DragonMinded/minidragon/schematics/PCBs/2-to-4 Selector/Transistor 2-to-4 Selector.kicad_pcb

## KiCad design schematics/PCBs/2-to-4 Selector/Transistor 2-to-4 Selector.kicad_pcb (2024-02-02)

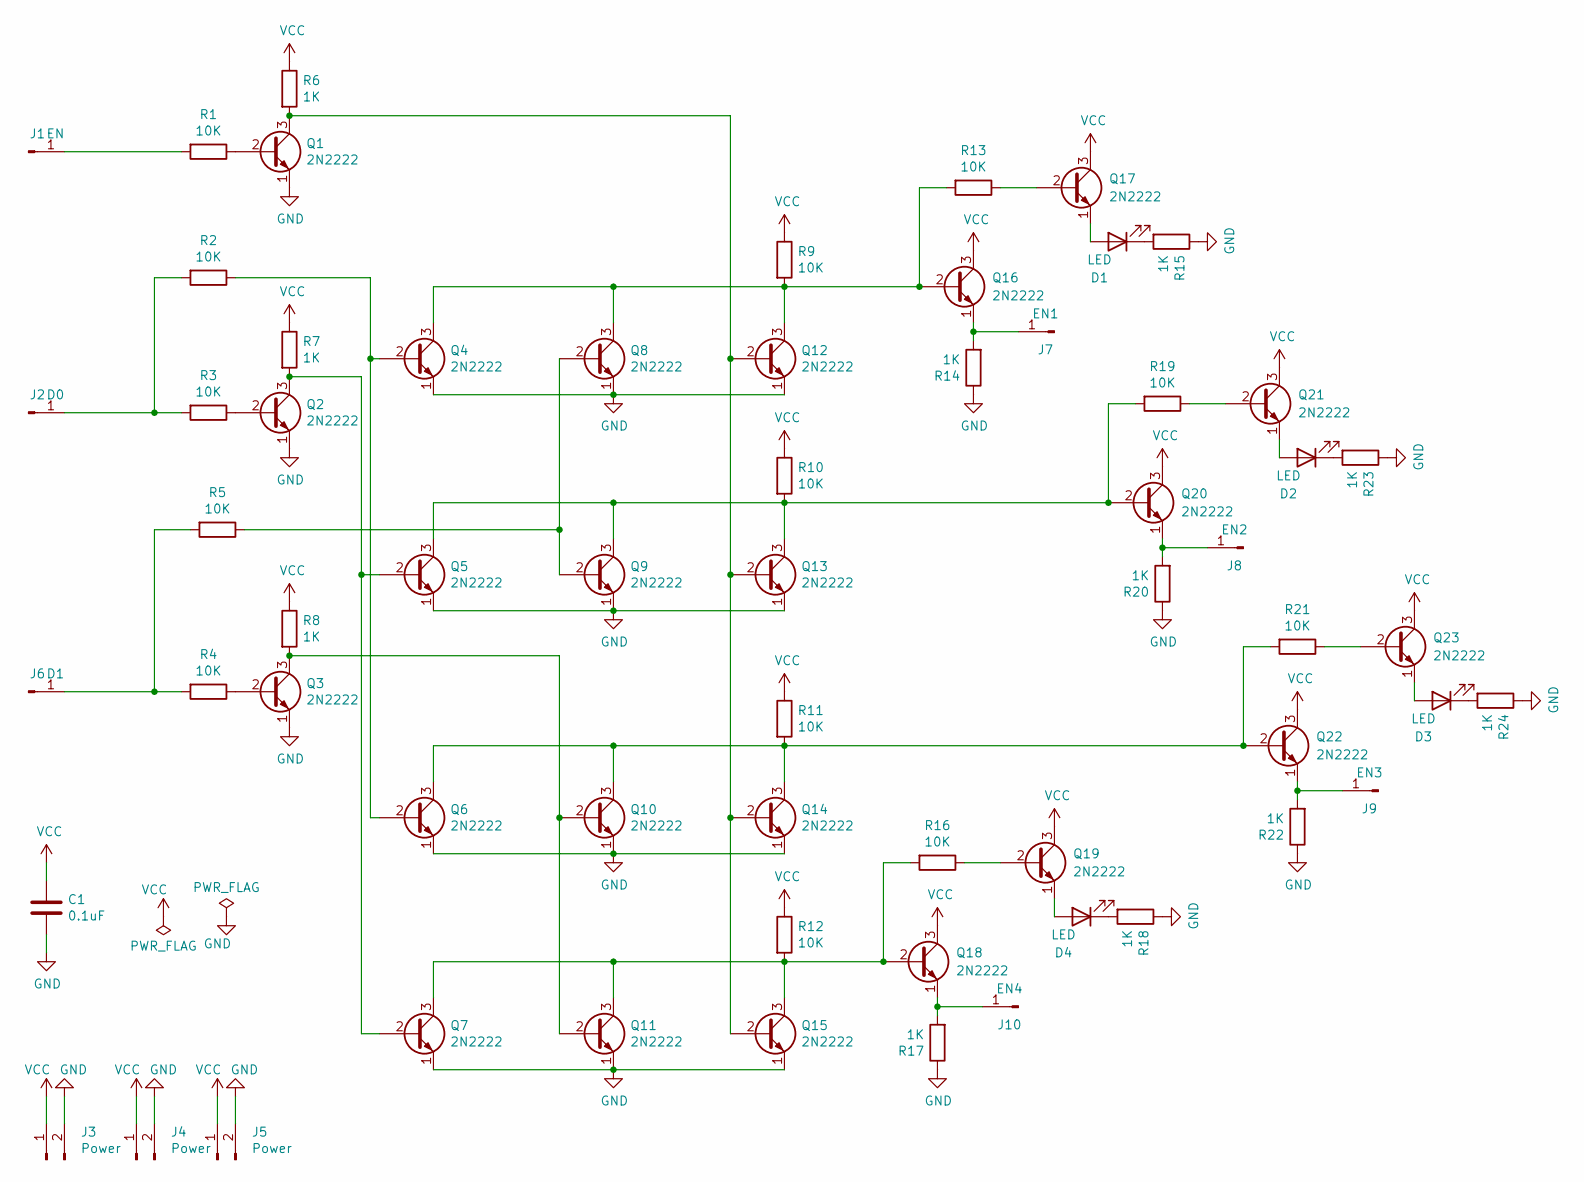
[picture p33: schematic Transistor 2-to-4 Selector.kicad_sch]

Parts:
C1: 0.1uF; C_Disc_D4.3mm_W1.9mm_P5.00mm
D1, D2, D3, D4: LED; LED_D5.0mm
J1: EN; PinHeader_1x01_P2.54mm_Vertical
J2: D0; PinHeader_1x01_P2.54mm_Vertical
J3, J4, J5: Power; PinHeader_1x02_P2.54mm_Vertical
J6: D1; PinHeader_1x01_P2.54mm_Vertical
J7: EN1; PinHeader_1x01_P2.54mm_Vertical
J8: EN2; PinHeader_1x01_P2.54mm_Vertical
J9: EN3; PinHeader_1x01_P2.54mm_Vertical
J10: EN4; PinHeader_1x01_P2.54mm_Vertical
Q1, Q2, Q3, Q4, Q5, Q6, Q7, Q8, Q9, Q10, Q11, Q12, Q13, Q14, Q15, Q16, Q17, Q18, Q19, Q20, Q21, Q22, Q23: 2N2222; TO-92_Inline
R1, R2, R3, R4, R5, R9, R10, R11, R12, R13, R16, R19, R21: 10K; R_Axial_DIN0309_L9.0mm_D3.2mm_P12.70mm_Horizontal
R6, R7, R8, R14, R15, R17, R18, R20, R22, R23, R24: 1K; R_Axial_DIN0309_L9.0mm_D3.2mm_P12.70mm_Horizontal

Connections:
GND: C1.2, J3.2, J4.2, J5.2, Q1.1 (E), Q2.1 (E), Q3.1 (E), Q4.1 (E), Q5.1 (E), Q6.1 (E), Q7.1 (E), Q8.1 (E), Q9.1 (E), Q10.1 (E), Q11.1 (E), Q12.1 (E), Q13.1 (E), Q14.1 (E), Q15.1 (E), R14.1, R15.1, R17.1, R18.1, R20.1, R22.1, R23.1, R24.1
unnamed: D1.2 (A), Q17.1 (E)
unnamed: D1.1 (K), R15.2
unnamed: D2.2 (A), Q21.1 (E)
unnamed: D2.1 (K), R23.2
unnamed: D3.2 (A), Q23.1 (E)
unnamed: D3.1 (K), R24.2
unnamed: D4.2 (A), Q19.1 (E)
unnamed: D4.1 (K), R18.2
unnamed: J1.1, R1.2
unnamed: J2.1, R2.2, R3.2
unnamed: J6.1, R4.2, R5.2
unnamed: J7.1, Q16.1 (E), R14.2
unnamed: J8.1, Q20.1 (E), R20.2
unnamed: J9.1, Q22.1 (E), R22.2
unnamed: J10.1, Q18.1 (E), R17.2
unnamed: Q1.2 (B), R1.1
unnamed: Q1.3 (C), Q12.2 (B), Q13.2 (B), Q14.2 (B), Q15.2 (B), R6.2
unnamed: Q2.2 (B), R3.1
unnamed: Q2.3 (C), Q5.2 (B), Q7.2 (B), R7.2
unnamed: Q3.2 (B), R4.1
unnamed: Q4.2 (B), Q6.2 (B), R2.1
unnamed: Q8.2 (B), Q9.2 (B), R5.1
unnamed: Q3.3 (C), Q10.2 (B), Q11.2 (B), R8.2
unnamed: Q6.3 (C), Q10.3 (C), Q14.3 (C), Q22.2 (B), R11.2, R21.2
unnamed: Q7.3 (C), Q11.3 (C), Q15.3 (C), Q18.2 (B), R12.2, R16.2
unnamed: Q4.3 (C), Q8.3 (C), Q12.3 (C), Q16.2 (B), R9.2, R13.2
unnamed: Q5.3 (C), Q9.3 (C), Q13.3 (C), Q20.2 (B), R10.2, R19.2
unnamed: Q17.2 (B), R13.1
unnamed: Q19.2 (B), R16.1
unnamed: Q21.2 (B), R19.1
unnamed: Q23.2 (B), R21.1
VCC: C1.1, J3.1, J4.1, J5.1, Q16.3 (C), Q17.3 (C), Q18.3 (C), Q19.3 (C), Q20.3 (C), Q21.3 (C), Q22.3 (C), Q23.3 (C), R6.1, R7.1, R8.1, R9.1, R10.1, R11.1, R12.1

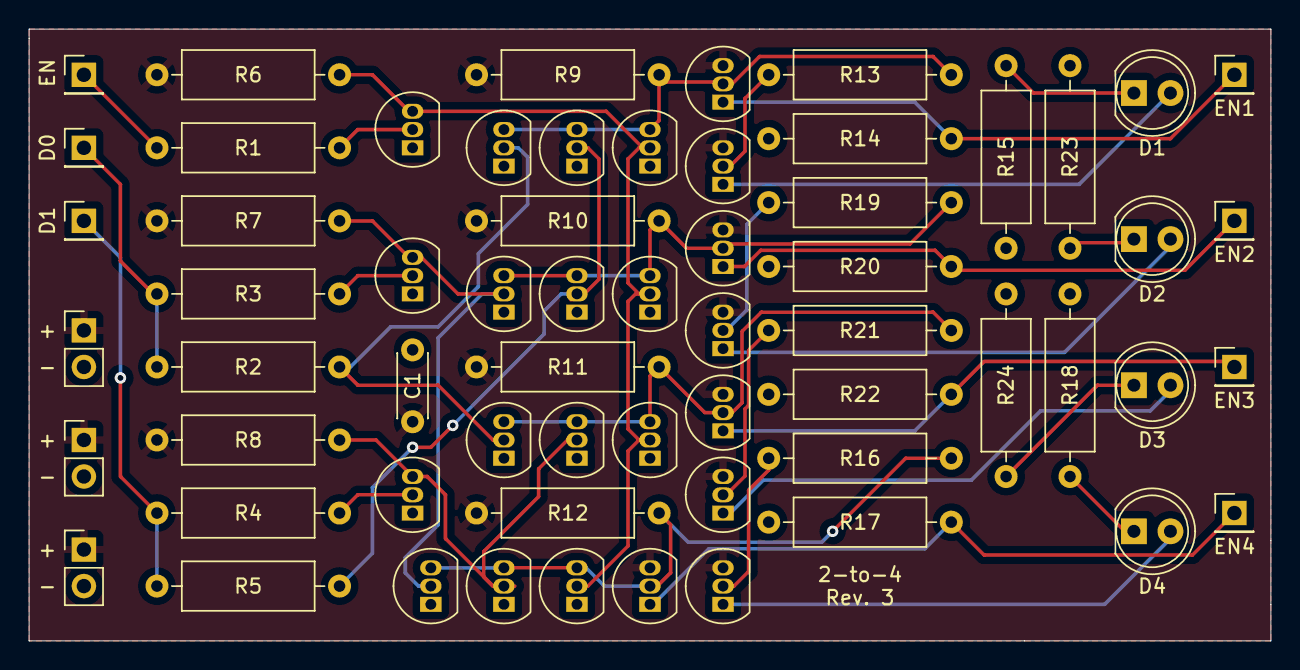
[picture p34: board Transistor 2-to-4 Selector.kicad_pcb from above]

Board: 2 copper layers, 86.4 x 42.5 mm, 62 parts (0 on the bottom side), 33 nets.
