DragonMinded/minidragon/schematics/PCBs/Logic NOT Gate/Transistor NOT Gate.kicad_pcb

## KiCad design schematics/PCBs/Logic NOT Gate/Transistor NOT Gate.kicad_pcb (2024-01-27)

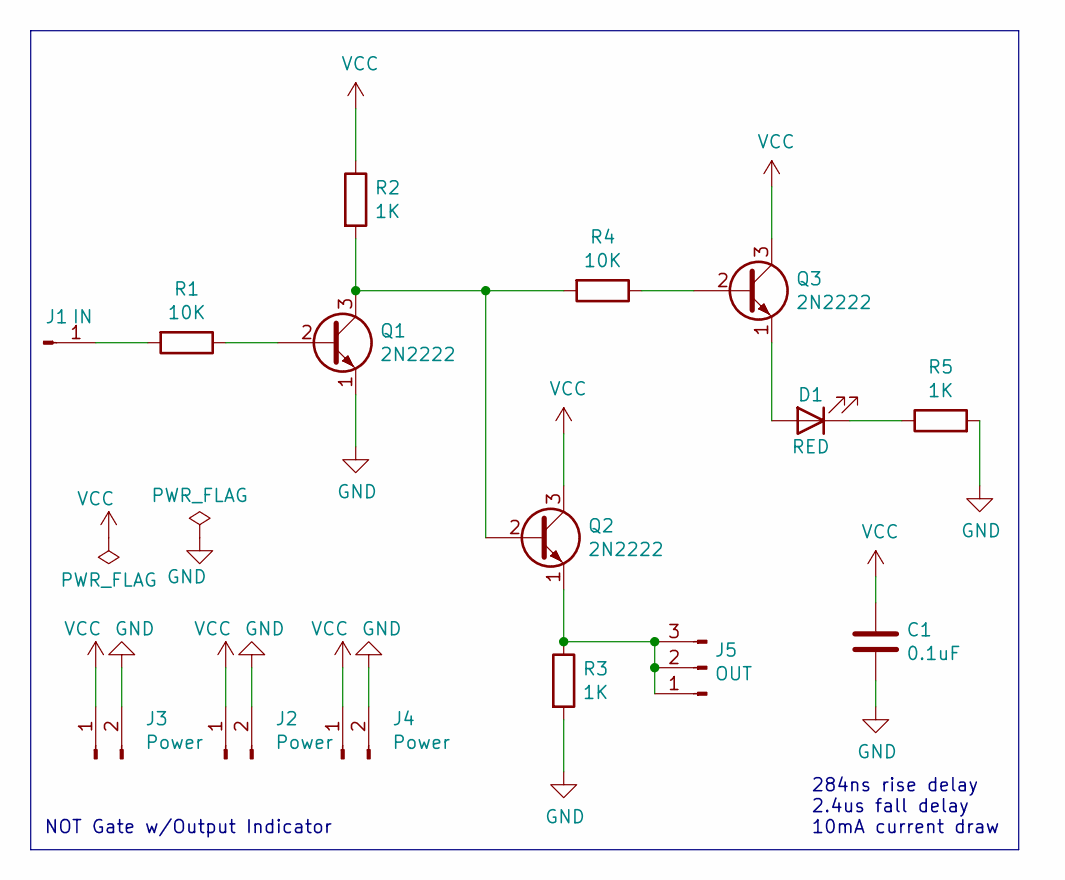
[picture p35: schematic Transistor NOT Gate.kicad_sch, NOT Gate]

Parts:
C1: 0.1uF; C_Disc_D4.3mm_W1.9mm_P5.00mm
D1: RED; LED_D5.0mm
J1: IN; PinHeader_1x01_P2.54mm_Vertical
J2, J3, J4: Power; PinHeader_1x02_P2.54mm_Vertical
J5: OUT; PinHeader_1x03_P2.54mm_Vertical
Q1, Q2, Q3: 2N2222; TO-92_Inline
R1, R4: 10K; R_Axial_DIN0309_L9.0mm_D3.2mm_P12.70mm_Horizontal
R2, R3, R5: 1K; R_Axial_DIN0309_L9.0mm_D3.2mm_P12.70mm_Horizontal

Connections:
GND: C1.2, J2.2, J3.2, J4.2, Q1.1 (E), R3.2, R5.2
unnamed: D1.2 (A), Q3.1 (E)
unnamed: D1.1 (K), R5.1
unnamed: J1.1, R1.2
unnamed: J5.1, J5.2, J5.3, Q2.1 (E), R3.1
unnamed: Q1.2 (B), R1.1
unnamed: Q1.3 (C), Q2.2 (B), R2.2, R4.2
unnamed: Q3.2 (B), R4.1
VCC: C1.1, J2.1, J3.1, J4.1, Q2.3 (C), Q3.3 (C), R2.1

Notes on the sheet:
284ns rise delay 2.4us fall delay 10mA current draw
NOT Gate w/Output Indicator

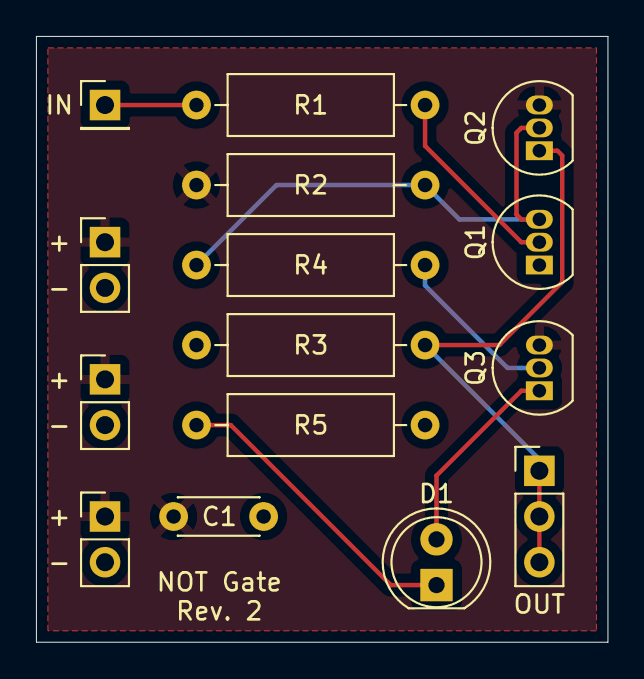
[picture p36: board Transistor NOT Gate.kicad_pcb from above]

Board: 2 copper layers, 31.8 x 33.7 mm, 15 parts (0 on the bottom side), 9 nets.
