DragonMinded/minidragon/schematics/PCBs/8-bit Bus/Transistor 8-bit Bus.kicad_pcb

## KiCad design schematics/PCBs/8-bit Bus/Transistor 8-bit Bus.kicad_pcb (2024-01-27)

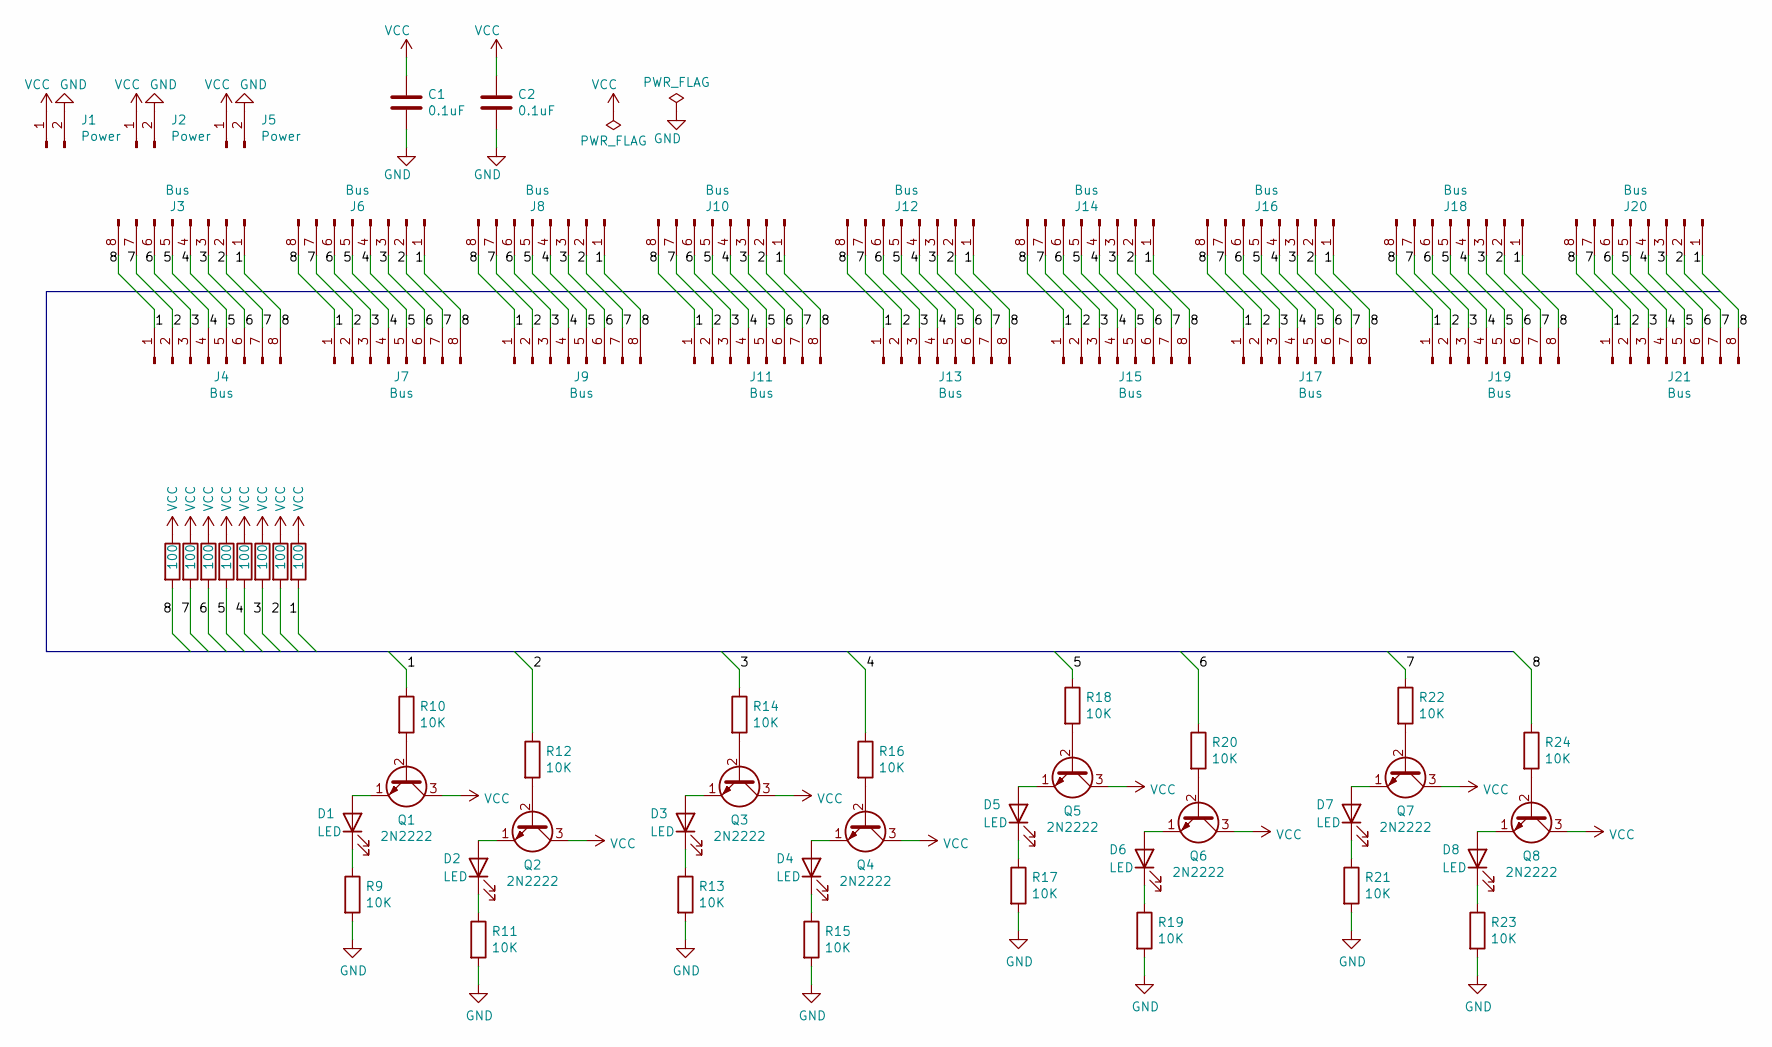
[picture p37: schematic Transistor 8-bit Bus.kicad_sch]

Parts:
C1, C2: 0.1uF; C_Disc_D4.3mm_W1.9mm_P5.00mm
D1, D2, D3, D4, D5, D6, D7, D8: LED; LED_D5.0mm
J1, J2, J5: Power; PinHeader_1x02_P2.54mm_Vertical
J3, J4, J6, J7, J8, J9, J10, J11, J12, J13, J14, J15, J16, J17, J18, J19, J20, J21: Bus; PinHeader_1x08_P2.54mm_Vertical
Q1, Q2, Q3, Q4, Q5, Q6, Q7, Q8: 2N2222; TO-92_Inline
R1, R2, R3, R4, R5, R6, R7, R8: 100; R_Axial_DIN0309_L9.0mm_D3.2mm_P12.70mm_Horizontal
R9, R10, R11, R12, R13, R14, R15, R16, R17, R18, R19, R20, R21, R22, R23, R24: 10K; R_Axial_DIN0309_L9.0mm_D3.2mm_P12.70mm_Horizontal

Connections:
/1: J3.1, J4.1, J6.1, J7.1, J8.1, J9.1, J10.1, J11.1, J12.1, J13.1, J14.1, J15.1, J16.1, J17.1, J18.1, J19.1, J20.1, J21.1, R8.2, R10.1
/2: J3.2, J4.2, J6.2, J7.2, J8.2, J9.2, J10.2, J11.2, J12.2, J13.2, J14.2, J15.2, J16.2, J17.2, J18.2, J19.2, J20.2, J21.2, R7.2, R12.1
/3: J3.3, J4.3, J6.3, J7.3, J8.3, J9.3, J10.3, J11.3, J12.3, J13.3, J14.3, J15.3, J16.3, J17.3, J18.3, J19.3, J20.3, J21.3, R6.2, R14.1
/4: J3.4, J4.4, J6.4, J7.4, J8.4, J9.4, J10.4, J11.4, J12.4, J13.4, J14.4, J15.4, J16.4, J17.4, J18.4, J19.4, J20.4, J21.4, R5.2, R16.1
/5: J3.5, J4.5, J6.5, J7.5, J8.5, J9.5, J10.5, J11.5, J12.5, J13.5, J14.5, J15.5, J16.5, J17.5, J18.5, J19.5, J20.5, J21.5, R4.2, R18.1
/6: J3.6, J4.6, J6.6, J7.6, J8.6, J9.6, J10.6, J11.6, J12.6, J13.6, J14.6, J15.6, J16.6, J17.6, J18.6, J19.6, J20.6, J21.6, R3.2, R20.1
/7: J3.7, J4.7, J6.7, J7.7, J8.7, J9.7, J10.7, J11.7, J12.7, J13.7, J14.7, J15.7, J16.7, J17.7, J18.7, J19.7, J20.7, J21.7, R2.2, R22.1
/8: J3.8, J4.8, J6.8, J7.8, J8.8, J9.8, J10.8, J11.8, J12.8, J13.8, J14.8, J15.8, J16.8, J17.8, J18.8, J19.8, J20.8, J21.8, R1.2, R24.1
GND: C1.2, C2.2, J1.2, J2.2, J5.2, R9.2, R11.2, R13.2, R15.2, R17.2, R19.2, R21.2, R23.2
unnamed: D1.2 (A), Q1.1 (E)
unnamed: D1.1 (K), R9.1
unnamed: D2.2 (A), Q2.1 (E)
unnamed: D2.1 (K), R11.1
unnamed: D3.2 (A), Q3.1 (E)
unnamed: D3.1 (K), R13.1
unnamed: D4.2 (A), Q4.1 (E)
unnamed: D4.1 (K), R15.1
unnamed: D5.2 (A), Q5.1 (E)
unnamed: D5.1 (K), R17.1
unnamed: D6.2 (A), Q6.1 (E)
unnamed: D6.1 (K), R19.1
unnamed: D7.2 (A), Q7.1 (E)
unnamed: D7.1 (K), R21.1
unnamed: D8.2 (A), Q8.1 (E)
unnamed: D8.1 (K), R23.1
unnamed: Q1.2 (B), R10.2
unnamed: Q2.2 (B), R12.2
unnamed: Q3.2 (B), R14.2
unnamed: Q4.2 (B), R16.2
unnamed: Q5.2 (B), R18.2
unnamed: Q6.2 (B), R20.2
unnamed: Q7.2 (B), R22.2
unnamed: Q8.2 (B), R24.2
VCC: C1.1, C2.1, J1.1, J2.1, J5.1, Q1.3 (C), Q2.3 (C), Q3.3 (C), Q4.3 (C), Q5.3 (C), Q6.3 (C), Q7.3 (C), Q8.3 (C), R1.1, R2.1, R3.1, R4.1, R5.1, R6.1, R7.1, R8.1

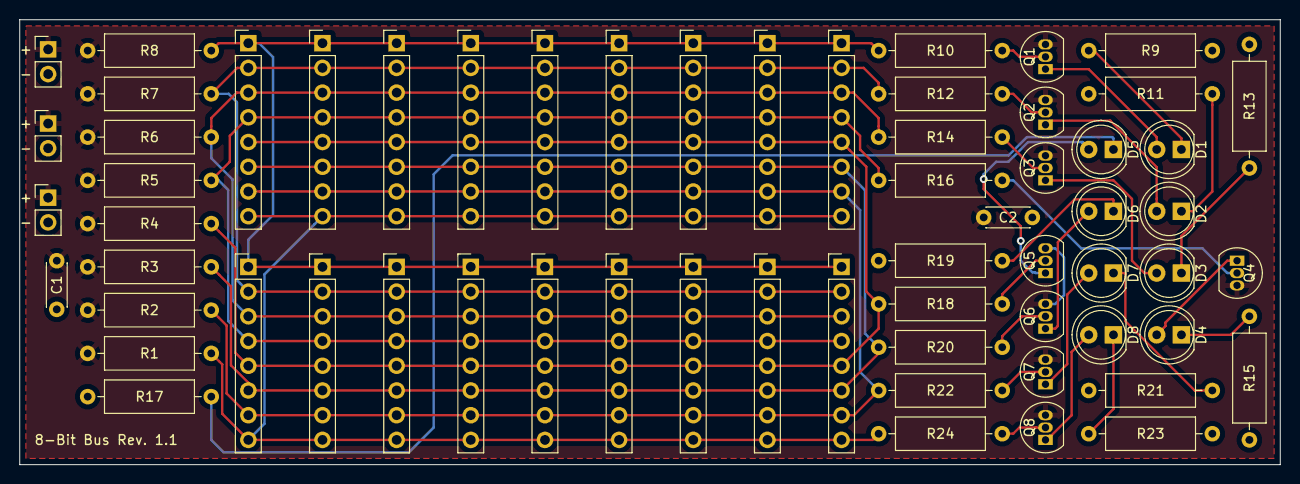
[picture p38: board Transistor 8-bit Bus.kicad_pcb from above]

Board: 2 copper layers, 129.5 x 45.7 mm, 63 parts (0 on the bottom side), 34 nets.
