DragonMinded/minidragon/schematics/PCBs/8-bit Bus Output XOR/8-bit Bus Output XOR.kicad_pcb

## KiCad design schematics/PCBs/8-bit Bus Output XOR/8-bit Bus Output XOR.kicad_pcb (2024-01-27)

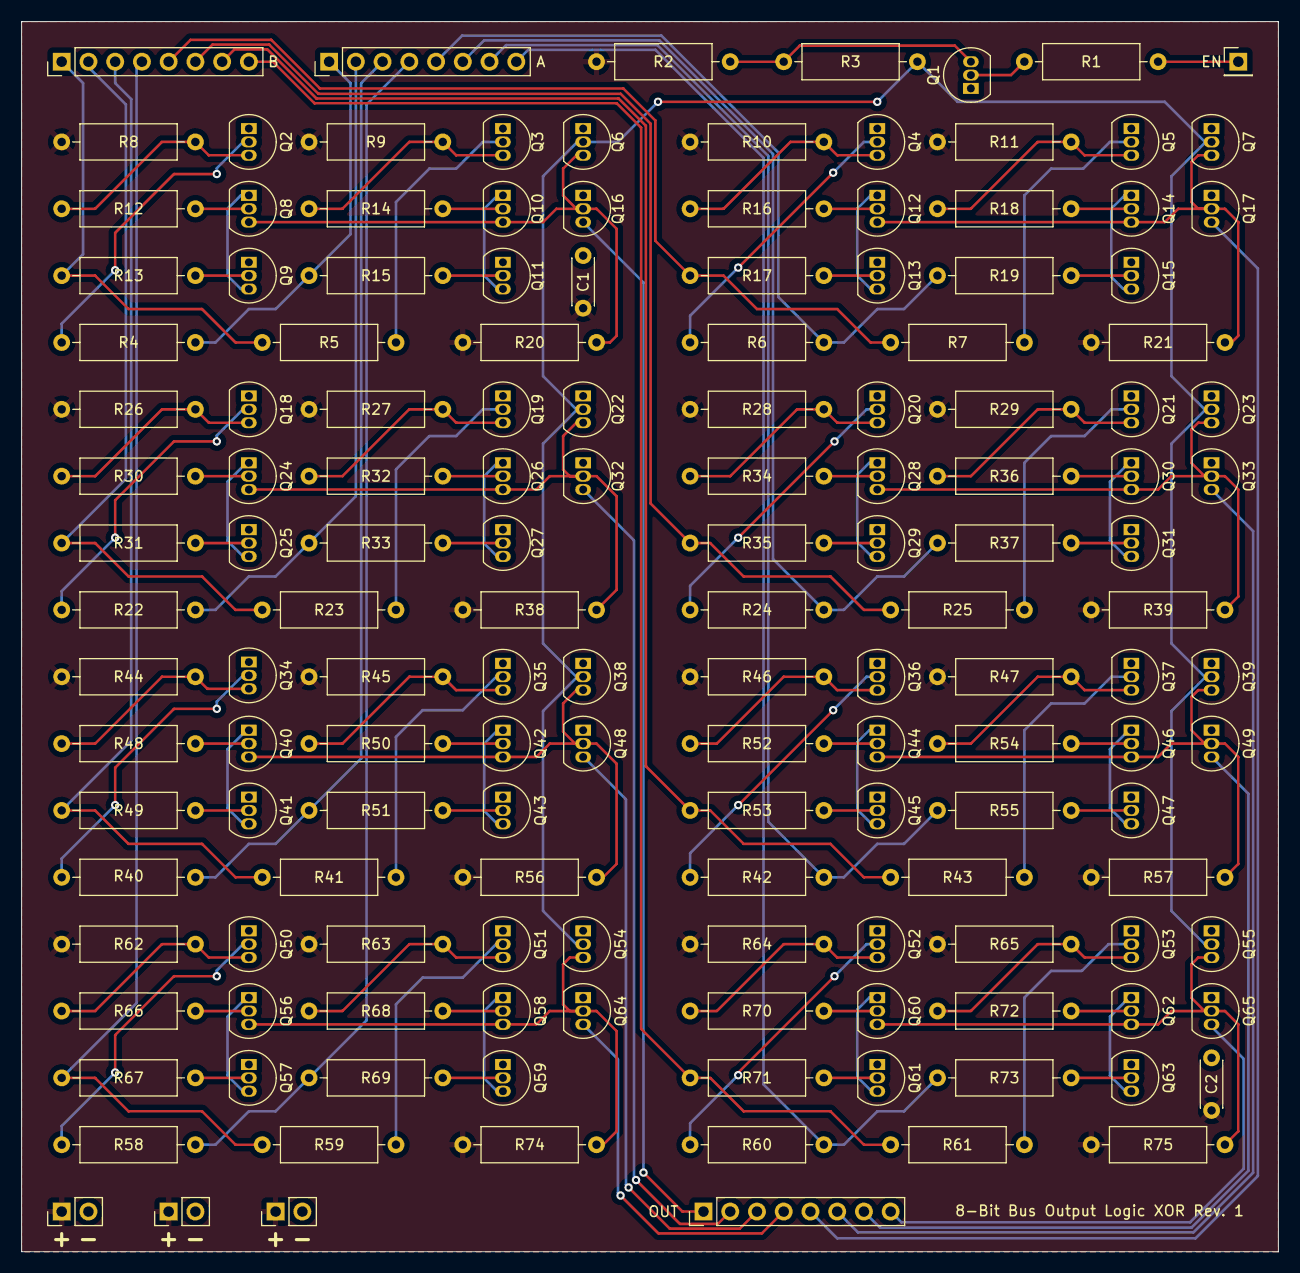
[picture p39: board 8-bit Bus Output XOR.kicad_pcb from above]

Board: 2 copper layers, 119.4 x 116.8 mm, 149 parts (0 on the bottom side), 118 nets.

Parts:
C1, C2: 0.1uF; C_Disc_D4.3mm_W1.9mm_P5.00mm
J1: EN; PinHeader_1x01_P2.54mm_Vertical
J2: A; PinHeader_1x08_P2.54mm_Vertical
J3: B; PinHeader_1x08_P2.54mm_Vertical
J4: OUT; PinHeader_1x08_P2.54mm_Vertical
J5, J6, J7: POWER; PinHeader_1x02_P2.54mm_Vertical
Q1, Q2, Q3, Q4, Q5, Q6, Q7, Q8, Q9, Q10, Q11, Q12, Q13, Q14, Q15, Q16, Q17, Q18, Q19, Q20, Q21, Q22, Q23, Q24, Q25, Q26, Q27, Q28, Q29, Q30, Q31, Q32, Q33, Q34, Q35, Q36, Q37, Q38, Q39, Q40, Q41, Q42, Q43, Q44, Q45, Q46, Q47, Q48, Q49, Q50, Q51, Q52, Q53, Q54, Q55, Q56, Q57, Q58, Q59, Q60, Q61, Q62, Q63, Q64, Q65: 2N2222; TO-92_Inline
R1, R4, R5, R6, R7, R12, R13, R14, R15, R16, R17, R18, R19, R22, R23, R24, R25, R30, R31, R32, R33, R34, R35, R36, R37, R40, R41, R42, R43, R48, R49, R50, R51, R52, R53, R54, R55, R58, R59, R60, R61, R66, R67, R68, R69, R70, R71, R72, R73: 10K; R_Axial_DIN0309_L9.0mm_D3.2mm_P12.70mm_Horizontal
R2, R8, R9, R10, R11, R20, R21, R26, R27, R28, R29, R38, R39, R44, R45, R46, R47, R56, R57, R62, R63, R64, R65, R74, R75: 1K; R_Axial_DIN0309_L9.0mm_D3.2mm_P12.70mm_Horizontal
R3: 100; R_Axial_DIN0309_L9.0mm_D3.2mm_P12.70mm_Horizontal

Connections:
/A1: J2.1, R4.2, R15.2
/A2: J2.2, R22.2, R33.2
/A3: J2.3, R40.2, R51.2
/A4: J2.4, R58.2, R69.2
/A5: J2.5, R6.2, R19.2
/A6: J2.6, R24.2, R37.2
/A7: J2.7, R42.2, R55.2
/A8: J2.8, R60.2, R73.2
/B1: J3.1, R5.2, R13.2
/B2: J3.2, R23.2, R31.2
/B3: J3.3, R41.2, R49.2
/B4: J3.4, R59.2, R67.2
/B5: J3.5, R7.2, R17.2
/B6: J3.6, R25.2, R35.2
/B7: J3.7, R43.2, R53.2
/B8: J3.8, R61.2, R71.2
/EN_INT: Q6.2 (B), Q7.2 (B), Q22.2 (B), Q23.2 (B), Q38.2 (B), Q39.2 (B), Q54.2 (B), Q55.2 (B), R3.1
/O1: J4.1, Q16.3 (C)
/O2: J4.2, Q32.3 (C)
/O3: J4.3, Q48.3 (C)
/O4: J4.4, Q64.3 (C)
/O5: J4.5, Q17.3 (C)
/O6: J4.6, Q33.3 (C)
/O7: J4.7, Q49.3 (C)
/O8: J4.8, Q65.3 (C)
GND: C1.2, C2.2, J5.2, J6.2, J7.2, Q1.1 (E), Q2.1 (E), Q3.1 (E), Q4.1 (E), Q5.1 (E), Q6.1 (E), Q7.1 (E), Q9.1 (E), Q11.1 (E), Q13.1 (E), Q15.1 (E), Q16.1 (E), Q17.1 (E), Q18.1 (E), Q19.1 (E), Q20.1 (E), Q21.1 (E), Q22.1 (E), Q23.1 (E), Q25.1 (E), Q27.1 (E), Q29.1 (E), Q31.1 (E), Q32.1 (E), Q33.1 (E), Q34.1 (E), Q35.1 (E), Q36.1 (E), Q37.1 (E), Q38.1 (E), Q39.1 (E), Q41.1 (E), Q43.1 (E), Q45.1 (E), Q47.1 (E), Q48.1 (E), Q49.1 (E), Q50.1 (E), Q51.1 (E), Q52.1 (E), Q53.1 (E), Q54.1 (E), Q55.1 (E), Q57.1 (E), Q59.1 (E), Q61.1 (E), Q63.1 (E), Q64.1 (E), Q65.1 (E)
unnamed: J1.1, R1.2
unnamed: Q1.2 (B), R1.1
unnamed: Q1.3 (C), R2.1, R3.2
unnamed: Q2.2 (B), R4.1
unnamed: Q2.3 (C), R8.2, R12.2
unnamed: Q3.2 (B), R5.1
unnamed: Q3.3 (C), R9.2, R14.2
unnamed: Q4.2 (B), R6.1
unnamed: Q4.3 (C), R10.2, R16.2
unnamed: Q5.2 (B), R7.1
unnamed: Q5.3 (C), R11.2, R18.2
unnamed: Q8.2 (B), R12.1
unnamed: Q8.1 (E), Q9.3 (C)
unnamed: Q9.2 (B), R13.1
unnamed: Q10.2 (B), R14.1
unnamed: Q6.3 (C), Q8.3 (C), Q10.3 (C), Q16.2 (B), R20.1
unnamed: Q10.1 (E), Q11.3 (C)
unnamed: Q11.2 (B), R15.1
unnamed: Q12.2 (B), R16.1
unnamed: Q7.3 (C), Q12.3 (C), Q14.3 (C), Q17.2 (B), R21.1
unnamed: Q12.1 (E), Q13.3 (C)
unnamed: Q13.2 (B), R17.1
unnamed: Q14.2 (B), R18.1
unnamed: Q14.1 (E), Q15.3 (C)
unnamed: Q15.2 (B), R19.1
unnamed: Q18.2 (B), R22.1
unnamed: Q18.3 (C), R26.2, R30.2
unnamed: Q19.2 (B), R23.1
unnamed: Q19.3 (C), R27.2, R32.2
unnamed: Q20.2 (B), R24.1
unnamed: Q20.3 (C), R28.2, R34.2
unnamed: Q21.2 (B), R25.1
unnamed: Q21.3 (C), R29.2, R36.2
unnamed: Q22.3 (C), Q24.3 (C), Q26.3 (C), Q32.2 (B), R38.1
unnamed: Q23.3 (C), Q28.3 (C), Q30.3 (C), Q33.2 (B), R39.1
unnamed: Q24.2 (B), R30.1
unnamed: Q24.1 (E), Q25.3 (C)
unnamed: Q25.2 (B), R31.1
unnamed: Q26.2 (B), R32.1
unnamed: Q26.1 (E), Q27.3 (C)
unnamed: Q27.2 (B), R33.1
unnamed: Q28.2 (B), R34.1
unnamed: Q28.1 (E), Q29.3 (C)
unnamed: Q29.2 (B), R35.1
unnamed: Q30.2 (B), R36.1
unnamed: Q30.1 (E), Q31.3 (C)
unnamed: Q31.2 (B), R37.1
unnamed: Q34.2 (B), R40.1
unnamed: Q34.3 (C), R44.2, R48.2
unnamed: Q35.2 (B), R41.1
unnamed: Q35.3 (C), R45.2, R50.2
unnamed: Q36.2 (B), R42.1
unnamed: Q36.3 (C), R46.2, R52.2
unnamed: Q37.2 (B), R43.1
unnamed: Q37.3 (C), R47.2, R54.2
unnamed: Q38.3 (C), Q40.3 (C), Q42.3 (C), Q48.2 (B), R56.1
unnamed: Q39.3 (C), Q44.3 (C), Q46.3 (C), Q49.2 (B), R57.1
unnamed: Q40.2 (B), R48.1
unnamed: Q40.1 (E), Q41.3 (C)
unnamed: Q41.2 (B), R49.1
unnamed: Q42.2 (B), R50.1
unnamed: Q42.1 (E), Q43.3 (C)
unnamed: Q43.2 (B), R51.1
unnamed: Q44.2 (B), R52.1
unnamed: Q44.1 (E), Q45.3 (C)
unnamed: Q45.2 (B), R53.1
unnamed: Q46.2 (B), R54.1
unnamed: Q46.1 (E), Q47.3 (C)
unnamed: Q47.2 (B), R55.1
unnamed: Q50.2 (B), R58.1
unnamed: Q50.3 (C), R62.2, R66.2
unnamed: Q51.2 (B), R59.1
unnamed: Q51.3 (C), R63.2, R68.2
unnamed: Q52.2 (B), R60.1
unnamed: Q52.3 (C), R64.2, R70.2
unnamed: Q53.2 (B), R61.1
unnamed: Q53.3 (C), R65.2, R72.2
unnamed: Q54.3 (C), Q56.3 (C), Q58.3 (C), Q64.2 (B), R74.1
unnamed: Q55.3 (C), Q60.3 (C), Q62.3 (C), Q65.2 (B), R75.1
unnamed: Q56.2 (B), R66.1
unnamed: Q56.1 (E), Q57.3 (C)
unnamed: Q57.2 (B), R67.1
unnamed: Q58.2 (B), R68.1
unnamed: Q58.1 (E), Q59.3 (C)
unnamed: Q59.2 (B), R69.1
unnamed: Q60.2 (B), R70.1
unnamed: Q60.1 (E), Q61.3 (C)
unnamed: Q61.2 (B), R71.1
unnamed: Q62.2 (B), R72.1
unnamed: Q62.1 (E), Q63.3 (C)
unnamed: Q63.2 (B), R73.1
VCC: C1.1, C2.1, J5.1, J6.1, J7.1, R2.2, R8.1, R9.1, R10.1, R11.1, R20.2, R21.2, R26.1, R27.1, R28.1, R29.1, R38.2, R39.2, R44.1, R45.1, R46.1, R47.1, R56.2, R57.2, R62.1, R63.1, R64.1, R65.1, R74.2, R75.2
