DragonMinded/minidragon/schematics/PCBs/Carry Out Selector/Carry Out Selector.kicad_pcb

## KiCad design schematics/PCBs/Carry Out Selector/Carry Out Selector.kicad_pcb (2024-01-27)

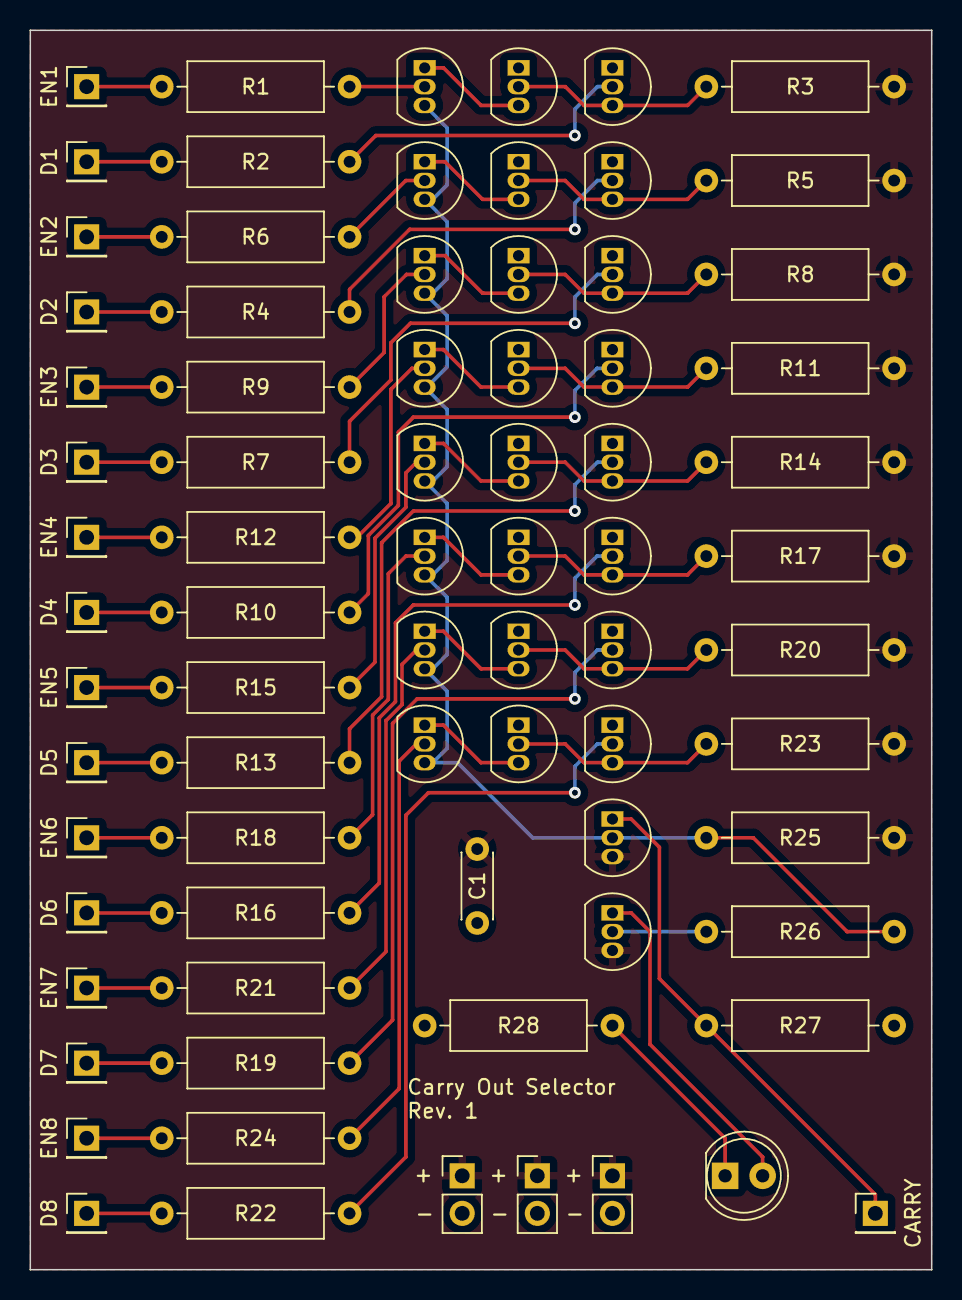
[picture p40: board Carry Out Selector.kicad_pcb from above]

Board: 2 copper layers, 61.0 x 83.8 mm, 76 parts (0 on the bottom side), 55 nets.

Parts:
C1: 0.1uF; C_Disc_D4.3mm_W1.9mm_P5.00mm
D1: LED; LED_D5.0mm
J1, J2, J3: POWER; PinHeader_1x02_P2.54mm_Vertical
J4: D1; PinHeader_1x01_P2.54mm_Vertical
J5: EN1; PinHeader_1x01_P2.54mm_Vertical
J6: D2; PinHeader_1x01_P2.54mm_Vertical
J7: EN2; PinHeader_1x01_P2.54mm_Vertical
J8: D3; PinHeader_1x01_P2.54mm_Vertical
J9: EN3; PinHeader_1x01_P2.54mm_Vertical
J10: D4; PinHeader_1x01_P2.54mm_Vertical
J11: EN4; PinHeader_1x01_P2.54mm_Vertical
J12: D5; PinHeader_1x01_P2.54mm_Vertical
J13: EN5; PinHeader_1x01_P2.54mm_Vertical
J14: D6; PinHeader_1x01_P2.54mm_Vertical
J15: EN6; PinHeader_1x01_P2.54mm_Vertical
J16: D7; PinHeader_1x01_P2.54mm_Vertical
J17: EN7; PinHeader_1x01_P2.54mm_Vertical
J18: D8; PinHeader_1x01_P2.54mm_Vertical
J19: EN8; PinHeader_1x01_P2.54mm_Vertical
J20: CARRY; PinHeader_1x01_P2.54mm_Vertical
Q1, Q2, Q3, Q4, Q5, Q6, Q7, Q8, Q9, Q10, Q11, Q12, Q13, Q14, Q15, Q16, Q17, Q18, Q19, Q20, Q21, Q22, Q23, Q24, Q25, Q26: 2N2222; TO-92_Inline
R1, R2, R4, R6, R7, R9, R10, R12, R13, R15, R16, R18, R19, R21, R22, R24, R26: 10K; R_Axial_DIN0309_L9.0mm_D3.2mm_P12.70mm_Horizontal
R3, R5, R8, R11, R14, R17, R20, R23, R25, R27, R28: 1K; R_Axial_DIN0309_L9.0mm_D3.2mm_P12.70mm_Horizontal

Connections:
/COMB_BUS: Q1.3 (C), Q5.3 (C), Q8.3 (C), Q11.3 (C), Q14.3 (C), Q17.3 (C), Q20.3 (C), Q23.3 (C), Q25.2 (B), R25.1, R26.2
GND: C1.2, J1.2, J2.2, J3.2, Q2.1 (E), Q3.1 (E), Q4.1 (E), Q6.1 (E), Q7.1 (E), Q9.1 (E), Q10.1 (E), Q12.1 (E), Q13.1 (E), Q15.1 (E), Q16.1 (E), Q18.1 (E), Q19.1 (E), Q21.1 (E), Q22.1 (E), Q24.1 (E), R27.1, R28.1
unnamed: D1.2 (A), Q26.1 (E)
unnamed: D1.1 (K), R28.2
unnamed: J4.1, R2.2
unnamed: J5.1, R1.2
unnamed: J6.1, R4.2
unnamed: J7.1, R6.2
unnamed: J8.1, R7.2
unnamed: J9.1, R9.2
unnamed: J10.1, R10.2
unnamed: J11.1, R12.2
unnamed: J12.1, R13.2
unnamed: J13.1, R15.2
unnamed: J14.1, R16.2
unnamed: J15.1, R18.2
unnamed: J16.1, R19.2
unnamed: J17.1, R21.2
unnamed: J18.1, R22.2
unnamed: J19.1, R24.2
unnamed: J20.1, Q25.1 (E), R27.2
unnamed: Q1.2 (B), R1.1
unnamed: Q1.1 (E), Q2.3 (C)
unnamed: Q2.2 (B), Q3.3 (C), R3.1
unnamed: Q3.2 (B), R2.1
unnamed: Q4.2 (B), R4.1
unnamed: Q4.3 (C), Q6.2 (B), R5.1
unnamed: Q5.2 (B), R6.1
unnamed: Q5.1 (E), Q6.3 (C)
unnamed: Q7.2 (B), R7.1
unnamed: Q7.3 (C), Q9.2 (B), R8.1
unnamed: Q8.2 (B), R9.1
unnamed: Q8.1 (E), Q9.3 (C)
unnamed: Q10.2 (B), R10.1
unnamed: Q10.3 (C), Q12.2 (B), R11.1
unnamed: Q11.2 (B), R12.1
unnamed: Q11.1 (E), Q12.3 (C)
unnamed: Q13.2 (B), R13.1
unnamed: Q13.3 (C), Q15.2 (B), R14.1
unnamed: Q14.2 (B), R15.1
unnamed: Q14.1 (E), Q15.3 (C)
unnamed: Q16.2 (B), R16.1
unnamed: Q16.3 (C), Q18.2 (B), R17.1
unnamed: Q17.2 (B), R18.1
unnamed: Q17.1 (E), Q18.3 (C)
unnamed: Q19.2 (B), R19.1
unnamed: Q19.3 (C), Q21.2 (B), R20.1
unnamed: Q20.2 (B), R21.1
unnamed: Q20.1 (E), Q21.3 (C)
unnamed: Q22.2 (B), R22.1
unnamed: Q22.3 (C), Q24.2 (B), R23.1
unnamed: Q23.2 (B), R24.1
unnamed: Q23.1 (E), Q24.3 (C)
unnamed: Q26.2 (B), R26.1
VCC: C1.1, J1.1, J2.1, J3.1, Q25.3 (C), Q26.3 (C), R3.2, R5.2, R8.2, R11.2, R14.2, R17.2, R20.2, R23.2, R25.2
