DragonMinded/minidragon/schematics/PCBs/D Flip Flop/Transistor D Flip Flop.kicad_pcb

## KiCad design schematics/PCBs/D Flip Flop/Transistor D Flip Flop.kicad_pcb (2024-01-27)

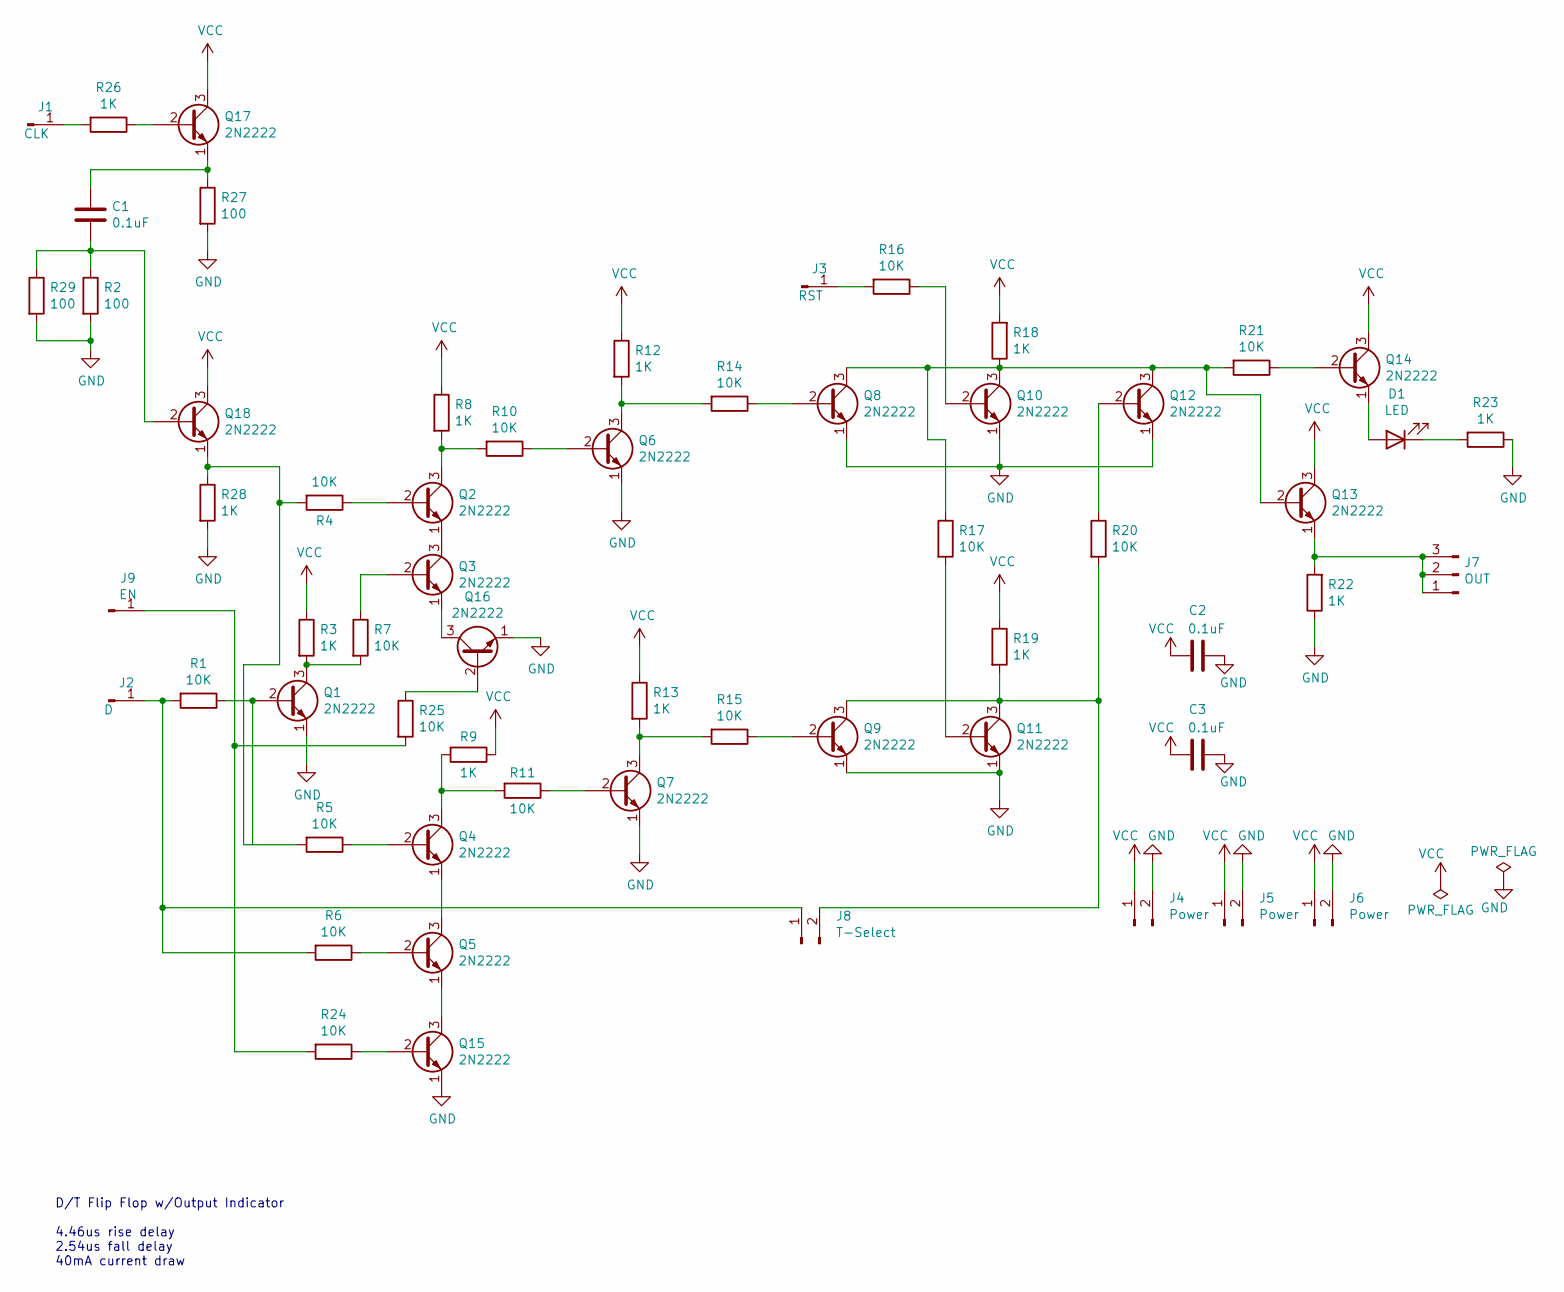
[picture p41: schematic Transistor D Flip Flop.kicad_sch, D Flip Flop]

Parts:
C1, C2, C3: 0.1uF; C_Disc_D4.3mm_W1.9mm_P5.00mm
D1: LED; LED_D5.0mm
J1: CLK; PinHeader_1x01_P2.54mm_Vertical
J2: D; PinHeader_1x01_P2.54mm_Vertical
J3: RST; PinHeader_1x01_P2.54mm_Vertical
J4, J5, J6: Power; PinHeader_1x02_P2.54mm_Vertical
J7: OUT; PinHeader_1x03_P2.54mm_Vertical
J8: T-Select; PinHeader_1x02_P2.54mm_Vertical
J9: EN; PinHeader_1x01_P2.54mm_Vertical
Q1, Q2, Q3, Q4, Q5, Q6, Q7, Q8, Q9, Q10, Q11, Q12, Q13, Q14, Q15, Q16, Q17, Q18: 2N2222; TO-92_Inline
R1, R4, R5, R6, R7, R10, R11, R14, R15, R16, R17, R20, R21, R24, R25: 10K; R_Axial_DIN0309_L9.0mm_D3.2mm_P12.70mm_Horizontal
R2, R27, R29: 100; R_Axial_DIN0309_L9.0mm_D3.2mm_P12.70mm_Horizontal
R3, R8, R9, R12, R13, R18, R19, R22, R23, R26, R28: 1K; R_Axial_DIN0309_L9.0mm_D3.2mm_P12.70mm_Horizontal

Connections:
GND: C2.1, C3.1, J4.2, J5.2, J6.2, Q1.1 (E), Q6.1 (E), Q7.1 (E), Q8.1 (E), Q9.1 (E), Q10.1 (E), Q11.1 (E), Q12.1 (E), Q15.1 (E), Q16.1 (E), R2.2, R22.1, R23.1, R27.2, R28.2, R29.2
unnamed: D1.2 (A), Q14.1 (E)
unnamed: D1.1 (K), R23.2
unnamed: J1.1, R26.2
unnamed: J2.1, J8.1, R1.2, R6.2
unnamed: J3.1, R16.2
unnamed: J7.1, J7.2, J7.3, Q13.1 (E), R22.2
unnamed: J8.2, Q9.3 (C), Q11.3 (C), R19.2, R20.2
unnamed: J9.1, R24.2, R25.2
unnamed: Q1.2 (B), R1.1
unnamed: Q1.3 (C), R3.2, R7.2
unnamed: Q2.2 (B), R4.1
unnamed: Q2.3 (C), R8.2, R10.2
unnamed: Q2.1 (E), Q3.3 (C)
unnamed: Q3.2 (B), R7.1
unnamed: Q4.2 (B), R5.1
unnamed: Q4.3 (C), R9.2, R11.2
unnamed: Q4.1 (E), Q5.3 (C)
unnamed: Q5.2 (B), R6.1
unnamed: Q6.2 (B), R10.1
unnamed: Q6.3 (C), R12.2, R14.2
unnamed: Q7.2 (B), R11.1
unnamed: Q7.3 (C), R13.2, R15.2
unnamed: Q8.2 (B), R14.1
unnamed: Q9.2 (B), R15.1
unnamed: Q10.2 (B), R16.1
unnamed: Q8.3 (C), Q10.3 (C), Q12.3 (C), Q13.2 (B), R17.1, R18.1, R21.2
unnamed: Q11.2 (B), R17.2
unnamed: Q12.2 (B), R20.1
unnamed: Q14.2 (B), R21.1
unnamed: Q15.2 (B), R24.1
unnamed: Q5.1 (E), Q15.3 (C)
unnamed: Q16.2 (B), R25.1
unnamed: Q3.1 (E), Q16.3 (C)
unnamed: Q17.2 (B), R26.1
unnamed: C1.1, Q17.1 (E), R27.1
unnamed: C1.2, Q18.2 (B), R2.1, R29.1
unnamed: Q18.1 (E), R4.2, R5.2, R28.1
VCC: C2.2, C3.2, J4.1, J5.1, J6.1, Q13.3 (C), Q14.3 (C), Q17.3 (C), Q18.3 (C), R3.1, R8.1, R9.1, R12.1, R13.1, R18.2, R19.1

Notes on the sheet:
D/T Flip Flop w/Output Indicator 4.46us rise delay 2.54us fall delay 40mA current draw

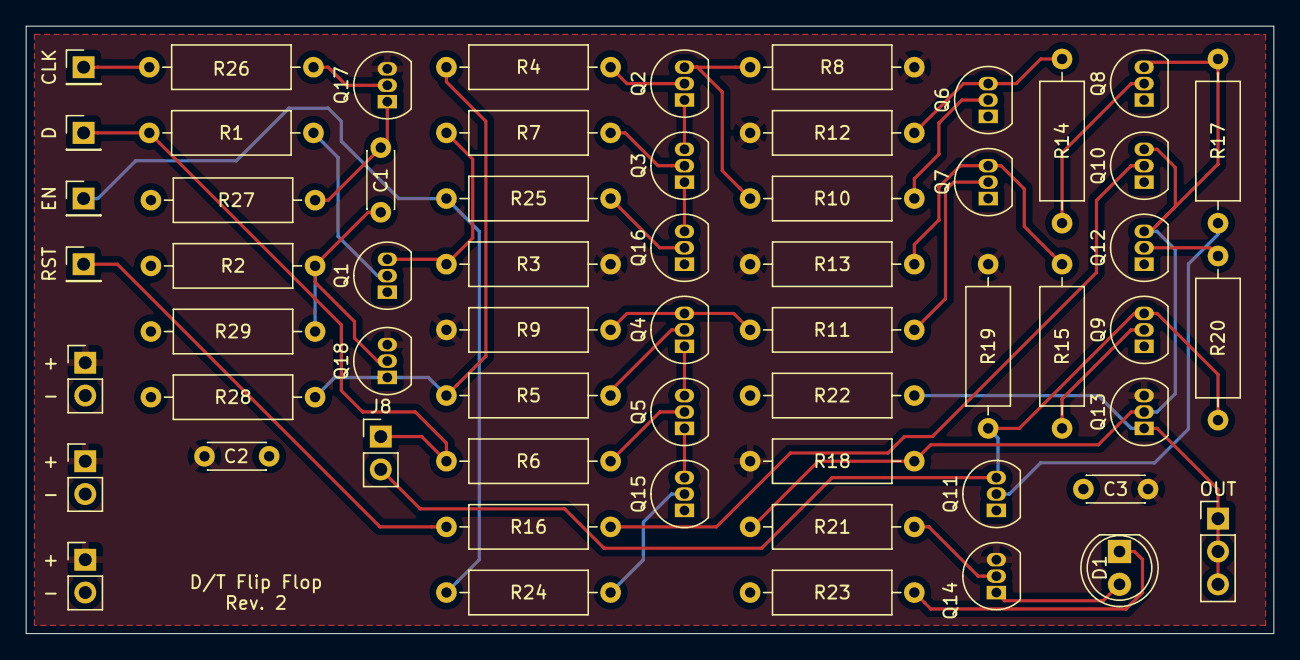
[picture p42: board Transistor D Flip Flop.kicad_pcb from above]

Board: 2 copper layers, 96.5 x 47.0 mm, 60 parts (0 on the bottom side), 39 nets.
