DragonMinded/minidragon/schematics/PCBs/Zero Detector/Zero Detector.kicad_pcb

## KiCad design schematics/PCBs/Zero Detector/Zero Detector.kicad_pcb (2024-01-27)

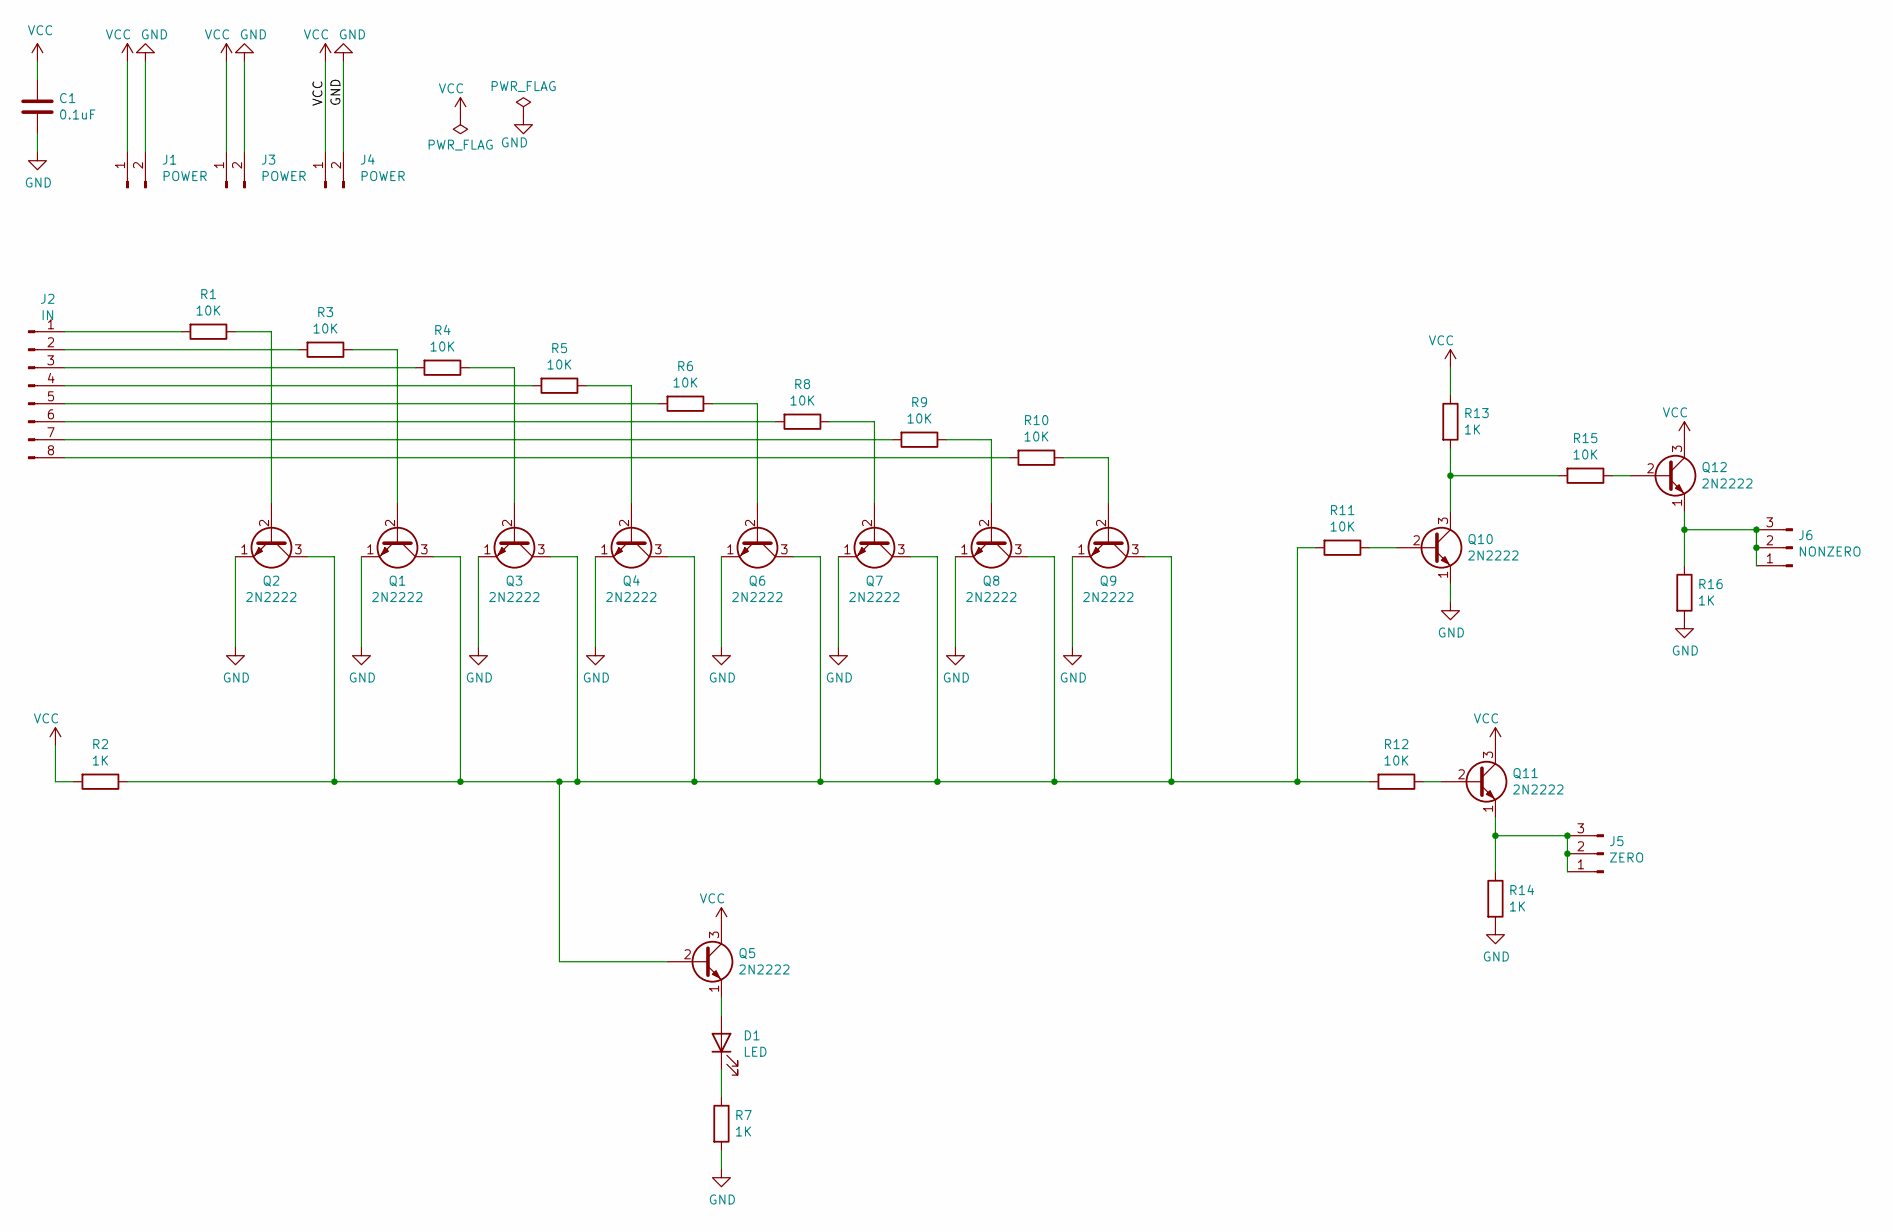
[picture p43: schematic Zero Detector.kicad_sch]

Parts:
C1: 0.1uF; C_Disc_D4.3mm_W1.9mm_P5.00mm
D1: LED; LED_D5.0mm
J1, J3, J4: POWER; PinHeader_1x02_P2.54mm_Vertical
J2: IN; PinHeader_1x08_P2.54mm_Vertical
J5: ZERO; PinHeader_1x03_P2.54mm_Vertical
J6: NONZERO; PinHeader_1x03_P2.54mm_Vertical
Q1, Q2, Q3, Q4, Q5, Q6, Q7, Q8, Q9, Q10, Q11, Q12: 2N2222; TO-92_Inline
R1, R3, R4, R5, R6, R8, R9, R10, R11, R12, R15: 10K; R_Axial_DIN0309_L9.0mm_D3.2mm_P12.70mm_Horizontal
R2, R7, R13, R14, R16: 1K; R_Axial_DIN0309_L9.0mm_D3.2mm_P12.70mm_Horizontal

Connections:
GND: C1.2, J1.2, J3.2, J4.2, Q1.1 (E), Q2.1 (E), Q3.1 (E), Q4.1 (E), Q6.1 (E), Q7.1 (E), Q8.1 (E), Q9.1 (E), Q10.1 (E), R7.2, R14.2, R16.2
unnamed: D1.2 (A), Q5.1 (E)
unnamed: D1.1 (K), R7.1
unnamed: J2.1, R1.2
unnamed: J2.2, R3.2
unnamed: J2.3, R4.2
unnamed: J2.4, R5.2
unnamed: J2.5, R6.2
unnamed: J2.6, R8.2
unnamed: J2.7, R9.2
unnamed: J2.8, R10.2
unnamed: J5.1, J5.2, J5.3, Q11.1 (E), R14.1
unnamed: J6.1, J6.2, J6.3, Q12.1 (E), R16.1
unnamed: Q1.2 (B), R3.1
unnamed: Q1.3 (C), Q2.3 (C), Q3.3 (C), Q4.3 (C), Q5.2 (B), Q6.3 (C), Q7.3 (C), Q8.3 (C), Q9.3 (C), R2.1, R11.2, R12.2
unnamed: Q2.2 (B), R1.1
unnamed: Q3.2 (B), R4.1
unnamed: Q4.2 (B), R5.1
unnamed: Q6.2 (B), R6.1
unnamed: Q7.2 (B), R8.1
unnamed: Q8.2 (B), R9.1
unnamed: Q9.2 (B), R10.1
unnamed: Q10.2 (B), R11.1
unnamed: Q10.3 (C), R13.2, R15.2
unnamed: Q11.2 (B), R12.1
unnamed: Q12.2 (B), R15.1
VCC: C1.1, J1.1, J3.1, J4.1, Q5.3 (C), Q11.3 (C), Q12.3 (C), R2.2, R13.1

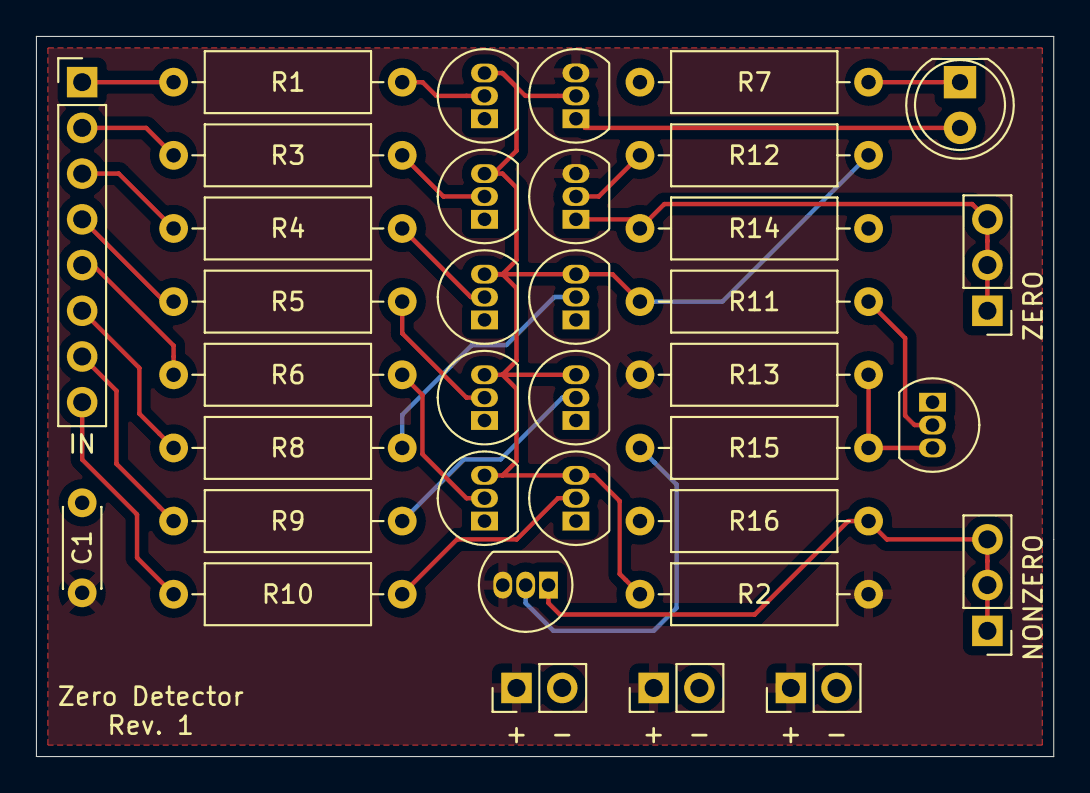
[picture p44: board Zero Detector.kicad_pcb from above]

Board: 2 copper layers, 56.5 x 40.0 mm, 36 parts (0 on the bottom side), 27 nets.
