DragonMinded/minidragon/schematics/PCBs/4-Bit Register/Transistor 4-Bit Register.kicad_pcb

## KiCad design schematics/PCBs/4-Bit Register/Transistor 4-Bit Register.kicad_pcb (2024-01-27)

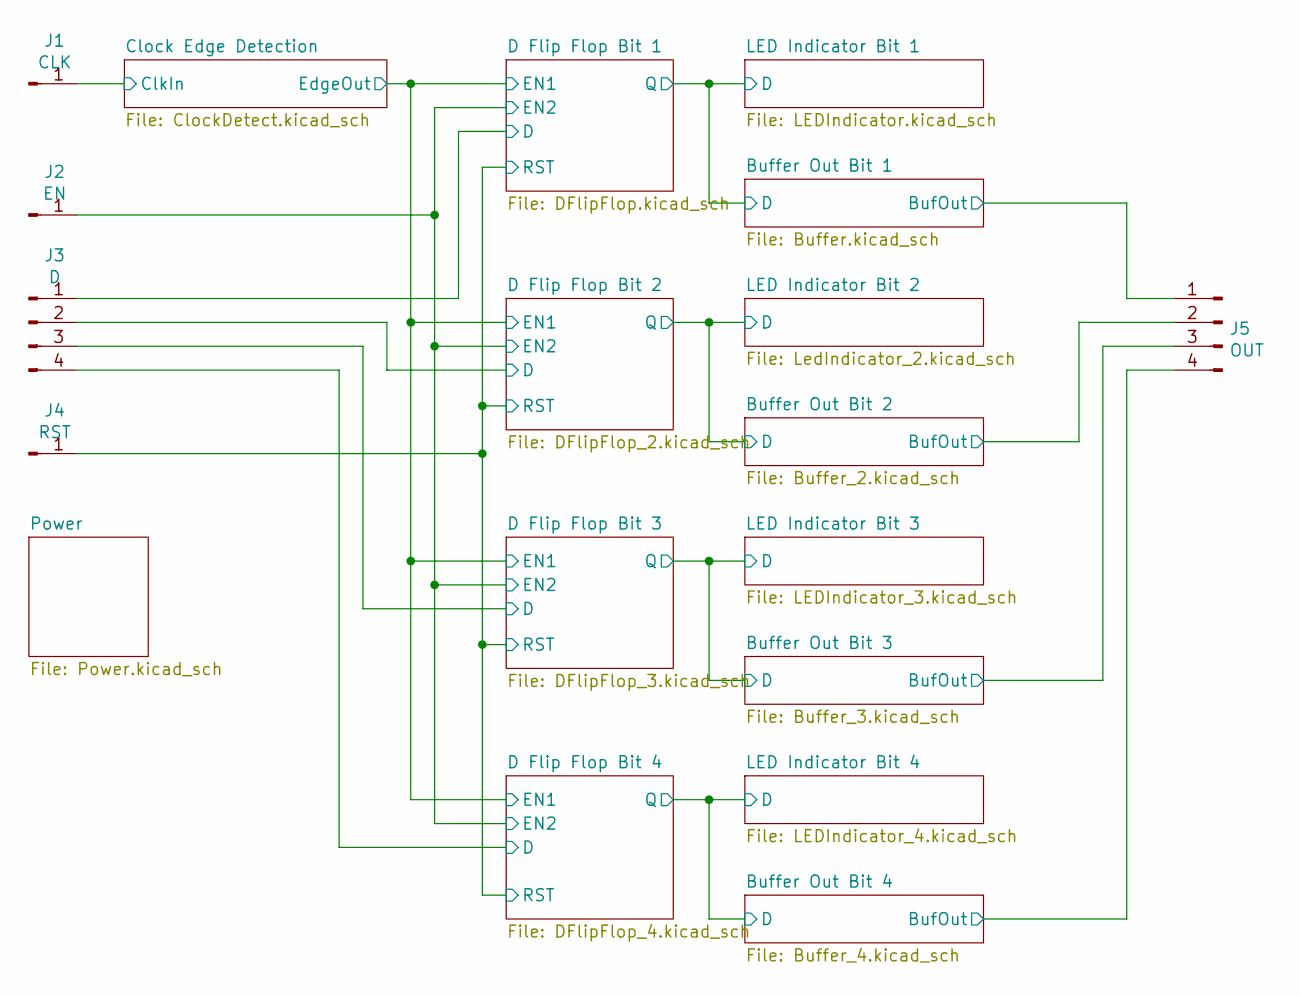
[picture p45: schematic Transistor 4-Bit Register.kicad_sch]

Parts:
J1: CLK; PinHeader_1x01_P2.54mm_Vertical
J2: EN; PinHeader_1x01_P2.54mm_Vertical
J3: D; PinHeader_1x04_P2.54mm_Vertical
J4: RST; PinHeader_1x01_P2.54mm_Vertical
J5: OUT; PinHeader_1x04_P2.54mm_Vertical

Connections:
/Buffer Out Bit 1/BufOut: J5.1; also elsewhere on the board
/Buffer Out Bit 2/BufOut: J5.2; also elsewhere on the board
/Buffer Out Bit 3/BufOut: J5.3; also elsewhere on the board
/Buffer Out Bit 4/BufOut: J5.4; also elsewhere on the board
/Clock Edge Detection/ClkIn: J1.1; also elsewhere on the board
/D Flip Flop Bit 1/D: J3.1; also elsewhere on the board
/D Flip Flop Bit 1/EN2: J2.1; also elsewhere on the board
/D Flip Flop Bit 1/RST: J4.1; also elsewhere on the board
/D Flip Flop Bit 2/D: J3.2; also elsewhere on the board
/D Flip Flop Bit 3/D: J3.3; also elsewhere on the board
/D Flip Flop Bit 4/D: J3.4; also elsewhere on the board

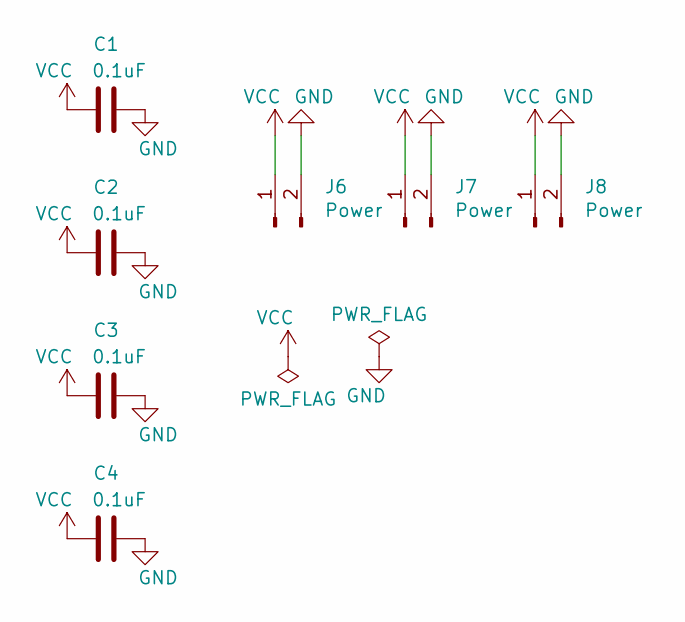
[picture p46: schematic Power.kicad_sch]

Parts:
C1, C2, C3, C4: 0.1uF; C_Disc_D4.3mm_W1.9mm_P5.00mm
J6, J7, J8: Power; PinHeader_1x02_P2.54mm_Vertical

Connections:
GND: C1.1, C2.1, C3.1, C4.1, J6.2, J7.2, J8.2; also elsewhere on the board
VCC: C1.2, C2.2, C3.2, C4.2, J6.1, J7.1, J8.1; also elsewhere on the board

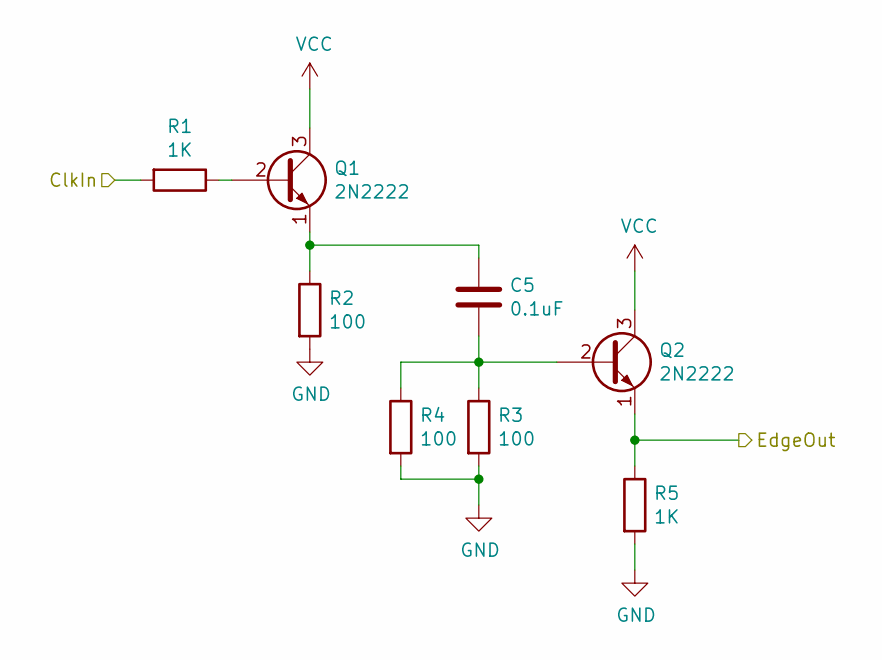
[picture p47: schematic ClockDetect.kicad_sch]

Parts:
C5: 0.1uF; C_Disc_D4.3mm_W1.9mm_P5.00mm
Q1, Q2: 2N2222; TO-92_Inline
R1, R5: 1K; R_Axial_DIN0309_L9.0mm_D3.2mm_P12.70mm_Horizontal
R2, R3, R4: 100; R_Axial_DIN0309_L9.0mm_D3.2mm_P12.70mm_Horizontal

Connections:
/Clock Edge Detection/ClkIn: R1.2; also elsewhere on the board
/Clock Edge Detection/EdgeOut: Q2.1 (E), R5.1; also elsewhere on the board
GND: R2.2, R3.2, R4.2, R5.2; also elsewhere on the board
unnamed: Q1.2 (B), R1.1
unnamed: C5.1, Q1.1 (E), R2.1
unnamed: C5.2, Q2.2 (B), R3.1, R4.1
VCC: Q1.3 (C), Q2.3 (C); also elsewhere on the board

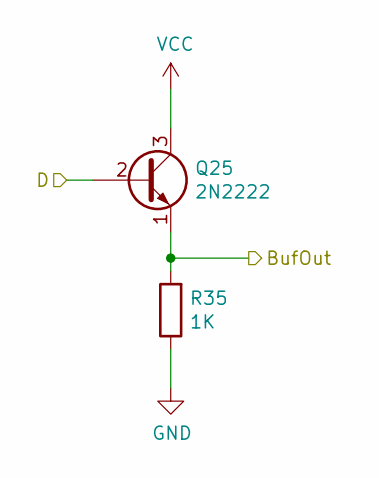
[picture p48: schematic Buffer.kicad_sch]

Parts:
Q25: 2N2222; TO-92_Inline
R35: 1K; R_Axial_DIN0309_L9.0mm_D3.2mm_P12.70mm_Horizontal

Connections:
/Buffer Out Bit 1/BufOut: Q25.1 (E), R35.2; also elsewhere on the board
/Buffer Out Bit 1/D: Q25.2 (B); also elsewhere on the board
GND: R35.1; also elsewhere on the board
VCC: Q25.3 (C); also elsewhere on the board

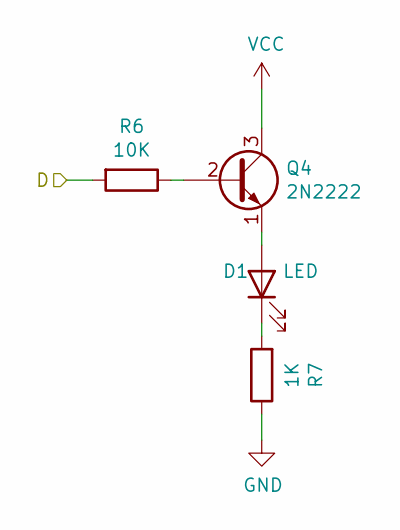
[picture p49: schematic LEDIndicator.kicad_sch]

Parts:
D1: LED; LED_D5.0mm
Q4: 2N2222; TO-92_Inline
R6: 10K; R_Axial_DIN0309_L9.0mm_D3.2mm_P12.70mm_Horizontal
R7: 1K; R_Axial_DIN0309_L9.0mm_D3.2mm_P12.70mm_Horizontal

Connections:
/Buffer Out Bit 1/D: R6.2; also elsewhere on the board
GND: R7.1; also elsewhere on the board
unnamed: D1.2 (A), Q4.1 (E)
unnamed: D1.1 (K), R7.2
unnamed: Q4.2 (B), R6.1
VCC: Q4.3 (C); also elsewhere on the board

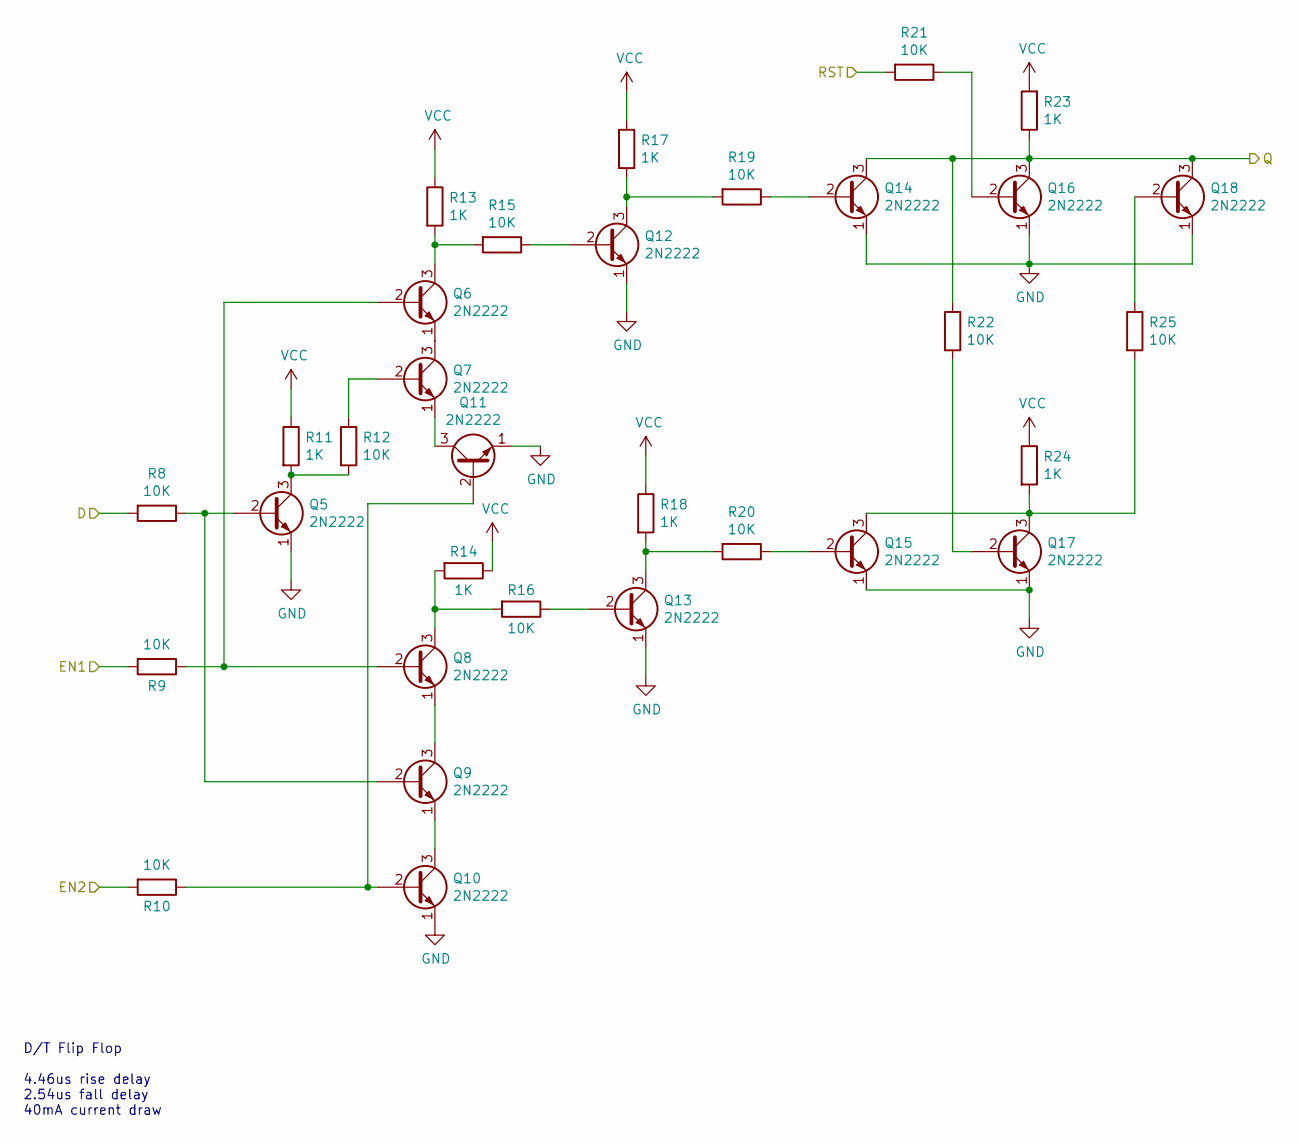
[picture p50: schematic DFlipFlop.kicad_sch, D Flip Flop]

Parts:
Q5, Q6, Q7, Q8, Q9, Q10, Q11, Q12, Q13, Q14, Q15, Q16, Q17, Q18: 2N2222; TO-92_Inline
R8, R9, R10, R12, R15, R16, R19, R20, R21, R22, R25: 10K; R_Axial_DIN0309_L9.0mm_D3.2mm_P12.70mm_Horizontal
R11, R13, R14, R17, R18, R23, R24: 1K; R_Axial_DIN0309_L9.0mm_D3.2mm_P12.70mm_Horizontal

Connections:
/Buffer Out Bit 1/D: Q14.3 (C), Q16.3 (C), Q18.3 (C), R22.1, R23.1; also elsewhere on the board
/Clock Edge Detection/EdgeOut: R9.2; also elsewhere on the board
/D Flip Flop Bit 1/D: R8.2; also elsewhere on the board
/D Flip Flop Bit 1/EN2: R10.2; also elsewhere on the board
/D Flip Flop Bit 1/RST: R21.2; also elsewhere on the board
GND: Q5.1 (E), Q10.1 (E), Q11.1 (E), Q12.1 (E), Q13.1 (E), Q14.1 (E), Q15.1 (E), Q16.1 (E), Q17.1 (E), Q18.1 (E); also elsewhere on the board
unnamed: Q5.2 (B), Q9.2 (B), R8.1
unnamed: Q5.3 (C), R11.2, R12.2
unnamed: Q6.2 (B), Q8.2 (B), R9.1
unnamed: Q6.3 (C), R13.2, R15.2
unnamed: Q6.1 (E), Q7.3 (C)
unnamed: Q7.2 (B), R12.1
unnamed: Q8.3 (C), R14.2, R16.2
unnamed: Q8.1 (E), Q9.3 (C)
unnamed: Q10.2 (B), Q11.2 (B), R10.1
unnamed: Q9.1 (E), Q10.3 (C)
unnamed: Q7.1 (E), Q11.3 (C)
unnamed: Q12.2 (B), R15.1
unnamed: Q12.3 (C), R17.2, R19.2
unnamed: Q13.2 (B), R16.1
unnamed: Q13.3 (C), R18.2, R20.2
unnamed: Q14.2 (B), R19.1
unnamed: Q15.2 (B), R20.1
unnamed: Q15.3 (C), Q17.3 (C), R24.2, R25.2
unnamed: Q16.2 (B), R21.1
unnamed: Q17.2 (B), R22.2
unnamed: Q18.2 (B), R25.1
VCC: R11.1, R13.1, R14.1, R17.1, R18.1, R23.2, R24.1; also elsewhere on the board

Notes on the sheet:
D/T Flip Flop 4.46us rise delay 2.54us fall delay 40mA current draw

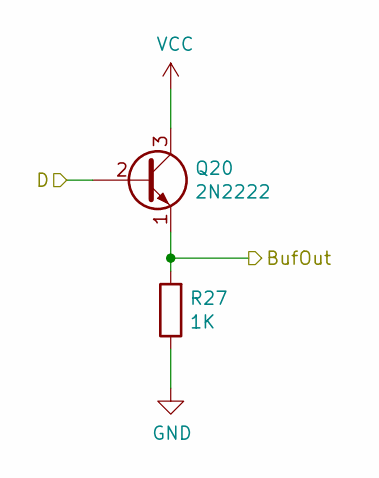
[picture p51: schematic Buffer_2.kicad_sch]

Parts:
Q20: 2N2222; TO-92_Inline
R27: 1K; R_Axial_DIN0309_L9.0mm_D3.2mm_P12.70mm_Horizontal

Connections:
/Buffer Out Bit 2/BufOut: Q20.1 (E), R27.2; also elsewhere on the board
/Buffer Out Bit 2/D: Q20.2 (B); also elsewhere on the board
GND: R27.1; also elsewhere on the board
VCC: Q20.3 (C); also elsewhere on the board

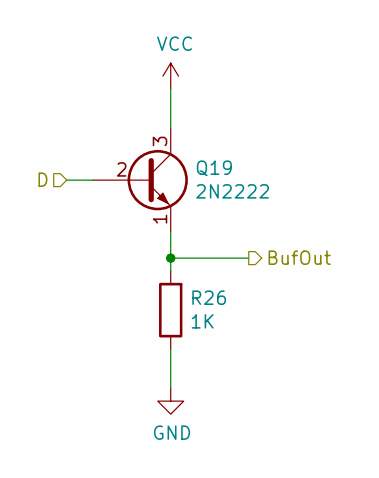
[picture p52: schematic Buffer_4.kicad_sch]

Parts:
Q19: 2N2222; TO-92_Inline
R26: 1K; R_Axial_DIN0309_L9.0mm_D3.2mm_P12.70mm_Horizontal

Connections:
/Buffer Out Bit 4/BufOut: Q19.1 (E), R26.2; also elsewhere on the board
/Buffer Out Bit 4/D: Q19.2 (B); also elsewhere on the board
GND: R26.1; also elsewhere on the board
VCC: Q19.3 (C); also elsewhere on the board

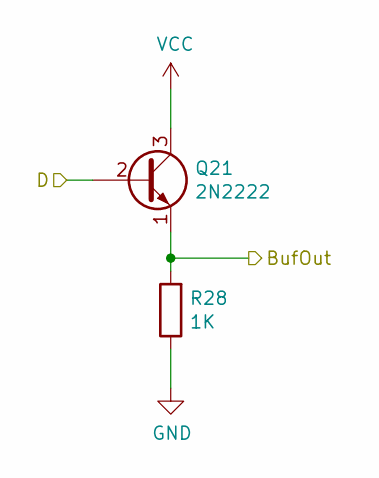
[picture p53: schematic Buffer_3.kicad_sch]

Parts:
Q21: 2N2222; TO-92_Inline
R28: 1K; R_Axial_DIN0309_L9.0mm_D3.2mm_P12.70mm_Horizontal

Connections:
/Buffer Out Bit 3/BufOut: Q21.1 (E), R28.2; also elsewhere on the board
/Buffer Out Bit 3/D: Q21.2 (B); also elsewhere on the board
GND: R28.1; also elsewhere on the board
VCC: Q21.3 (C); also elsewhere on the board

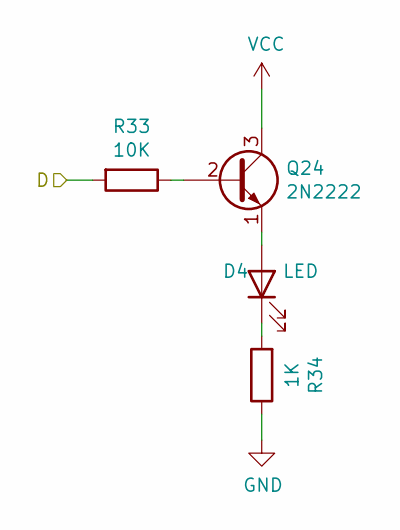
[picture p54: schematic LedIndicator_2.kicad_sch]

Parts:
D4: LED; LED_D5.0mm
Q24: 2N2222; TO-92_Inline
R33: 10K; R_Axial_DIN0309_L9.0mm_D3.2mm_P12.70mm_Horizontal
R34: 1K; R_Axial_DIN0309_L9.0mm_D3.2mm_P12.70mm_Horizontal

Connections:
/Buffer Out Bit 2/D: R33.2; also elsewhere on the board
GND: R34.1; also elsewhere on the board
unnamed: D4.2 (A), Q24.1 (E)
unnamed: D4.1 (K), R34.2
unnamed: Q24.2 (B), R33.1
VCC: Q24.3 (C); also elsewhere on the board

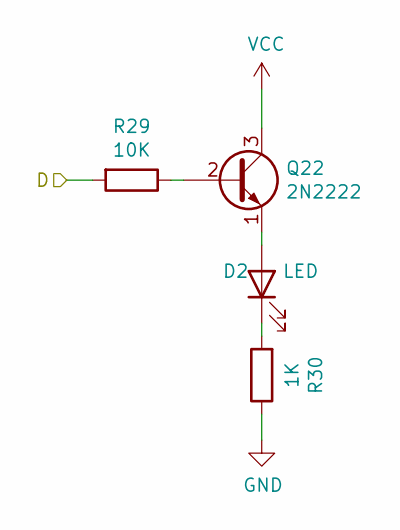
[picture p55: schematic LEDIndicator_3.kicad_sch]

Parts:
D2: LED; LED_D5.0mm
Q22: 2N2222; TO-92_Inline
R29: 10K; R_Axial_DIN0309_L9.0mm_D3.2mm_P12.70mm_Horizontal
R30: 1K; R_Axial_DIN0309_L9.0mm_D3.2mm_P12.70mm_Horizontal

Connections:
/Buffer Out Bit 3/D: R29.2; also elsewhere on the board
GND: R30.1; also elsewhere on the board
unnamed: D2.2 (A), Q22.1 (E)
unnamed: D2.1 (K), R30.2
unnamed: Q22.2 (B), R29.1
VCC: Q22.3 (C); also elsewhere on the board

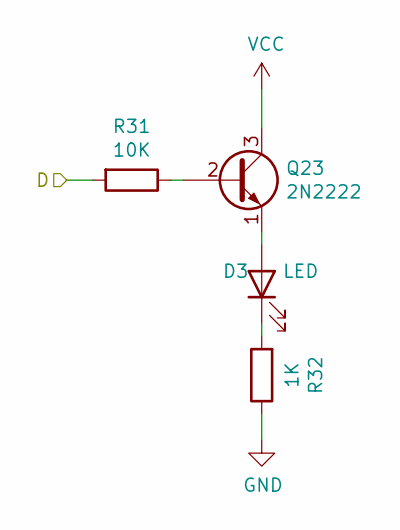
[picture p56: schematic LEDIndicator_4.kicad_sch]

Parts:
D3: LED; LED_D5.0mm
Q23: 2N2222; TO-92_Inline
R31: 10K; R_Axial_DIN0309_L9.0mm_D3.2mm_P12.70mm_Horizontal
R32: 1K; R_Axial_DIN0309_L9.0mm_D3.2mm_P12.70mm_Horizontal

Connections:
/Buffer Out Bit 4/D: R31.2; also elsewhere on the board
GND: R32.1; also elsewhere on the board
unnamed: D3.2 (A), Q23.1 (E)
unnamed: D3.1 (K), R32.2
unnamed: Q23.2 (B), R31.1
VCC: Q23.3 (C); also elsewhere on the board

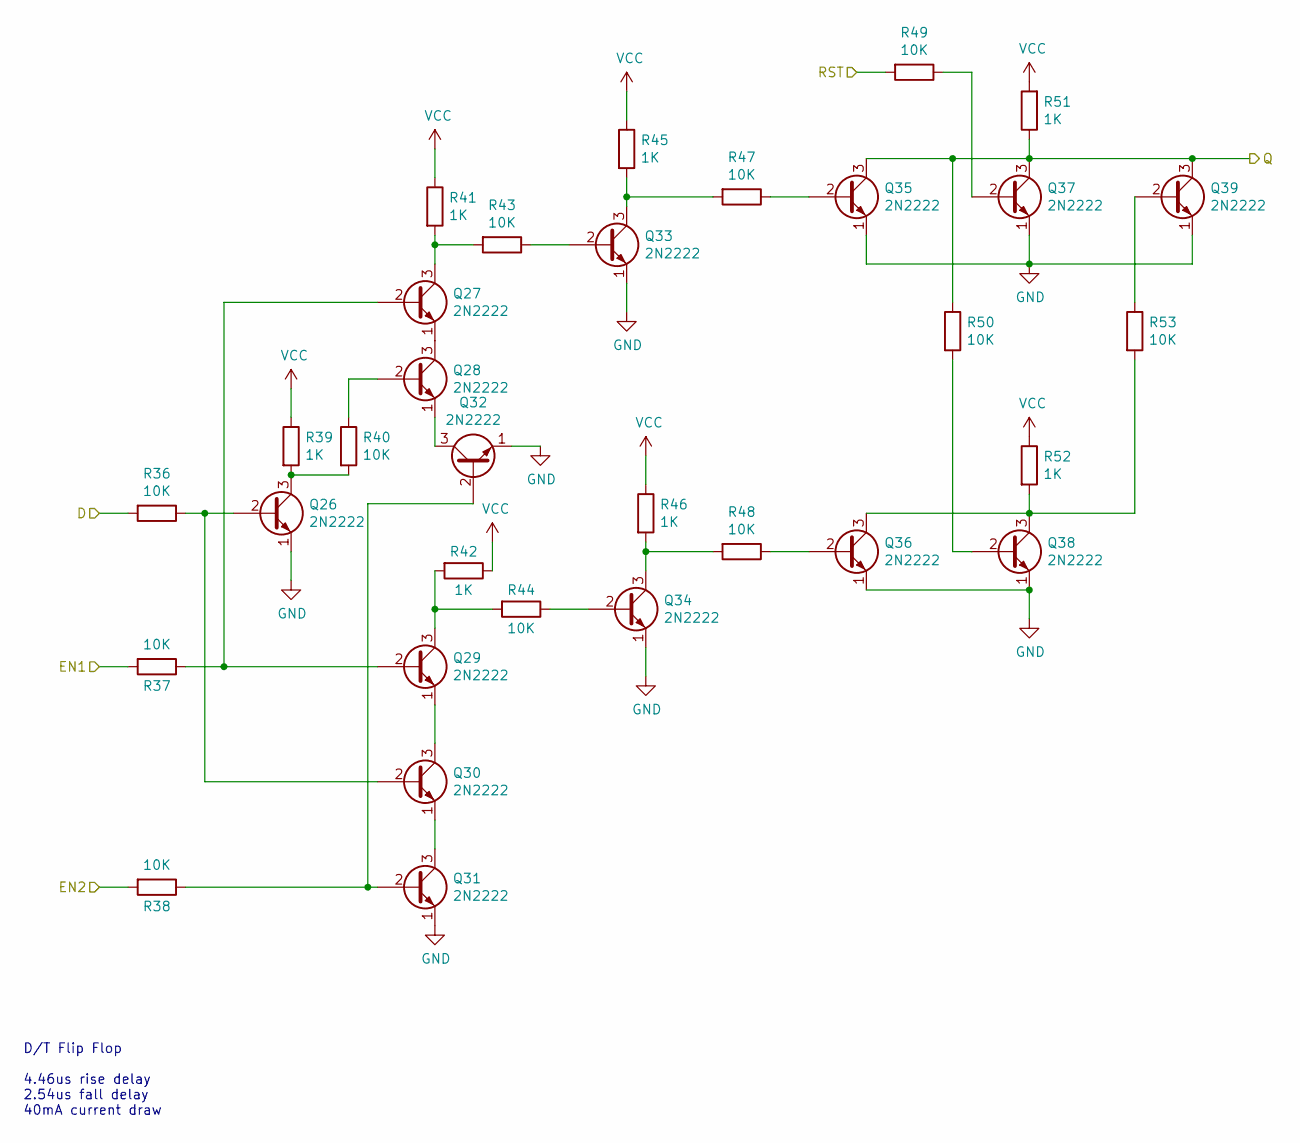
[picture p57: schematic DFlipFlop_2.kicad_sch, D Flip Flop]

Parts:
Q26, Q27, Q28, Q29, Q30, Q31, Q32, Q33, Q34, Q35, Q36, Q37, Q38, Q39: 2N2222; TO-92_Inline
R36, R37, R38, R40, R43, R44, R47, R48, R49, R50, R53: 10K; R_Axial_DIN0309_L9.0mm_D3.2mm_P12.70mm_Horizontal
R39, R41, R42, R45, R46, R51, R52: 1K; R_Axial_DIN0309_L9.0mm_D3.2mm_P12.70mm_Horizontal

Connections:
/Buffer Out Bit 2/D: Q35.3 (C), Q37.3 (C), Q39.3 (C), R50.1, R51.1; also elsewhere on the board
/Clock Edge Detection/EdgeOut: R37.2; also elsewhere on the board
/D Flip Flop Bit 1/EN2: R38.2; also elsewhere on the board
/D Flip Flop Bit 1/RST: R49.2; also elsewhere on the board
/D Flip Flop Bit 2/D: R36.2; also elsewhere on the board
GND: Q26.1 (E), Q31.1 (E), Q32.1 (E), Q33.1 (E), Q34.1 (E), Q35.1 (E), Q36.1 (E), Q37.1 (E), Q38.1 (E), Q39.1 (E); also elsewhere on the board
unnamed: Q26.2 (B), Q30.2 (B), R36.1
unnamed: Q26.3 (C), R39.2, R40.2
unnamed: Q27.2 (B), Q29.2 (B), R37.1
unnamed: Q27.3 (C), R41.2, R43.2
unnamed: Q27.1 (E), Q28.3 (C)
unnamed: Q28.2 (B), R40.1
unnamed: Q28.1 (E), Q32.3 (C)
unnamed: Q29.3 (C), R42.2, R44.2
unnamed: Q29.1 (E), Q30.3 (C)
unnamed: Q30.1 (E), Q31.3 (C)
unnamed: Q31.2 (B), Q32.2 (B), R38.1
unnamed: Q33.2 (B), R43.1
unnamed: Q33.3 (C), R45.2, R47.2
unnamed: Q34.2 (B), R44.1
unnamed: Q34.3 (C), R46.2, R48.2
unnamed: Q35.2 (B), R47.1
unnamed: Q36.2 (B), R48.1
unnamed: Q36.3 (C), Q38.3 (C), R52.2, R53.2
unnamed: Q37.2 (B), R49.1
unnamed: Q38.2 (B), R50.2
unnamed: Q39.2 (B), R53.1
VCC: R39.1, R41.1, R42.1, R45.1, R46.1, R51.2, R52.1; also elsewhere on the board

Notes on the sheet:
D/T Flip Flop 4.46us rise delay 2.54us fall delay 40mA current draw

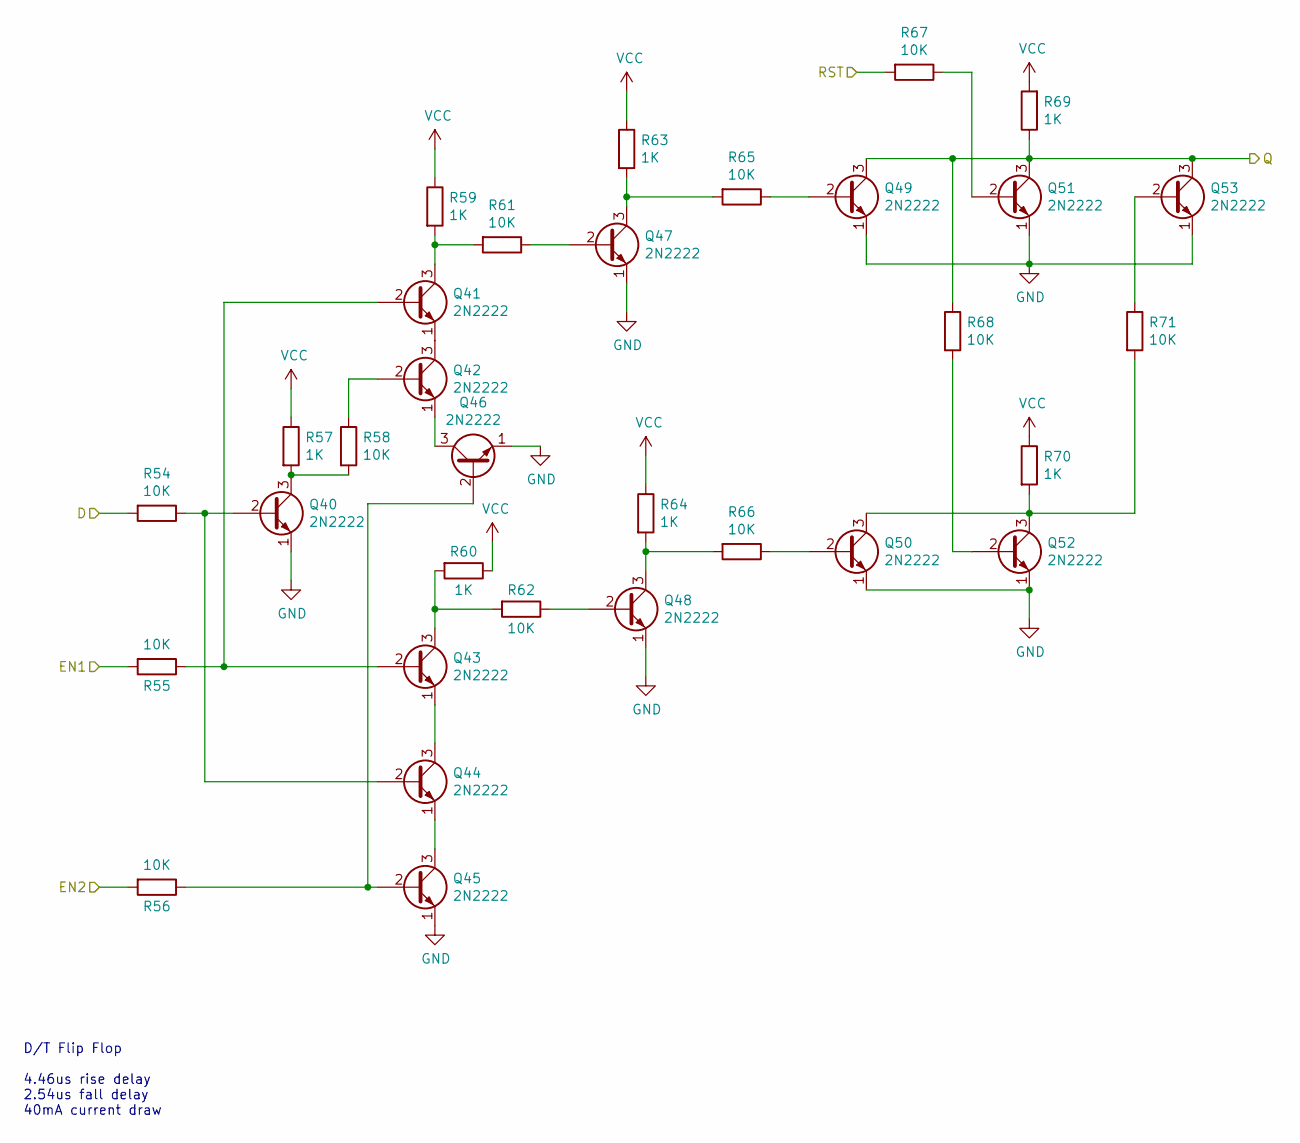
[picture p58: schematic DFlipFlop_3.kicad_sch, D Flip Flop]

Parts:
Q40, Q41, Q42, Q43, Q44, Q45, Q46, Q47, Q48, Q49, Q50, Q51, Q52, Q53: 2N2222; TO-92_Inline
R54, R55, R56, R58, R61, R62, R65, R66, R67, R68, R71: 10K; R_Axial_DIN0309_L9.0mm_D3.2mm_P12.70mm_Horizontal
R57, R59, R60, R63, R64, R69, R70: 1K; R_Axial_DIN0309_L9.0mm_D3.2mm_P12.70mm_Horizontal

Connections:
/Buffer Out Bit 3/D: Q49.3 (C), Q51.3 (C), Q53.3 (C), R68.1, R69.1; also elsewhere on the board
/Clock Edge Detection/EdgeOut: R55.2; also elsewhere on the board
/D Flip Flop Bit 1/EN2: R56.2; also elsewhere on the board
/D Flip Flop Bit 1/RST: R67.2; also elsewhere on the board
/D Flip Flop Bit 3/D: R54.2; also elsewhere on the board
GND: Q40.1 (E), Q45.1 (E), Q46.1 (E), Q47.1 (E), Q48.1 (E), Q49.1 (E), Q50.1 (E), Q51.1 (E), Q52.1 (E), Q53.1 (E); also elsewhere on the board
unnamed: Q40.2 (B), Q44.2 (B), R54.1
unnamed: Q40.3 (C), R57.2, R58.2
unnamed: Q41.2 (B), Q43.2 (B), R55.1
unnamed: Q41.3 (C), R59.2, R61.2
unnamed: Q41.1 (E), Q42.3 (C)
unnamed: Q42.2 (B), R58.1
unnamed: Q42.1 (E), Q46.3 (C)
unnamed: Q43.3 (C), R60.2, R62.2
unnamed: Q43.1 (E), Q44.3 (C)
unnamed: Q44.1 (E), Q45.3 (C)
unnamed: Q45.2 (B), Q46.2 (B), R56.1
unnamed: Q47.2 (B), R61.1
unnamed: Q47.3 (C), R63.2, R65.2
unnamed: Q48.2 (B), R62.1
unnamed: Q48.3 (C), R64.2, R66.2
unnamed: Q49.2 (B), R65.1
unnamed: Q50.2 (B), R66.1
unnamed: Q50.3 (C), Q52.3 (C), R70.2, R71.2
unnamed: Q51.2 (B), R67.1
unnamed: Q52.2 (B), R68.2
unnamed: Q53.2 (B), R71.1
VCC: R57.1, R59.1, R60.1, R63.1, R64.1, R69.2, R70.1; also elsewhere on the board

Notes on the sheet:
D/T Flip Flop 4.46us rise delay 2.54us fall delay 40mA current draw
