DragonMinded/minidragon/schematics/PCBs/4-Bit Register/Transistor 4-Bit Register.kicad_pcb

## KiCad design schematics/PCBs/4-Bit Register/Transistor 4-Bit Register.kicad_pcb (continued)

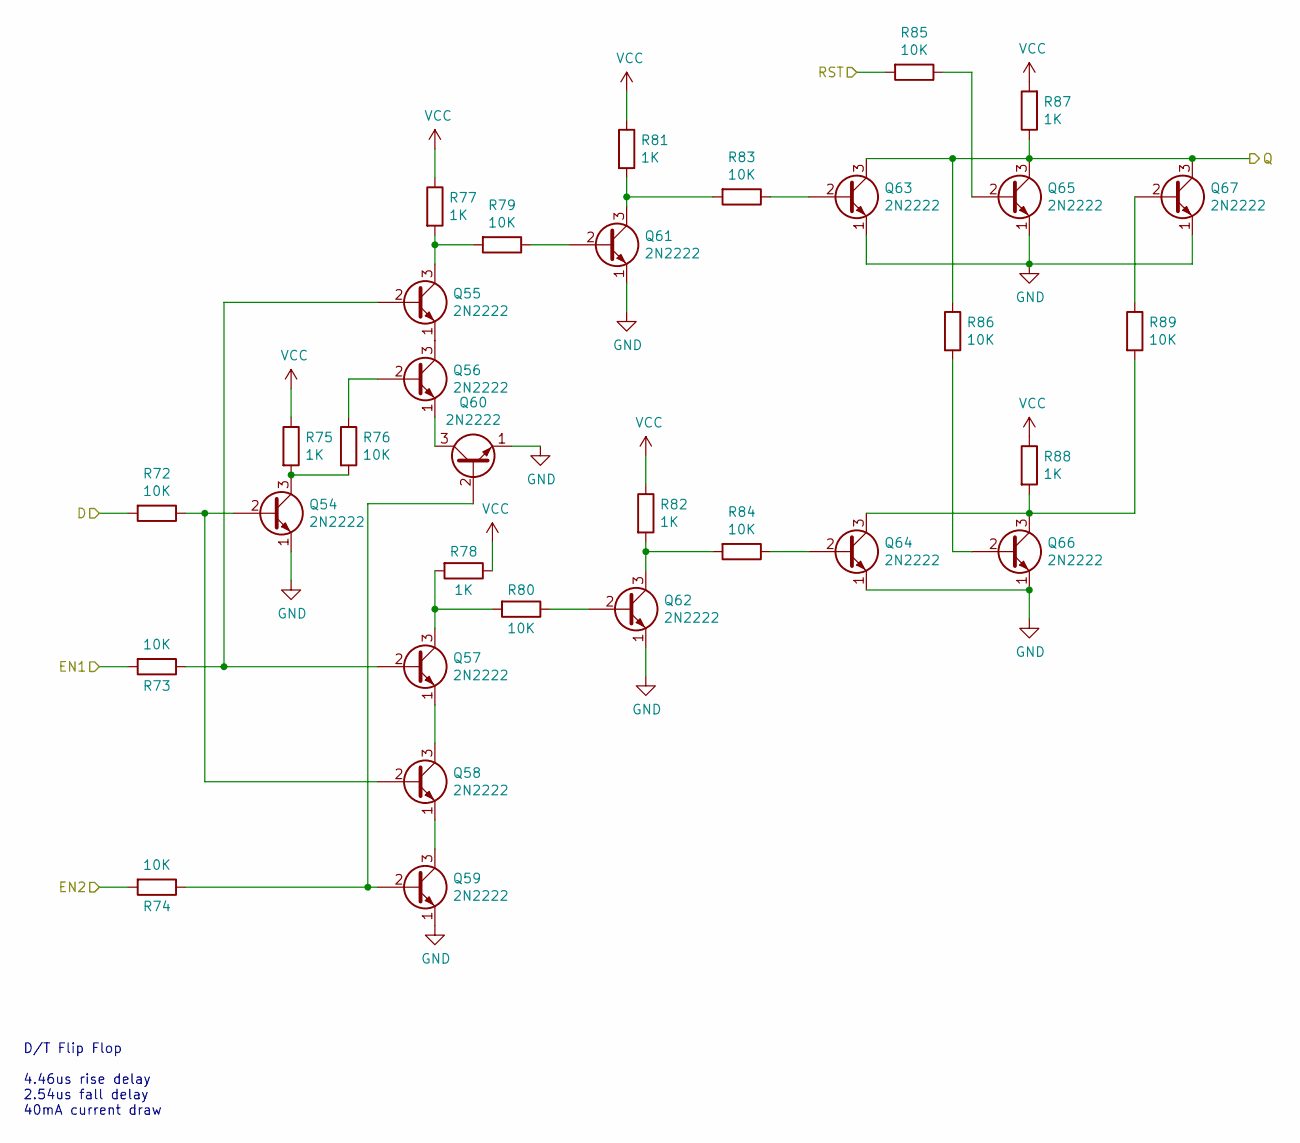
[picture p59: schematic DFlipFlop_4.kicad_sch, D Flip Flop]

Parts:
Q54, Q55, Q56, Q57, Q58, Q59, Q60, Q61, Q62, Q63, Q64, Q65, Q66, Q67: 2N2222; TO-92_Inline
R72, R73, R74, R76, R79, R80, R83, R84, R85, R86, R89: 10K; R_Axial_DIN0309_L9.0mm_D3.2mm_P12.70mm_Horizontal
R75, R77, R78, R81, R82, R87, R88: 1K; R_Axial_DIN0309_L9.0mm_D3.2mm_P12.70mm_Horizontal

Connections:
/Buffer Out Bit 4/D: Q63.3 (C), Q65.3 (C), Q67.3 (C), R86.1, R87.1; also elsewhere on the board
/Clock Edge Detection/EdgeOut: R73.2; also elsewhere on the board
/D Flip Flop Bit 1/EN2: R74.2; also elsewhere on the board
/D Flip Flop Bit 1/RST: R85.2; also elsewhere on the board
/D Flip Flop Bit 4/D: R72.2; also elsewhere on the board
GND: Q54.1 (E), Q59.1 (E), Q60.1 (E), Q61.1 (E), Q62.1 (E), Q63.1 (E), Q64.1 (E), Q65.1 (E), Q66.1 (E), Q67.1 (E); also elsewhere on the board
unnamed: Q54.2 (B), Q58.2 (B), R72.1
unnamed: Q54.3 (C), R75.2, R76.2
unnamed: Q55.2 (B), Q57.2 (B), R73.1
unnamed: Q55.3 (C), R77.2, R79.2
unnamed: Q55.1 (E), Q56.3 (C)
unnamed: Q56.2 (B), R76.1
unnamed: Q56.1 (E), Q60.3 (C)
unnamed: Q57.3 (C), R78.2, R80.2
unnamed: Q57.1 (E), Q58.3 (C)
unnamed: Q58.1 (E), Q59.3 (C)
unnamed: Q59.2 (B), Q60.2 (B), R74.1
unnamed: Q61.2 (B), R79.1
unnamed: Q61.3 (C), R81.2, R83.2
unnamed: Q62.2 (B), R80.1
unnamed: Q62.3 (C), R82.2, R84.2
unnamed: Q63.2 (B), R83.1
unnamed: Q64.2 (B), R84.1
unnamed: Q64.3 (C), Q66.3 (C), R88.2, R89.2
unnamed: Q65.2 (B), R85.1
unnamed: Q66.2 (B), R86.2
unnamed: Q67.2 (B), R89.1
VCC: R75.1, R77.1, R78.1, R81.1, R82.1, R87.2, R88.1; also elsewhere on the board

Notes on the sheet:
D/T Flip Flop 4.46us rise delay 2.54us fall delay 40mA current draw

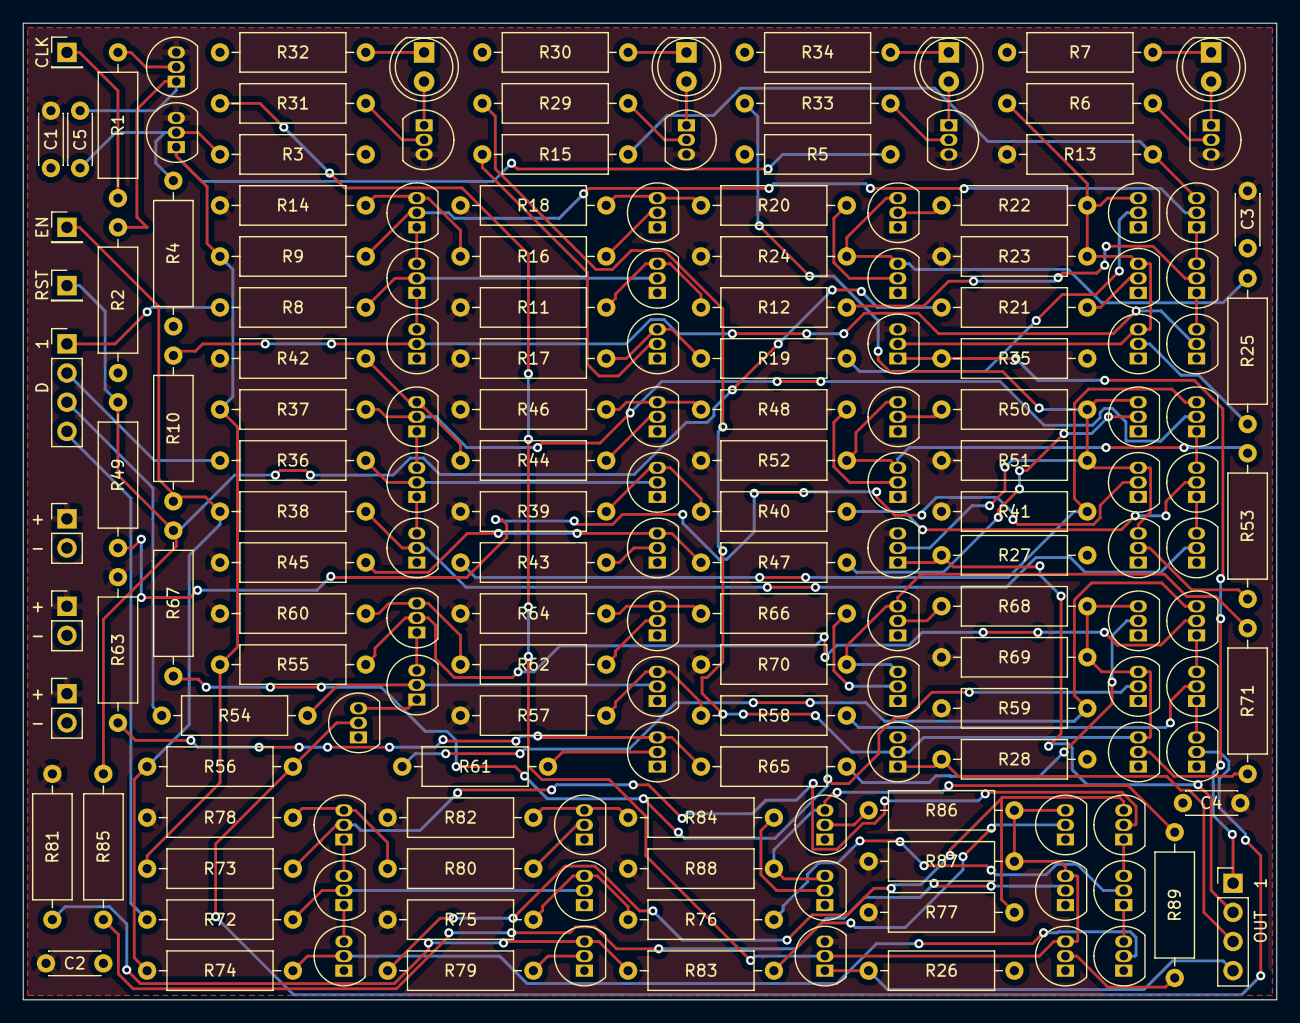
[picture p60: board Transistor 4-Bit Register.kicad_pcb from above]

Board: 2 copper layers, 109.2 x 85.1 mm, 172 parts (0 on the bottom side), 117 nets.
