DragonMinded/minidragon/schematics/PCBs/Logic XOR Gate/Transistor XOR Gate.kicad_pcb

## KiCad design schematics/PCBs/Logic XOR Gate/Transistor XOR Gate.kicad_pcb (2024-01-27)

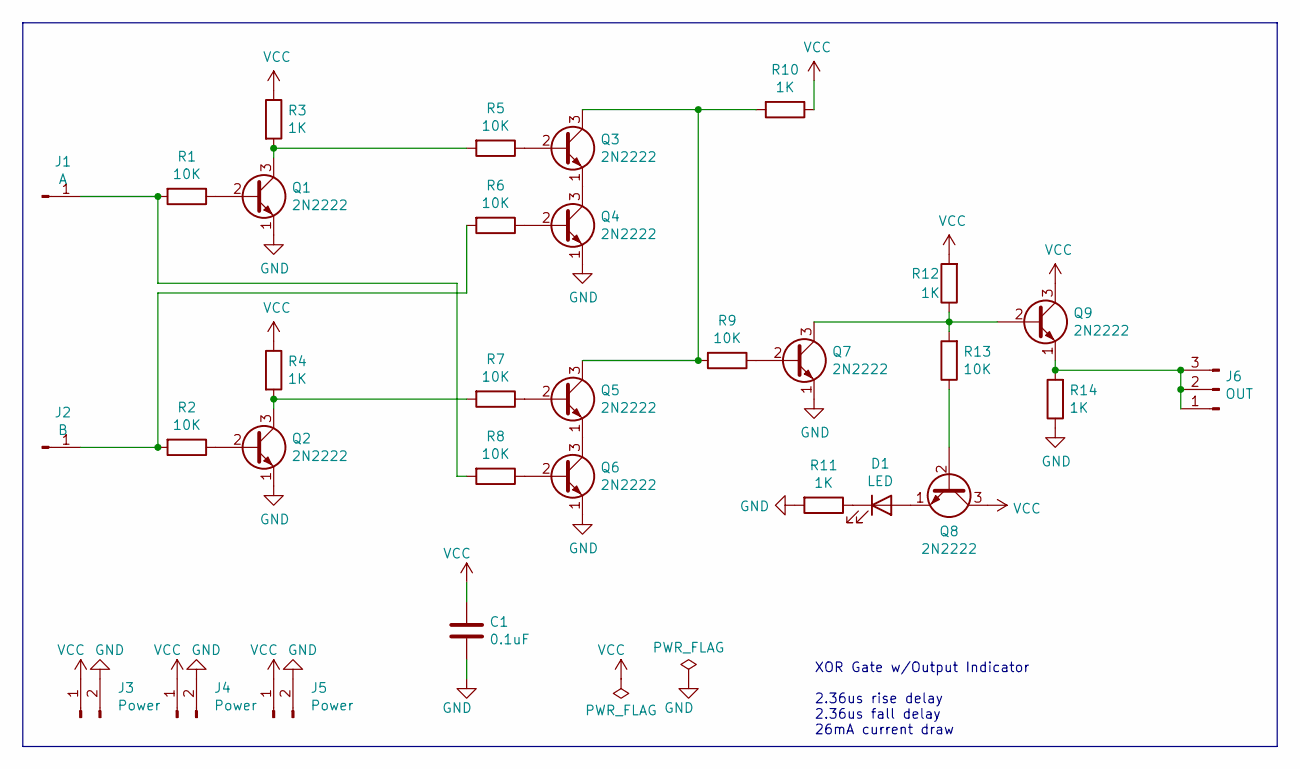
[picture p61: schematic Transistor XOR Gate.kicad_sch]

Parts:
C1: 0.1uF; C_Disc_D4.3mm_W1.9mm_P5.00mm
D1: LED; LED_D5.0mm
J1: A; PinHeader_1x01_P2.54mm_Vertical
J2: B; PinHeader_1x01_P2.54mm_Vertical
J3, J4, J5: Power; PinHeader_1x02_P2.54mm_Vertical
J6: OUT; PinHeader_1x03_P2.54mm_Vertical
Q1, Q2, Q3, Q4, Q5, Q6, Q7, Q8, Q9: 2N2222; TO-92_Inline
R1, R2, R5, R6, R7, R8, R9, R13: 10K; R_Axial_DIN0309_L9.0mm_D3.2mm_P12.70mm_Horizontal
R3, R4, R10, R11, R12, R14: 1K; R_Axial_DIN0309_L9.0mm_D3.2mm_P12.70mm_Horizontal

Connections:
GND: C1.2, J3.2, J4.2, J5.2, Q1.1 (E), Q2.1 (E), Q4.1 (E), Q6.1 (E), Q7.1 (E), R11.2, R14.1
unnamed: D1.2 (A), Q8.1 (E)
unnamed: D1.1 (K), R11.1
unnamed: J1.1, R1.2, R8.2
unnamed: J2.1, R2.2, R6.2
unnamed: J6.1, J6.2, J6.3, Q9.1 (E), R14.2
unnamed: Q1.2 (B), R1.1
unnamed: Q1.3 (C), R3.2, R5.2
unnamed: Q2.2 (B), R2.1
unnamed: Q2.3 (C), R4.2, R7.2
unnamed: Q3.2 (B), R5.1
unnamed: Q3.3 (C), Q5.3 (C), R9.2, R10.2
unnamed: Q3.1 (E), Q4.3 (C)
unnamed: Q4.2 (B), R6.1
unnamed: Q5.2 (B), R7.1
unnamed: Q5.1 (E), Q6.3 (C)
unnamed: Q6.2 (B), R8.1
unnamed: Q7.2 (B), R9.1
unnamed: Q7.3 (C), Q9.2 (B), R12.1, R13.2
unnamed: Q8.2 (B), R13.1
VCC: C1.1, J3.1, J4.1, J5.1, Q8.3 (C), Q9.3 (C), R3.1, R4.1, R10.1, R12.2

Notes on the sheet:
XOR Gate w/Output Indicator 2.36us rise delay 2.36us fall delay 26mA current draw

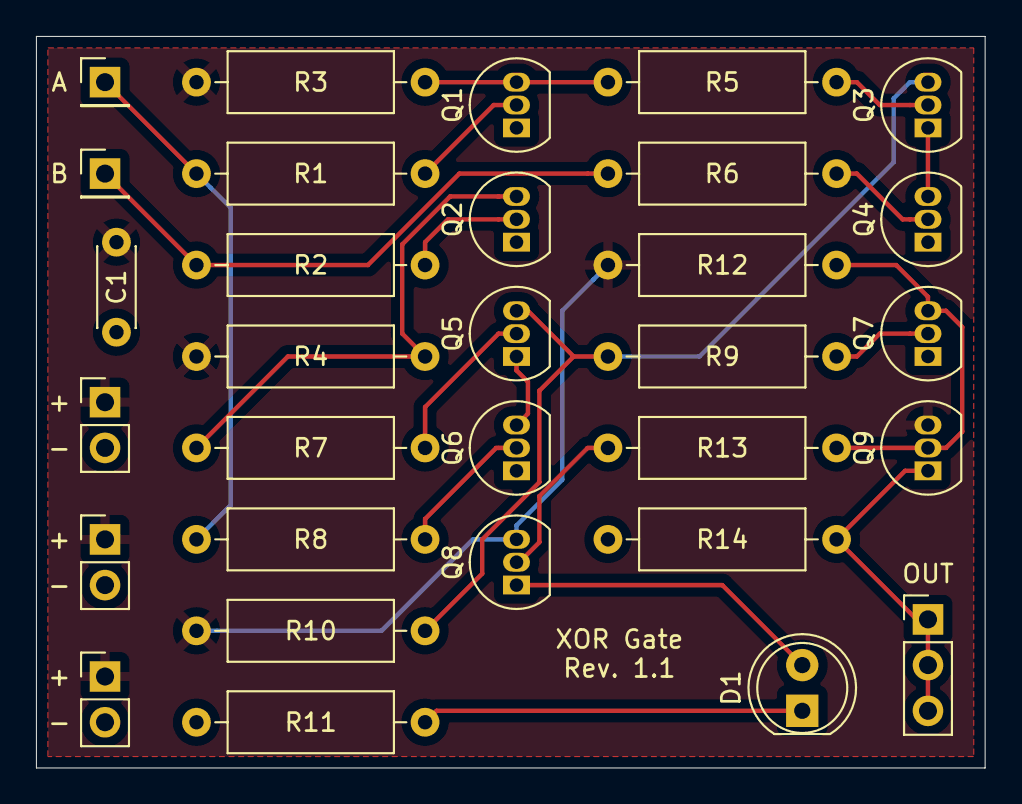
[picture p62: board Transistor XOR Gate.kicad_pcb from above]

Board: 2 copper layers, 52.7 x 40.6 mm, 31 parts (0 on the bottom side), 21 nets.
