DragonMinded/minidragon/schematics/PCBs/8-bit Bus Output Converter/Transistor 8-Bit Bus Output Circuit.kicad_pcb

## KiCad design schematics/PCBs/8-bit Bus Output Converter/Transistor 8-Bit Bus Output Circuit.kicad_pcb (2024-01-27)

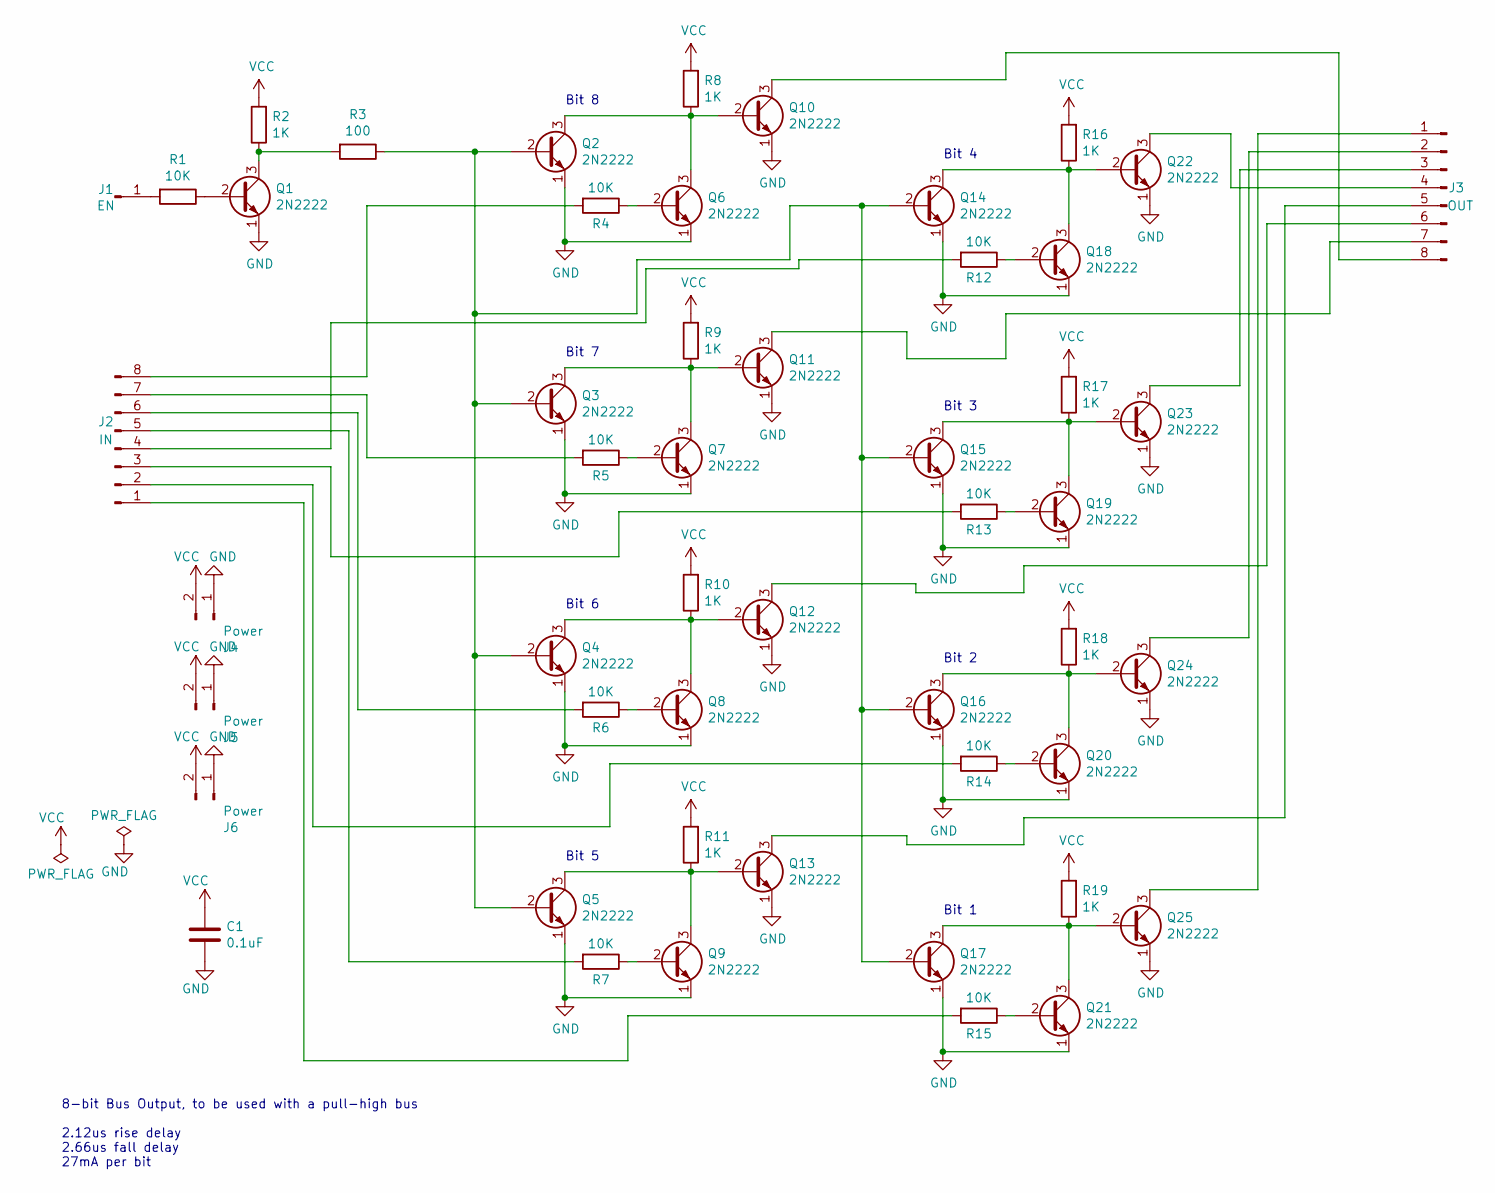
[picture p63: schematic Transistor 8-Bit Bus Output Circuit.kicad_sch, 8-bit Bus Output Circuit]

Parts:
C1: 0.1uF; C_Disc_D4.3mm_W1.9mm_P5.00mm
J1: EN; PinHeader_1x01_P2.54mm_Vertical
J2: IN; PinHeader_1x08_P2.54mm_Vertical
J3: OUT; PinHeader_1x08_P2.54mm_Vertical
J4, J5, J6: Power; PinHeader_1x02_P2.54mm_Vertical
Q1, Q2, Q3, Q4, Q5, Q6, Q7, Q8, Q9, Q10, Q11, Q12, Q13, Q14, Q15, Q16, Q17, Q18, Q19, Q20, Q21, Q22, Q23, Q24, Q25: 2N2222; TO-92_Inline
R1, R4, R5, R6, R7, R12, R13, R14, R15: 10K; R_Axial_DIN0309_L9.0mm_D3.2mm_P12.70mm_Horizontal
R2, R8, R9, R10, R11, R16, R17, R18, R19: 1K; R_Axial_DIN0309_L9.0mm_D3.2mm_P12.70mm_Horizontal
R3: 100; R_Axial_DIN0309_L9.0mm_D3.2mm_P12.70mm_Horizontal

Connections:
GND: C1.2, J4.1, J5.1, J6.1, Q1.1 (E), Q2.1 (E), Q3.1 (E), Q4.1 (E), Q5.1 (E), Q6.1 (E), Q7.1 (E), Q8.1 (E), Q9.1 (E), Q10.1 (E), Q11.1 (E), Q12.1 (E), Q13.1 (E), Q14.1 (E), Q15.1 (E), Q16.1 (E), Q17.1 (E), Q18.1 (E), Q19.1 (E), Q20.1 (E), Q21.1 (E), Q22.1 (E), Q23.1 (E), Q24.1 (E), Q25.1 (E)
unnamed: J1.1, R1.2
unnamed: J2.1, R15.2
unnamed: J2.2, R14.2
unnamed: J2.3, R13.2
unnamed: J2.4, R12.2
unnamed: J2.5, R7.2
unnamed: J2.6, R6.2
unnamed: J2.7, R5.2
unnamed: J2.8, R4.2
unnamed: J3.1, Q25.3 (C)
unnamed: J3.2, Q24.3 (C)
unnamed: J3.3, Q23.3 (C)
unnamed: J3.4, Q22.3 (C)
unnamed: J3.5, Q13.3 (C)
unnamed: J3.6, Q12.3 (C)
unnamed: J3.7, Q11.3 (C)
unnamed: J3.8, Q10.3 (C)
unnamed: Q1.2 (B), R1.1
unnamed: Q1.3 (C), R2.1, R3.2
unnamed: Q6.2 (B), R4.1
unnamed: Q7.2 (B), R5.1
unnamed: Q8.2 (B), R6.1
unnamed: Q9.2 (B), R7.1
unnamed: Q2.3 (C), Q6.3 (C), Q10.2 (B), R8.1
unnamed: Q3.3 (C), Q7.3 (C), Q11.2 (B), R9.1
unnamed: Q4.3 (C), Q8.3 (C), Q12.2 (B), R10.1
unnamed: Q5.3 (C), Q9.3 (C), Q13.2 (B), R11.1
unnamed: Q2.2 (B), Q3.2 (B), Q4.2 (B), Q5.2 (B), Q14.2 (B), Q15.2 (B), Q16.2 (B), Q17.2 (B), R3.1
unnamed: Q14.3 (C), Q18.3 (C), Q22.2 (B), R16.1
unnamed: Q15.3 (C), Q19.3 (C), Q23.2 (B), R17.1
unnamed: Q16.3 (C), Q20.3 (C), Q24.2 (B), R18.1
unnamed: Q17.3 (C), Q21.3 (C), Q25.2 (B), R19.1
unnamed: Q18.2 (B), R12.1
unnamed: Q19.2 (B), R13.1
unnamed: Q20.2 (B), R14.1
unnamed: Q21.2 (B), R15.1
VCC: C1.1, J4.2, J5.2, J6.2, R2.2, R8.2, R9.2, R10.2, R11.2, R16.2, R17.2, R18.2, R19.2

Notes on the sheet:
Bit 3
Bit 6
Bit 2
Bit 4
Bit 1
8-bit Bus Output, to be used with a pull-high bus 2.12us rise delay 2.66us fall delay 27mA per bit
Bit 7
Bit 5
Bit 8

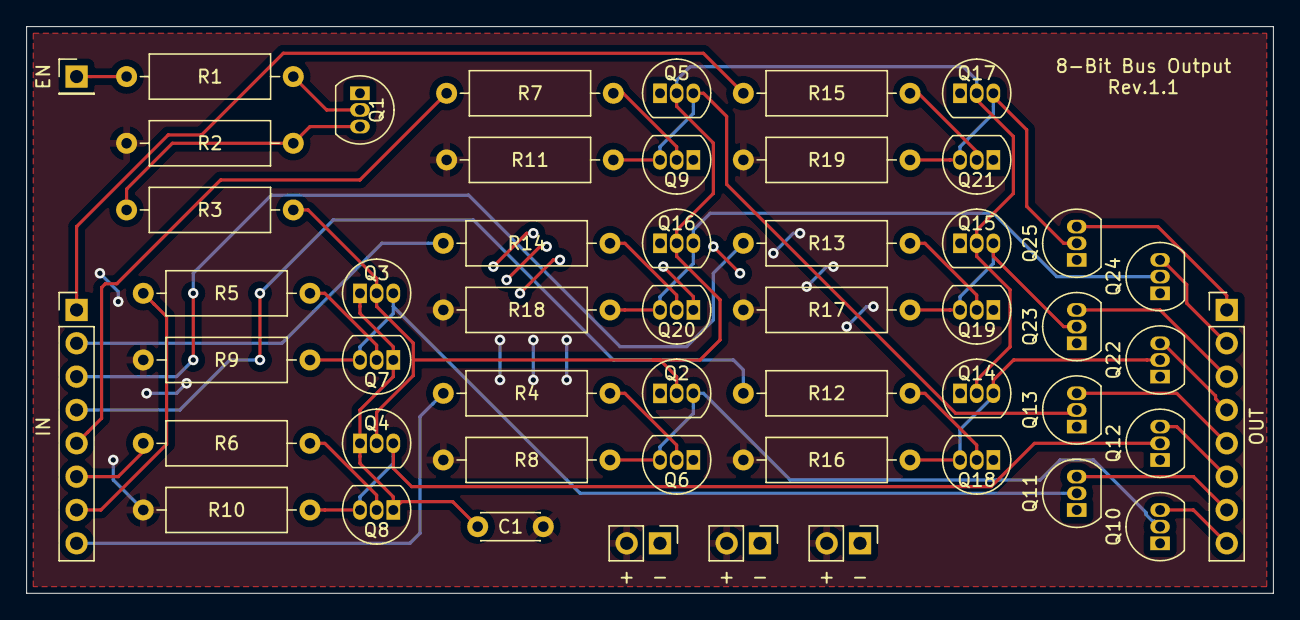
[picture p64: board Transistor 8-Bit Bus Output Circuit.kicad_pcb from above]

Board: 2 copper layers, 95.0 x 43.2 mm, 51 parts (0 on the bottom side), 38 nets.
