DragonMinded/minidragon/schematics/PCBs/1-to-2 Selector/Transistor 1-to-2 Selector.kicad_pcb

## KiCad design schematics/PCBs/1-to-2 Selector/Transistor 1-to-2 Selector.kicad_pcb (2024-01-27)

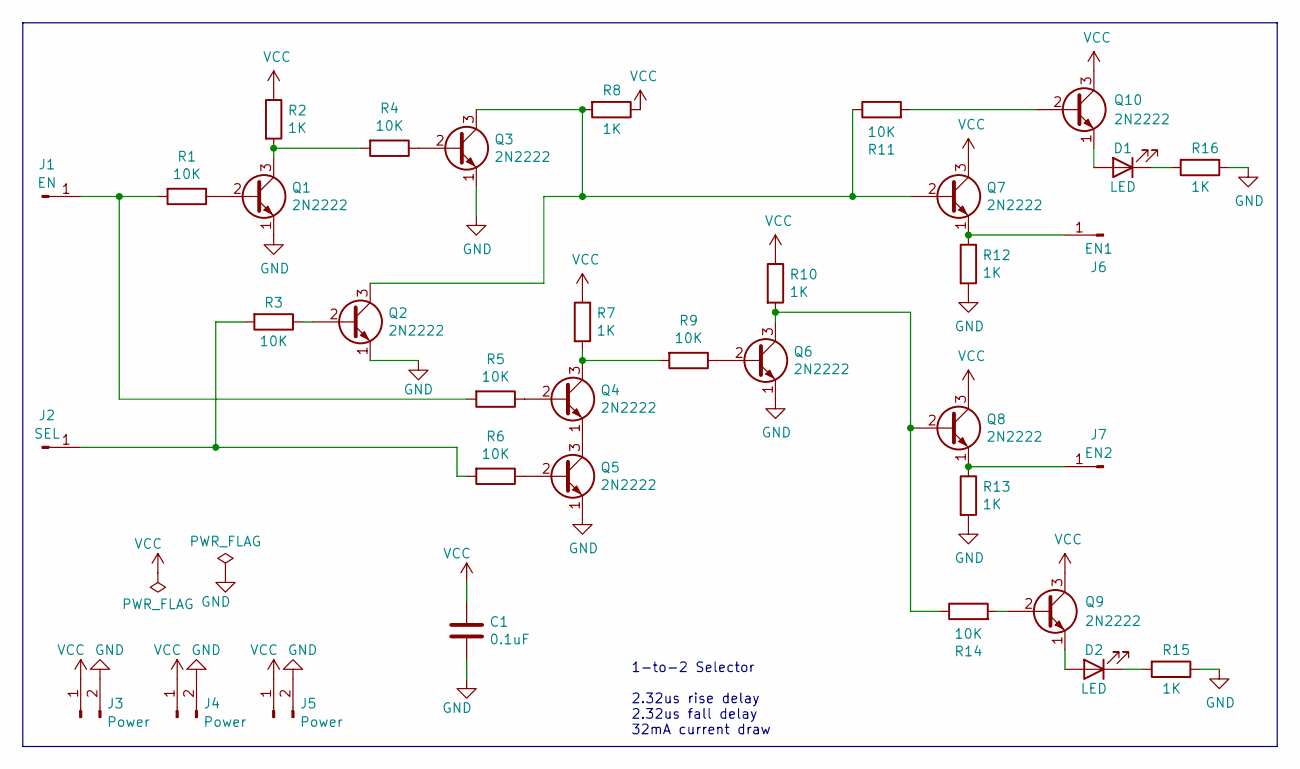
[picture p65: schematic Transistor 1-to-2 Selector.kicad_sch]

Parts:
C1: 0.1uF; C_Disc_D4.3mm_W1.9mm_P5.00mm
D1, D2: LED; LED_D5.0mm
J1: EN; PinHeader_1x01_P2.54mm_Vertical
J2: SEL; PinHeader_1x01_P2.54mm_Vertical
J3, J4, J5: Power; PinHeader_1x02_P2.54mm_Vertical
J6: EN1; PinHeader_1x01_P2.54mm_Vertical
J7: EN2; PinHeader_1x01_P2.54mm_Vertical
Q1, Q2, Q3, Q4, Q5, Q6, Q7, Q8, Q9, Q10: 2N2222; TO-92_Inline
R1, R3, R4, R5, R6, R9, R11, R14: 10K; R_Axial_DIN0309_L9.0mm_D3.2mm_P12.70mm_Horizontal
R2, R7, R8, R10, R12, R13, R15, R16: 1K; R_Axial_DIN0309_L9.0mm_D3.2mm_P12.70mm_Horizontal

Connections:
GND: C1.2, J3.2, J4.2, J5.2, Q1.1 (E), Q2.1 (E), Q3.1 (E), Q5.1 (E), Q6.1 (E), R12.2, R13.2, R15.1, R16.1
unnamed: D1.2 (A), Q10.1 (E)
unnamed: D1.1 (K), R16.2
unnamed: D2.2 (A), Q9.1 (E)
unnamed: D2.1 (K), R15.2
unnamed: J1.1, R1.2, R5.2
unnamed: J2.1, R3.2, R6.2
unnamed: J6.1, Q7.1 (E), R12.1
unnamed: J7.1, Q8.1 (E), R13.1
unnamed: Q1.2 (B), R1.1
unnamed: Q1.3 (C), R2.2, R4.2
unnamed: Q2.2 (B), R3.1
unnamed: Q2.3 (C), Q3.3 (C), Q7.2 (B), R8.2, R11.1
unnamed: Q3.2 (B), R4.1
unnamed: Q4.2 (B), R5.1
unnamed: Q4.3 (C), R7.2, R9.2
unnamed: Q4.1 (E), Q5.3 (C)
unnamed: Q5.2 (B), R6.1
unnamed: Q6.2 (B), R9.1
unnamed: Q6.3 (C), Q8.2 (B), R10.2, R14.1
unnamed: Q9.2 (B), R14.2
unnamed: Q10.2 (B), R11.2
VCC: C1.1, J3.1, J4.1, J5.1, Q7.3 (C), Q8.3 (C), Q9.3 (C), Q10.3 (C), R2.1, R7.1, R8.1, R10.1

Notes on the sheet:
1-to-2 Selector 2.32us rise delay 2.32us fall delay 32mA current draw

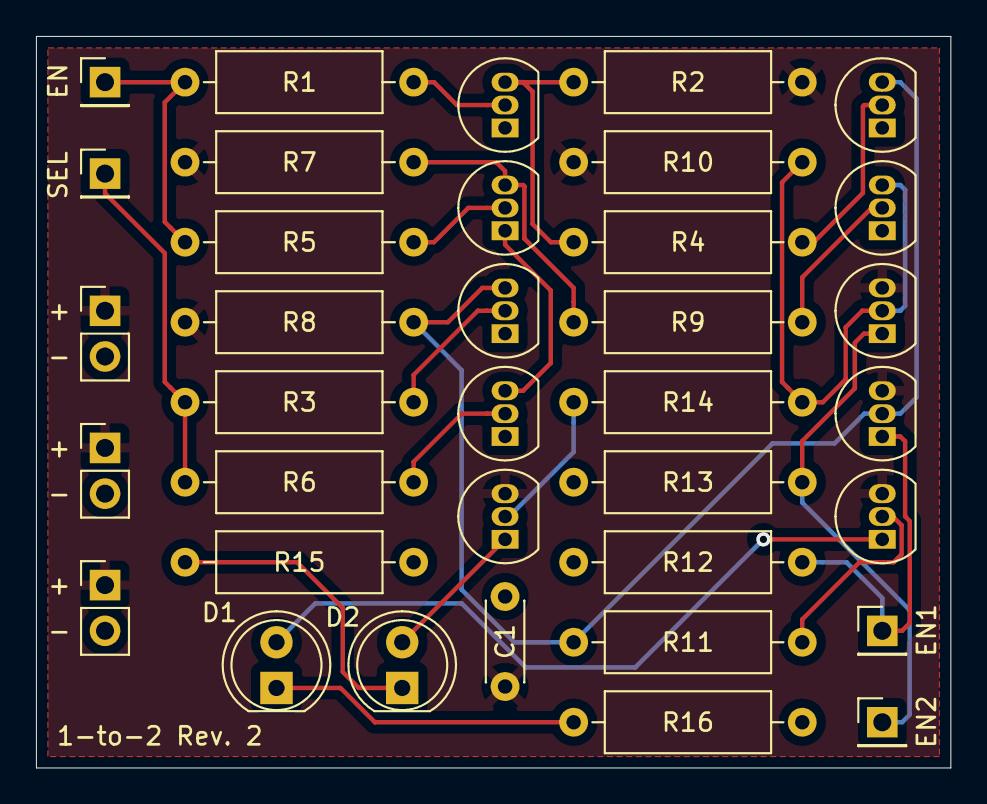
[picture p66: board Transistor 1-to-2 Selector.kicad_pcb from above]

Board: 2 copper layers, 50.8 x 40.6 mm, 36 parts (0 on the bottom side), 23 nets.
