DragonMinded/minidragon/schematics/Layout/ALU A Input Bus.kicad_sch

## KiCad design schematics/Layout/ALU A Input Bus.kicad_sch (2026-07-15)

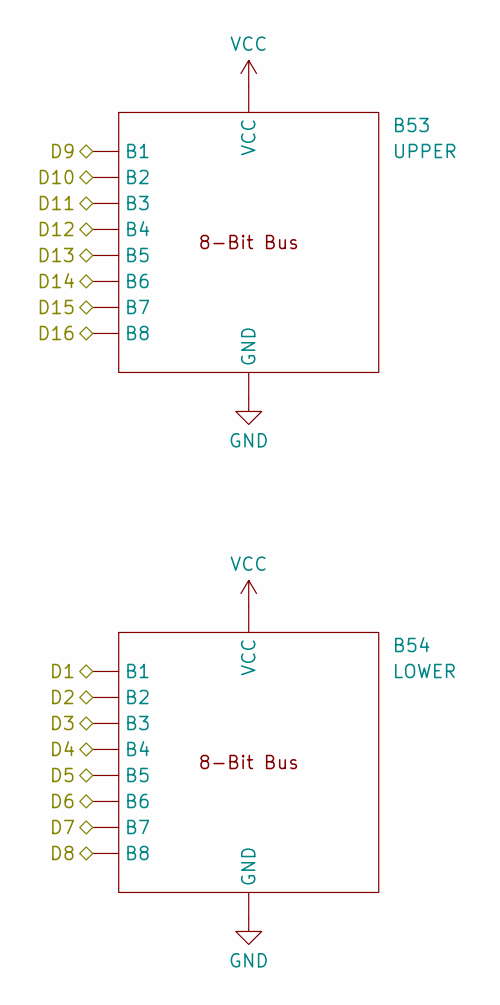
[picture p68: schematic ALU A Input Bus.kicad_sch]

Parts:
B53: UPPER
B54: LOWER

Connections:
D1: B54.
D2: B54.
D3: B54.
D4: B54.
D5: B54.
D6: B54.
D7: B54.
D8: B54.
D9: B53.
D10: B53.
D11: B53.
D12: B53.
D13: B53.
D14: B53.
D15: B53.
D16: B53.
GND: B53., B54.
VCC: B53., B54.
