DragonMinded/minidragon/schematics/Layout/Address Bus.kicad_sch

## KiCad design schematics/Layout/Address Bus.kicad_sch (2026-03-14)

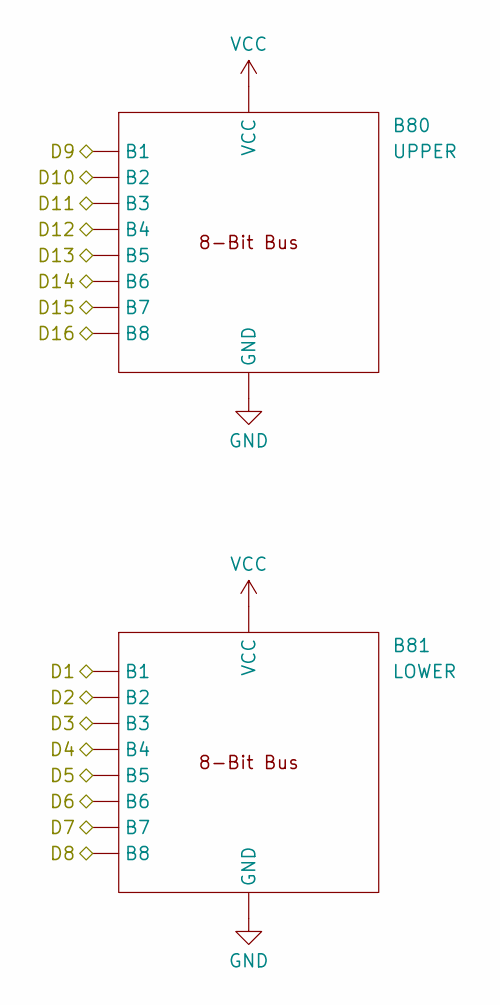
[picture p72: schematic Address Bus.kicad_sch]

Parts:
B80: UPPER
B81: LOWER

Connections:
D1: B81.
D2: B81.
D3: B81.
D4: B81.
D5: B81.
D6: B81.
D7: B81.
D8: B81.
D9: B80.
D10: B80.
D11: B80.
D12: B80.
D13: B80.
D14: B80.
D15: B80.
D16: B80.
GND: B80., B81.
VCC: B80., B81.
