DragonMinded/minidragon/schematics/Layout/D Register.kicad_sch

## KiCad design schematics/Layout/D Register.kicad_sch (2026-07-15)

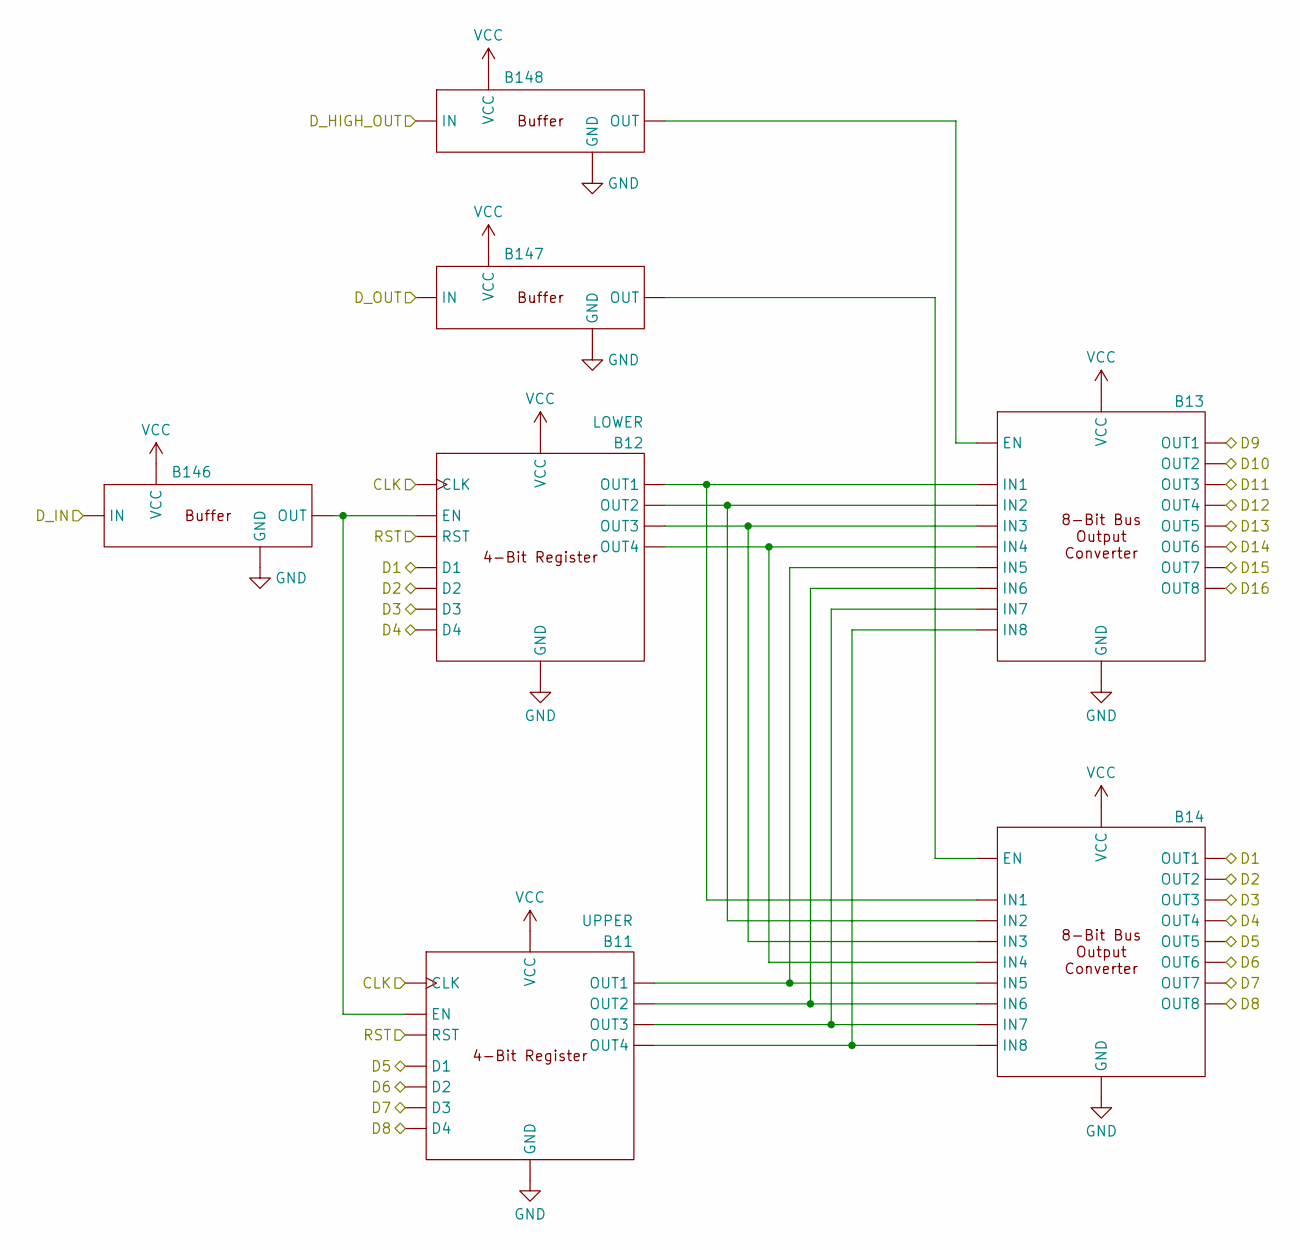
[picture p74: schematic D Register.kicad_sch]

Parts:
B11: UPPER
B12: LOWER
B13, B14, B146, B147, B148: (no value)

Connections:
CLK: B11., B12.
D1: B12., B14.
D2: B12., B14.
D3: B12., B14.
D4: B12., B14.
D5: B11., B14.
D6: B11., B14.
D7: B11., B14.
D8: B11., B14.
D9: B13.
D10: B13.
D11: B13.
D12: B13.
D13: B13.
D14: B13.
D15: B13.
D16: B13.
D_HIGH_OUT: B148.
D_IN: B146.
D_OUT: B147.
GND: B11., B12., B13., B14., B146., B147., B148.
unnamed: B11., B12., B13., B14., B146.
unnamed: B12., B13., B14.
unnamed: B13., B148.
unnamed: B14., B147.
RST: B11., B12.
VCC: B11., B12., B13., B14., B146., B147., B148.
