DragonMinded/minidragon/schematics/Layout/Decoder Combinatorial Logic and ROM Boards.kicad_sch

## KiCad design schematics/Layout/Decoder Combinatorial Logic and ROM Boards.kicad_sch (2026-08-19)

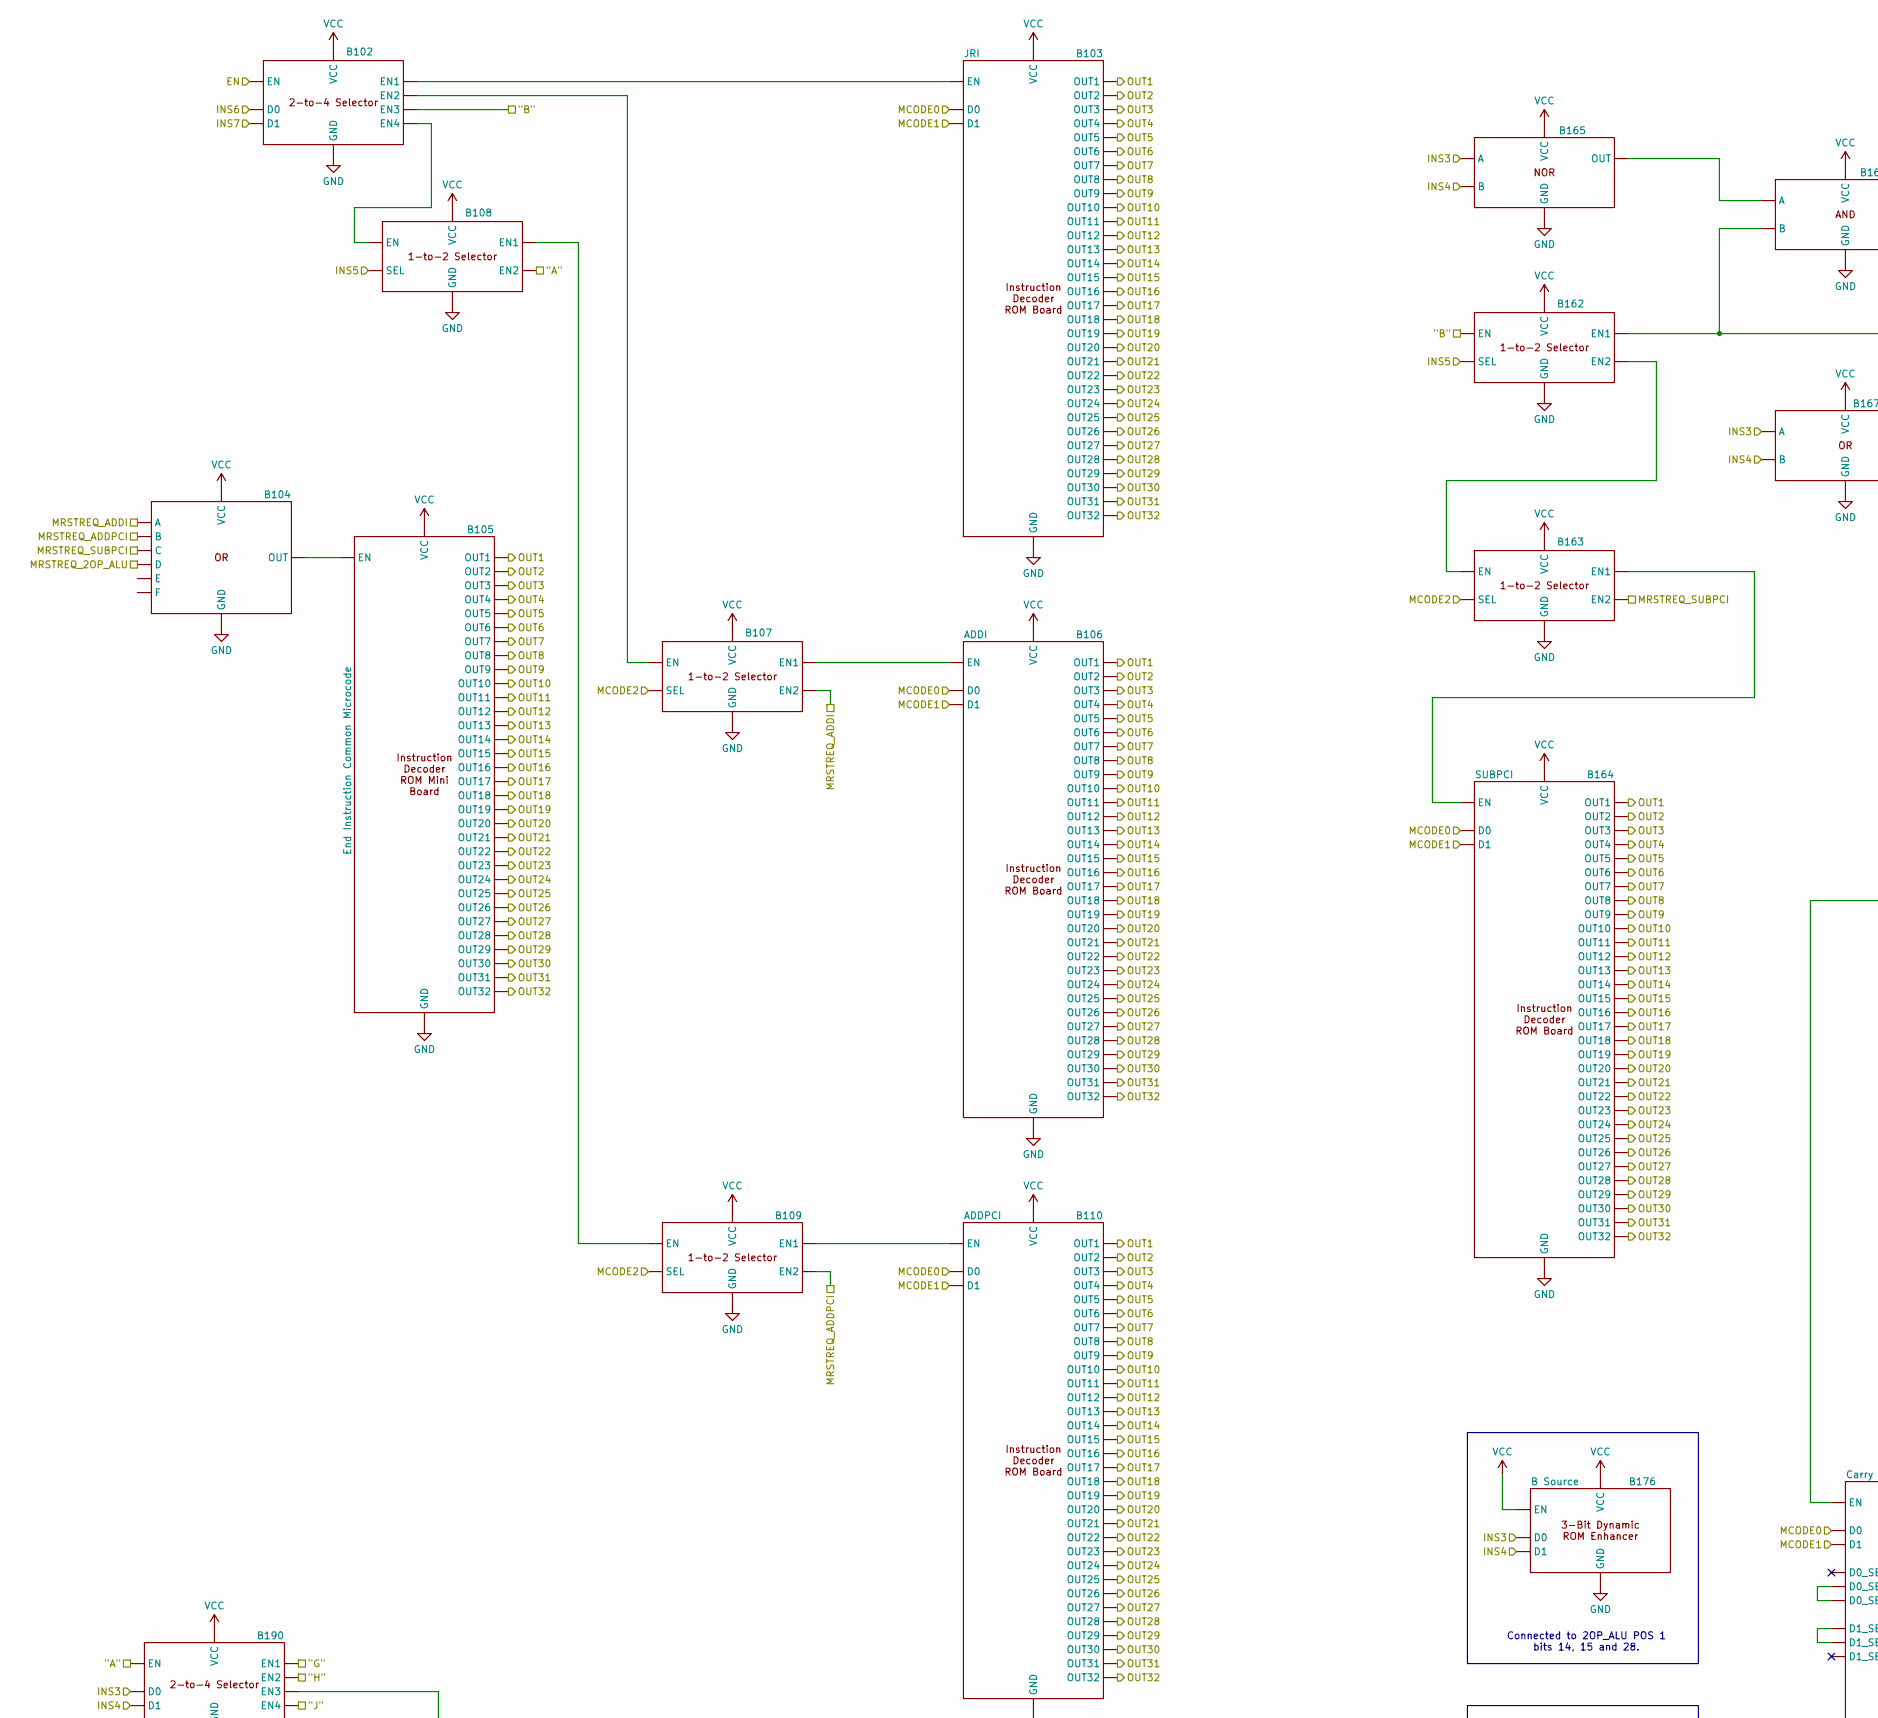
[picture p76: schematic Decoder Combinatorial Logic and ROM Boards.kicad_sch, part in row 1, column 1]

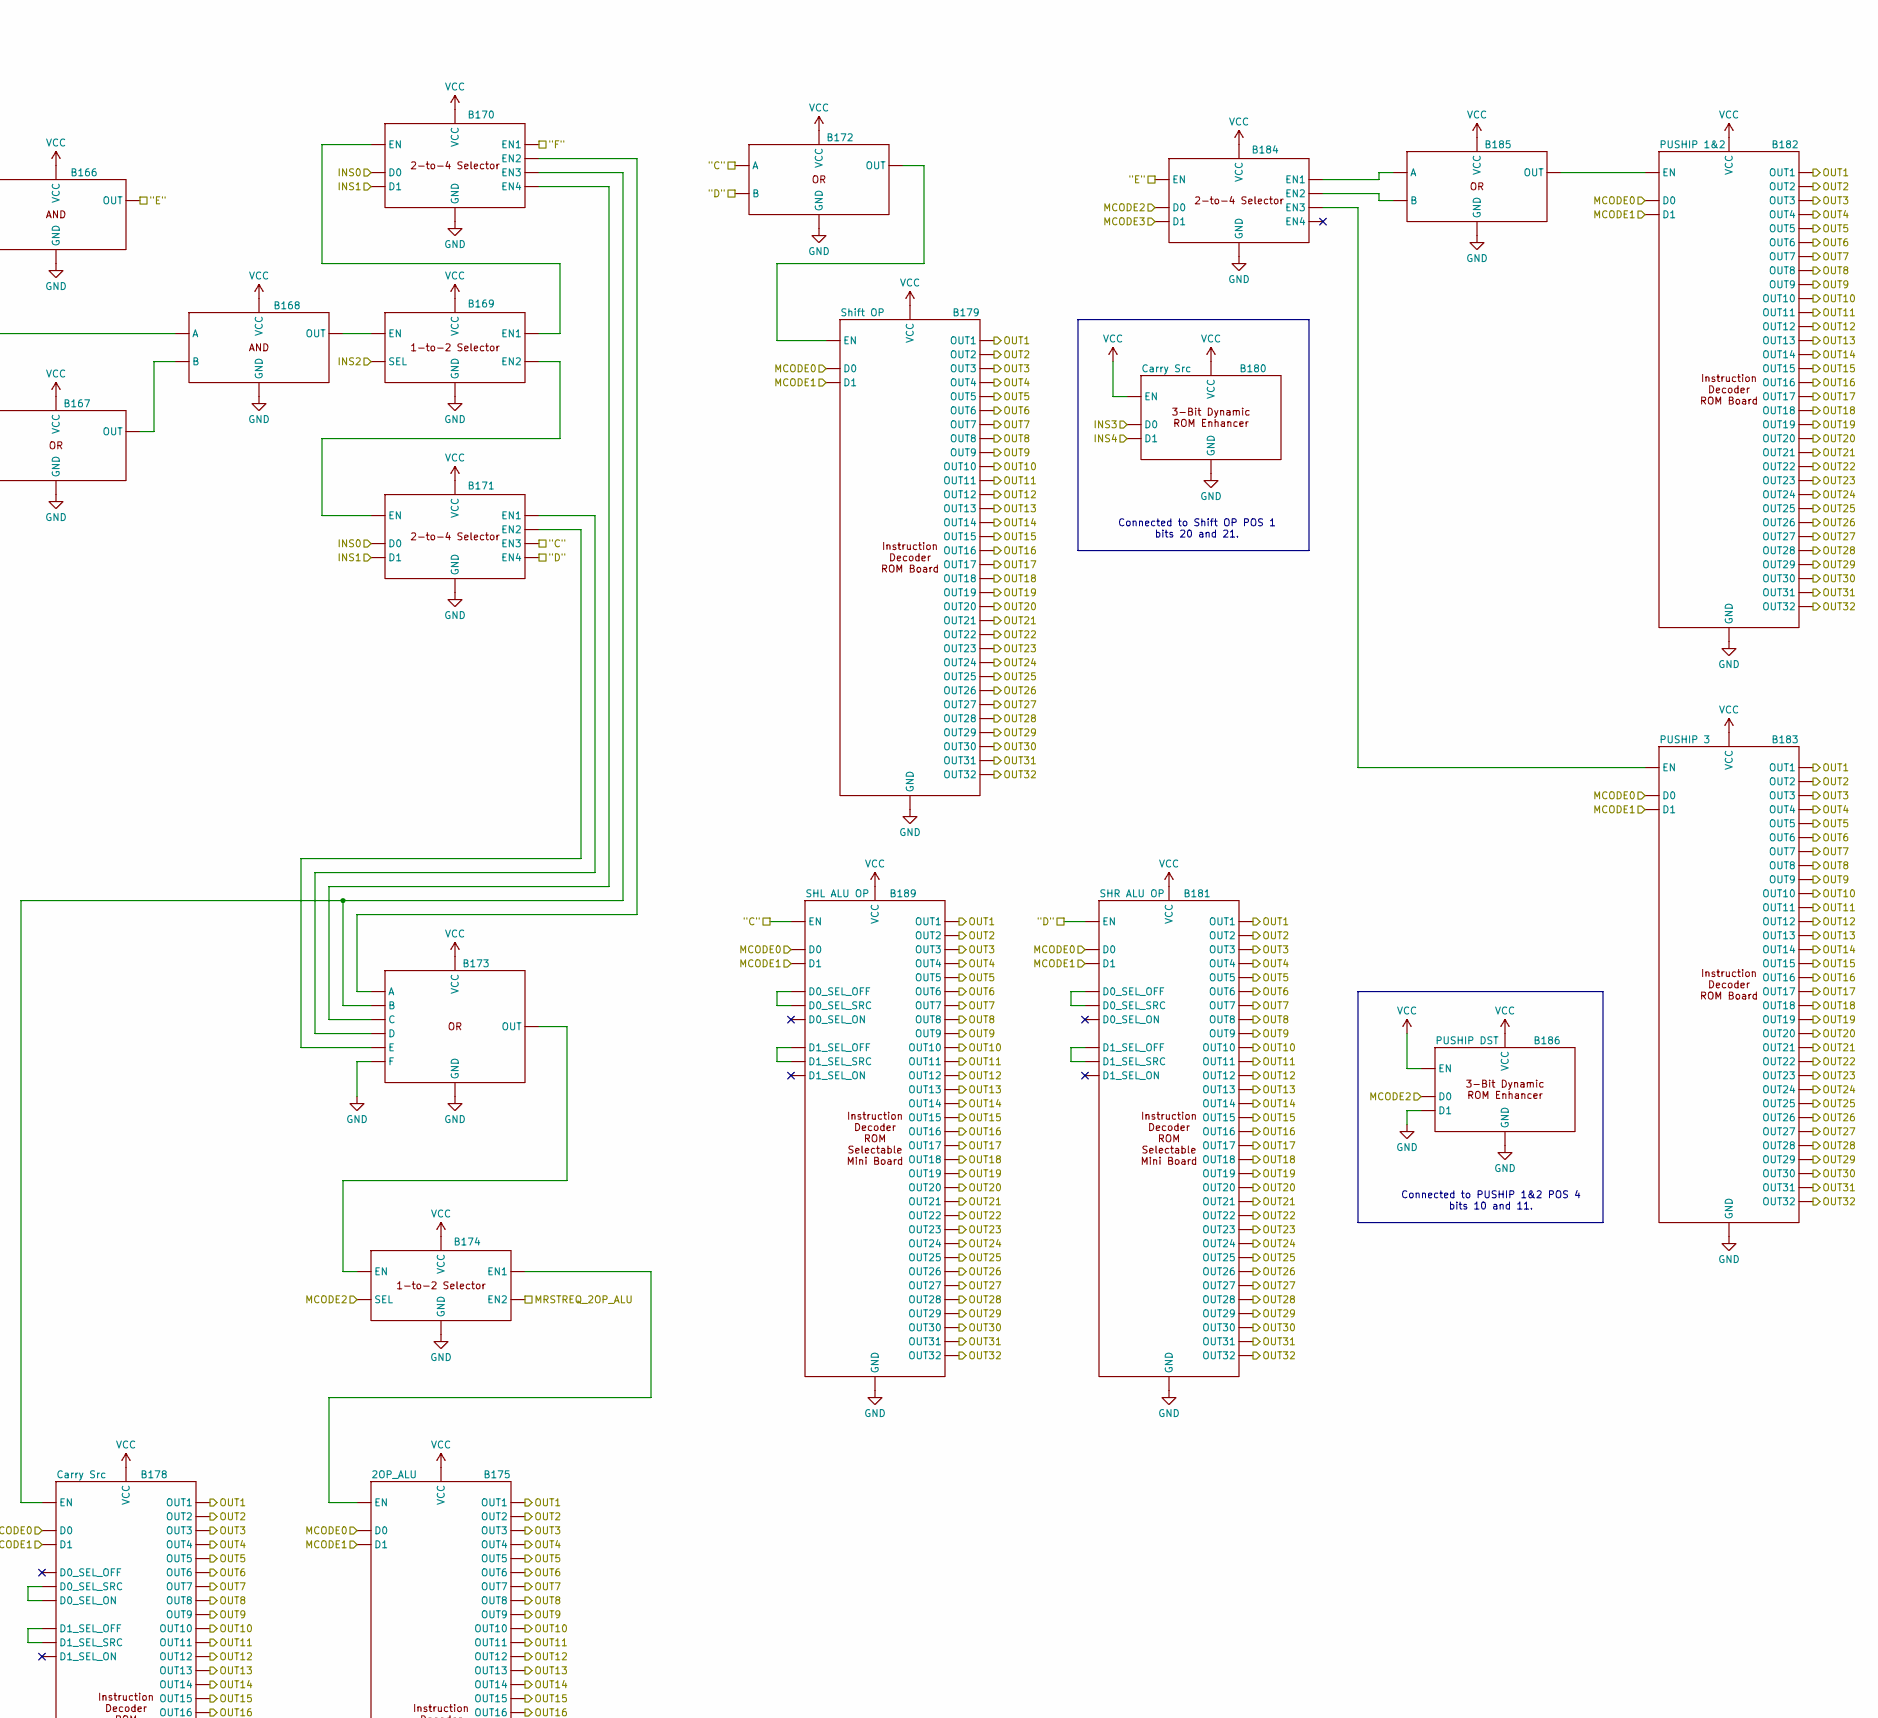
[picture p77: schematic Decoder Combinatorial Logic and ROM Boards.kicad_sch, part in row 1, column 2]

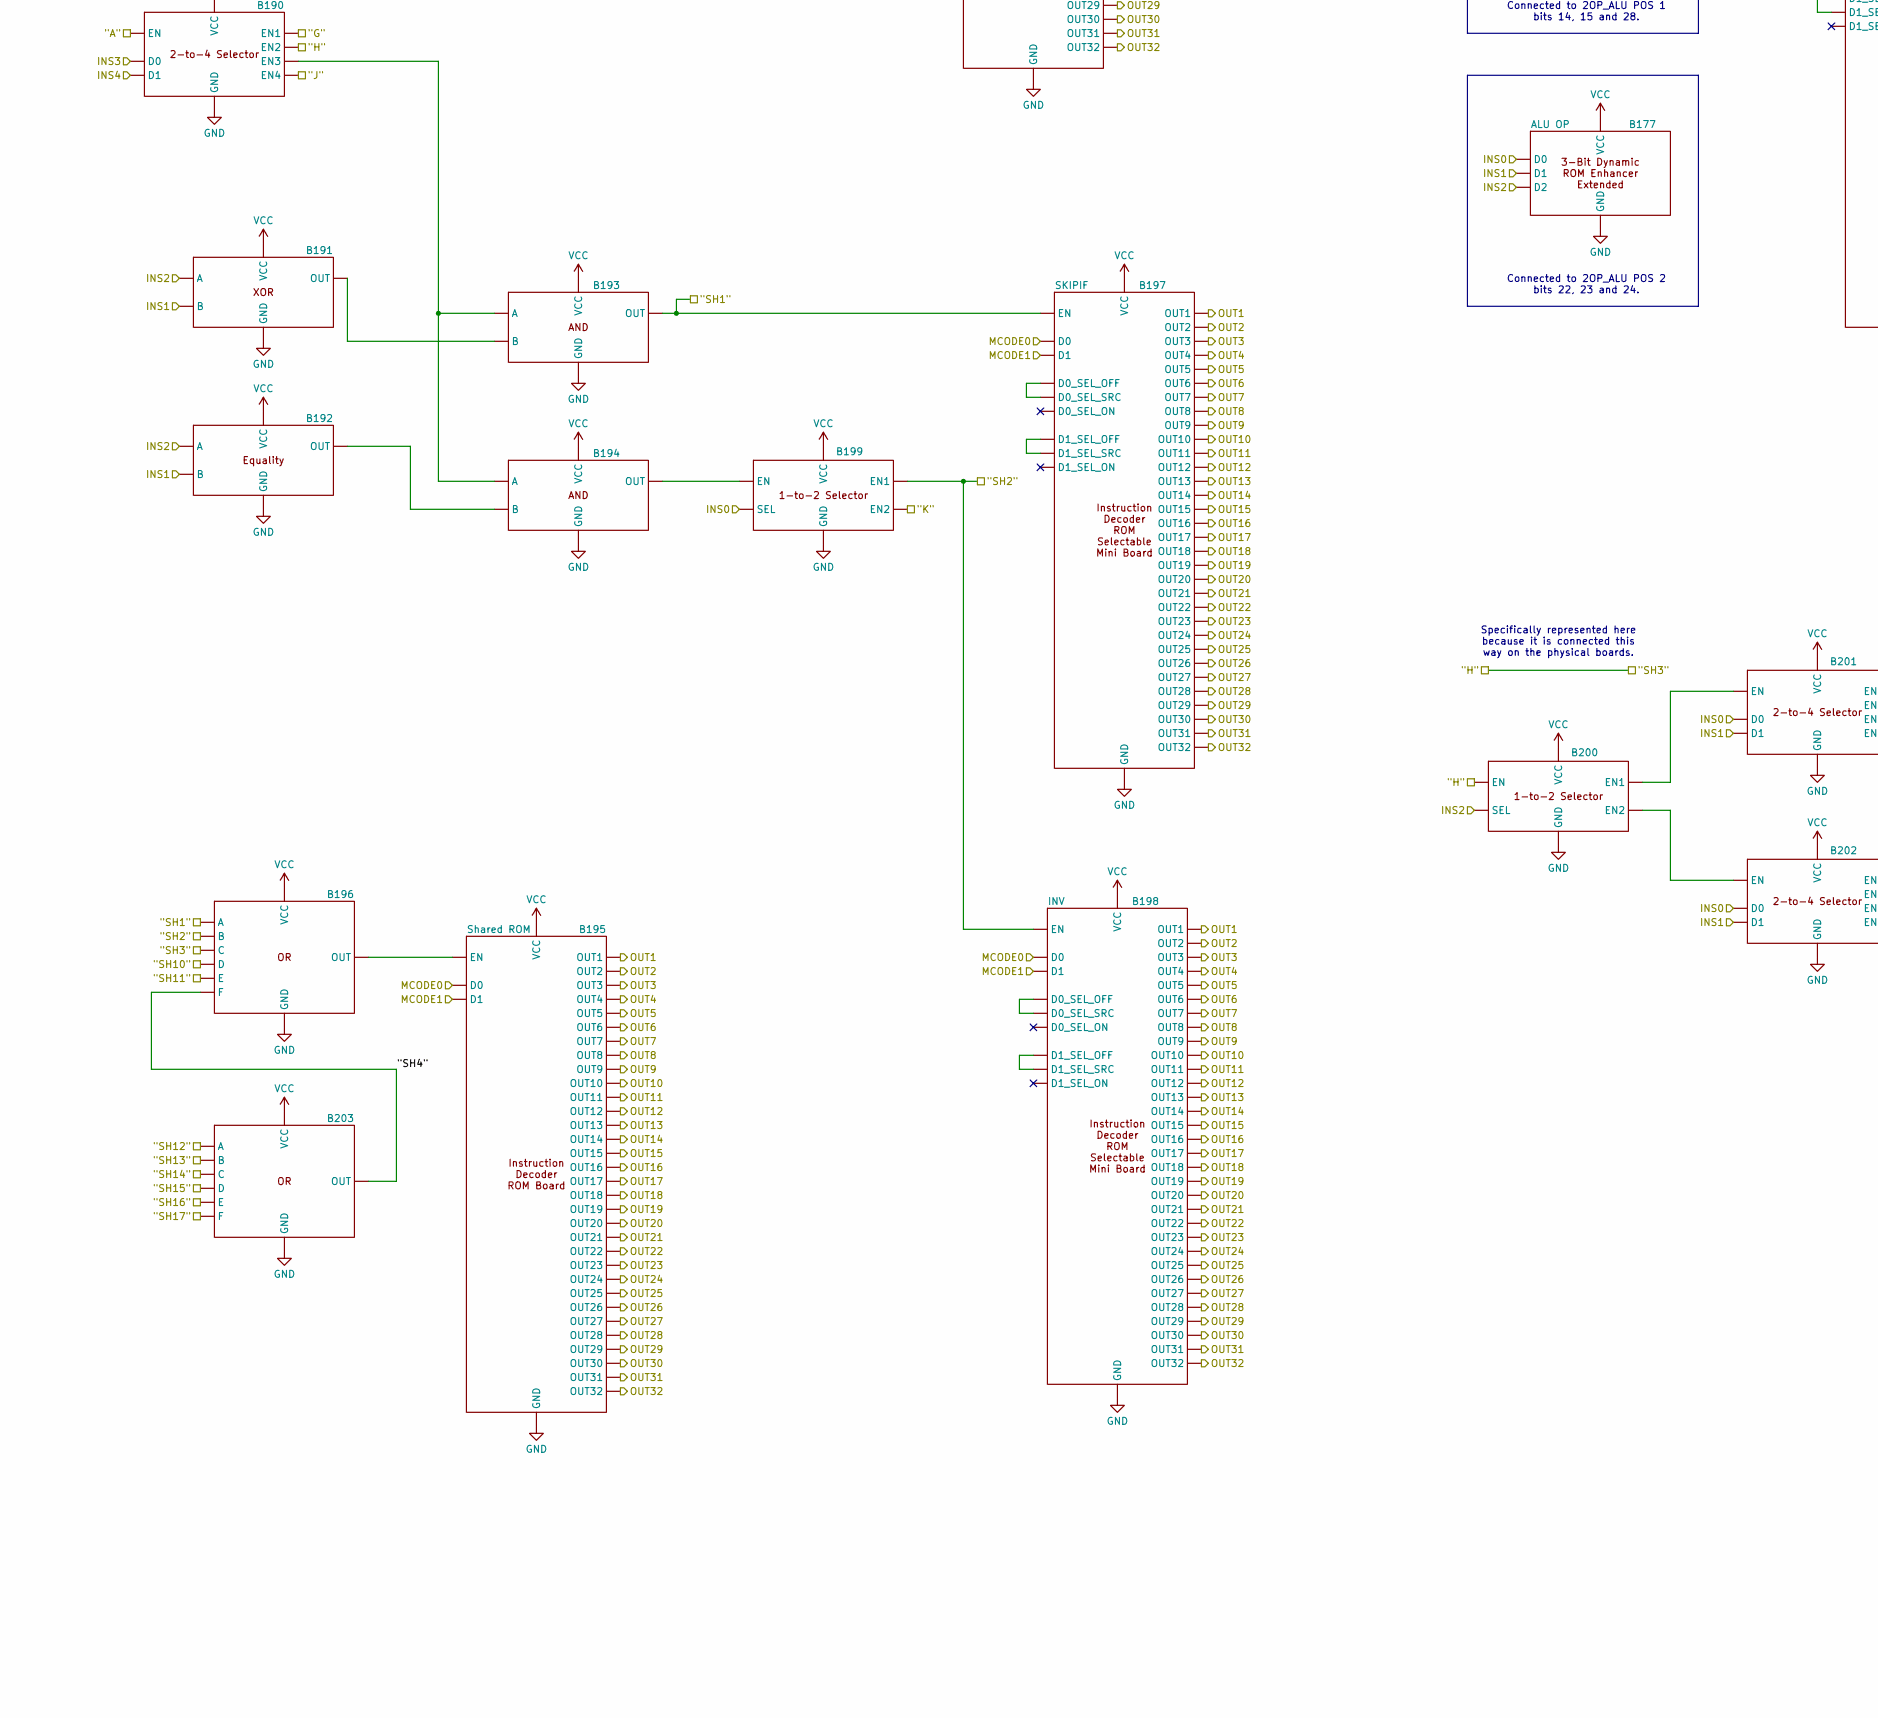
[picture p78: schematic Decoder Combinatorial Logic and ROM Boards.kicad_sch, part in row 2, column 1]

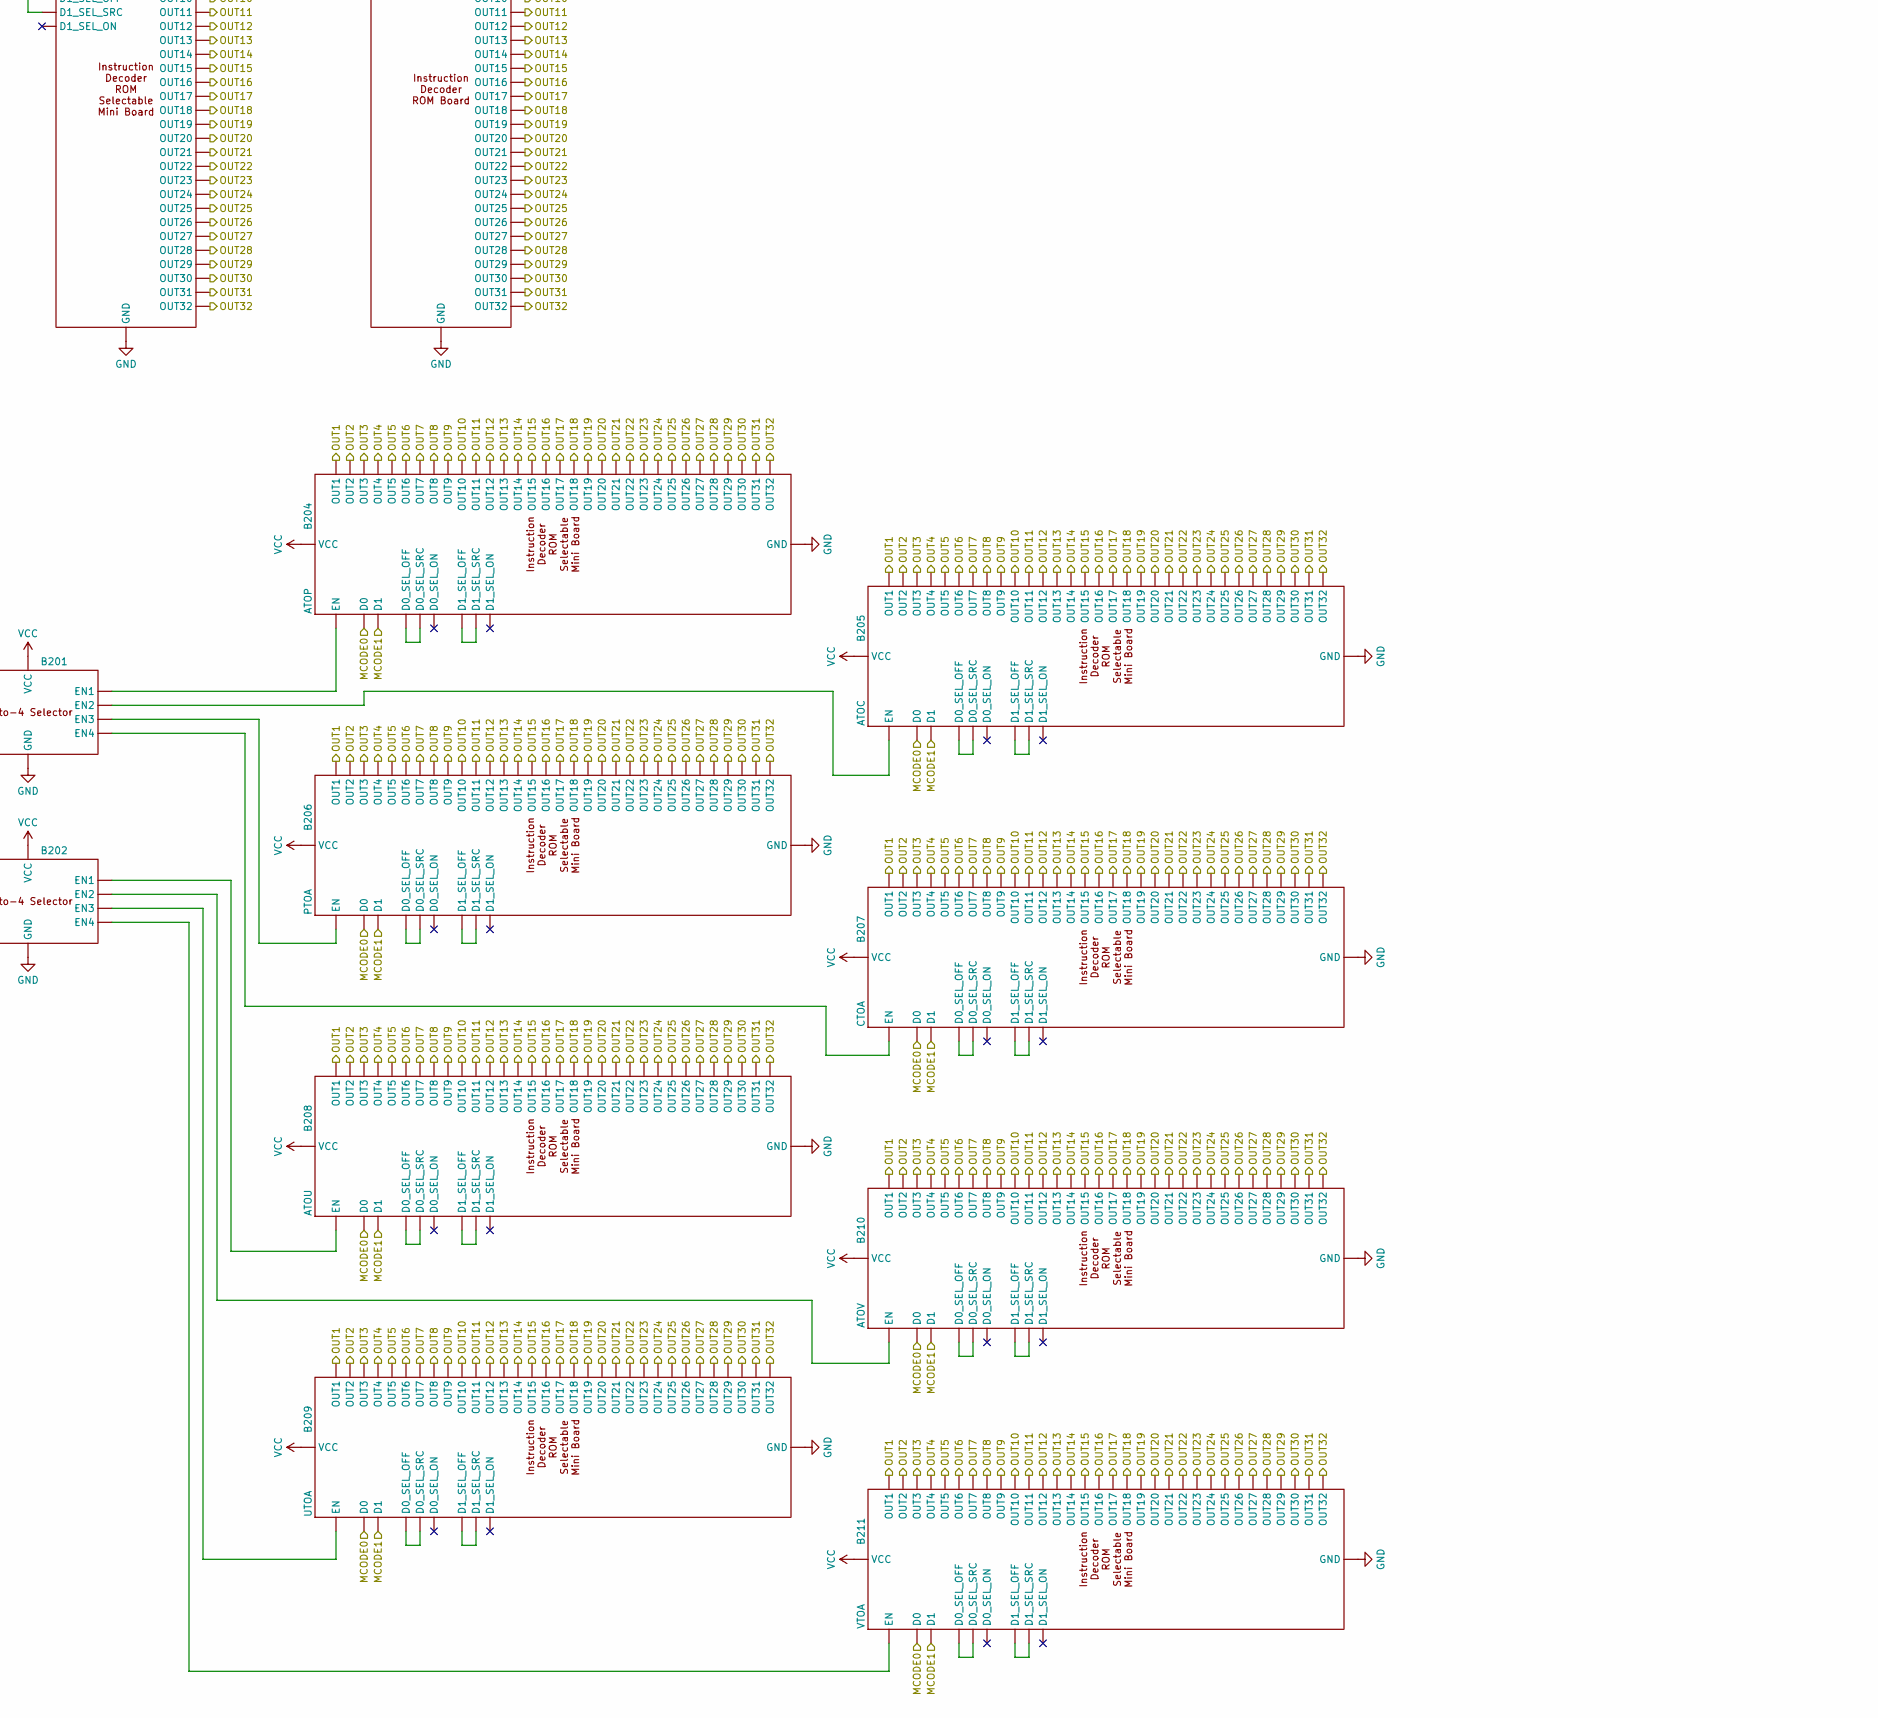
[picture p79: schematic Decoder Combinatorial Logic and ROM Boards.kicad_sch, part in row 2, column 2]

Parts:
B102, B104, B107, B108, B109, B162, B163, B165, B166, B167, B168, B169, B170, B171, B172, B173, B174, B184, B185, B190, B191, B192, B193, B194, B196, B199, B200, B201, B202, B203: (no value)
B103: JRI
B105: End Instruction Common Microcode
B106: ADDI
B110: ADDPCI
B164: SUBPCI
B175: 2OP_ALU
B176: B Source
B177: ALU OP
B178, B180: Carry Src
B179: Shift OP
B181: SHR ALU OP
B182: PUSHIP 1&2
B183: PUSHIP 3
B186: PUSHIP DST
B189: SHL ALU OP
B195: Shared ROM
B197: SKIPIF
B198: INV
B204: ATOP
B205: ATOC
B206: PTOA
B207: CTOA
B208: ATOU
B209: UTOA
B210: ATOV
B211: VTOA

Connections:
"A": B108., B190.
"B": B102., B162.
"C": B171., B172., B189.
"D": B171., B172., B181.
"E": B166., B184.
"F": B170.
"G": B190.
"H": B190., B196., B200.
"J": B190.
"K": B199.
"SH1": B193., B196., B197.
"SH2": B196., B198., B199.
"SH4": B196., B203.
"SH10": B196.
"SH11": B196.
"SH12": B203.
"SH13": B203.
"SH14": B203.
"SH15": B203.
"SH16": B203.
"SH17": B203.
EN: B102.
GND: B102., B103., B104., B105., B106., B107., B108., B109., B110., B162., B163., B164., B165., B166., B167., B168., B169., B170., B171., B172., B173., B174., B175., B176., B177., B178., B179., B180., B181., B182., B183., B184., B185., B186., B189., B190., B191., B192., B193., B194., B195., B196., B197., B198., B199., B200., B201., B202., B203., B204., B205., B206., B207., B208., B209., B210., B211.
INS0: B170., B171., B177., B199., B201., B202.
INS1: B170., B171., B177., B191., B192., B201., B202.
INS2: B169., B177., B191., B192., B200.
INS3: B165., B167., B176., B180., B190.
INS4: B165., B167., B176., B180., B190.
INS5: B108., B162.
INS6: B102.
INS7: B102.
MCODE0: B103., B106., B110., B164., B175., B178., B179., B181., B182., B183., B189., B195., B197., B198., B204., B205., B206., B207., B208., B209., B210., B211.
MCODE1: B103., B106., B110., B164., B175., B178., B179., B181., B182., B183., B189., B195., B197., B198., B204., B205., B206., B207., B208., B209., B210., B211.
MCODE2: B107., B109., B163., B174., B184., B186.
MCODE3: B184.
MRSTREQ_2OP_ALU: B104., B174.
MRSTREQ_ADDI: B104., B107.
MRSTREQ_ADDPCI: B104., B109.
MRSTREQ_SUBPCI: B104., B163.
unnamed: B102., B103., B107., B108.
unnamed: B104., B105.
unnamed: B106., B107.
unnamed: B108., B109.
unnamed: B109., B110.
unnamed: B162., B163., B166., B168.
unnamed: B163., B164.
unnamed: B165., B166.
unnamed: B167., B168.
unnamed: B168., B169.
unnamed: B169., B170., B171.
unnamed: B170., B173., B178.
unnamed: B171., B173.
unnamed: B172., B179.
unnamed: B173., B174.
unnamed: B174., B175.
unnamed: B182., B185.
unnamed: B183., B184.
unnamed: B184., B185.
unnamed: B190., B193., B194.
unnamed: B191., B193.
unnamed: B192., B194.
unnamed: B194., B199.
unnamed: B195., B196.
unnamed: B200., B201., B202.
unnamed: B201., B204., B205., B206., B207.
unnamed: B202., B208., B209., B210., B211.
OUT1: B103., B105., B106., B110., B164., B175., B178., B179., B181., B182., B183., B189., B195., B197., B198., B204., B205., B206., B207., B208., B209., B210., B211.
OUT2: B103., B105., B106., B110., B164., B175., B178., B179., B181., B182., B183., B189., B195., B197., B198., B204., B205., B206., B207., B208., B209., B210., B211.
OUT3: B103., B105., B106., B110., B164., B175., B178., B179., B181., B182., B183., B189., B195., B197., B198., B204., B205., B206., B207., B208., B209., B210., B211.
OUT4: B103., B105., B106., B110., B164., B175., B178., B179., B181., B182., B183., B189., B195., B197., B198., B204., B205., B206., B207., B208., B209., B210., B211.
OUT5: B103., B105., B106., B110., B164., B175., B178., B179., B181., B182., B183., B189., B195., B197., B198., B204., B205., B206., B207., B208., B209., B210., B211.
OUT6: B103., B105., B106., B110., B164., B175., B178., B179., B181., B182., B183., B189., B195., B197., B198., B204., B205., B206., B207., B208., B209., B210., B211.
OUT7: B103., B105., B106., B110., B164., B175., B178., B179., B181., B182., B183., B189., B195., B197., B198., B204., B205., B206., B207., B208., B209., B210., B211.
OUT8: B103., B105., B106., B110., B164., B175., B178., B179., B181., B182., B183., B189., B195., B197., B198., B204., B205., B206., B207., B208., B209., B210., B211.
OUT9: B103., B105., B106., B110., B164., B175., B178., B179., B181., B182., B183., B189., B195., B197., B198., B204., B205., B206., B207., B208., B209., B210., B211.
OUT10: B103., B105., B106., B110., B164., B175., B178., B179., B181., B182., B183., B189., B195., B197., B198., B204., B205., B206., B207., B208., B209., B210., B211.
OUT11: B103., B105., B106., B110., B164., B175., B178., B179., B181., B182., B183., B189., B195., B197., B198., B204., B205., B206., B207., B208., B209., B210., B211.
OUT12: B103., B105., B106., B110., B164., B175., B178., B179., B181., B182., B183., B189., B195., B197., B198., B204., B205., B206., B207., B208., B209., B210., B211.
OUT13: B103., B105., B106., B110., B164., B175., B178., B179., B181., B182., B183., B189., B195., B197., B198., B204., B205., B206., B207., B208., B209., B210., B211.
OUT14: B103., B105., B106., B110., B164., B175., B178., B179., B181., B182., B183., B189., B195., B197., B198., B204., B205., B206., B207., B208., B209., B210., B211.
OUT15: B103., B105., B106., B110., B164., B175., B178., B179., B181., B182., B183., B189., B195., B197., B198., B204., B205., B206., B207., B208., B209., B210., B211.
OUT16: B103., B105., B106., B110., B164., B175., B178., B179., B181., B182., B183., B189., B195., B197., B198., B204., B205., B206., B207., B208., B209., B210., B211.
OUT17: B103., B105., B106., B110., B164., B175., B178., B179., B181., B182., B183., B189., B195., B197., B198., B204., B205., B206., B207., B208., B209., B210., B211.
OUT18: B103., B105., B106., B110., B164., B175., B178., B179., B181., B182., B183., B189., B195., B197., B198., B204., B205., B206., B207., B208., B209., B210., B211.
OUT19: B103., B105., B106., B110., B164., B175., B178., B179., B181., B182., B183., B189., B195., B197., B198., B204., B205., B206., B207., B208., B209., B210., B211.
OUT20: B103., B105., B106., B110., B164., B175., B178., B179., B181., B182., B183., B189., B195., B197., B198., B204., B205., B206., B207., B208., B209., B210., B211.
OUT21: B103., B105., B106., B110., B164., B175., B178., B179., B181., B182., B183., B189., B195., B197., B198., B204., B205., B206., B207., B208., B209., B210., B211.
OUT22: B103., B105., B106., B110., B164., B175., B178., B179., B181., B182., B183., B189., B195., B197., B198., B204., B205., B206., B207., B208., B209., B210., B211.
OUT23: B103., B105., B106., B110., B164., B175., B178., B179., B181., B182., B183., B189., B195., B197., B198., B204., B205., B206., B207., B208., B209., B210., B211.
OUT24: B103., B105., B106., B110., B164., B175., B178., B179., B181., B182., B183., B189., B195., B197., B198., B204., B205., B206., B207., B208., B209., B210., B211.
OUT25: B103., B105., B106., B110., B164., B175., B178., B179., B181., B182., B183., B189., B195., B197., B198., B204., B205., B206., B207., B208., B209., B210., B211.
OUT26: B103., B105., B106., B110., B164., B175., B178., B179., B181., B182., B183., B189., B195., B197., B198., B204., B205., B206., B207., B208., B209., B210., B211.
OUT27: B103., B105., B106., B110., B164., B175., B178., B179., B181., B182., B183., B189., B195., B197., B198., B204., B205., B206., B207., B208., B209., B210., B211.
OUT28: B103., B105., B106., B110., B164., B175., B178., B179., B181., B182., B183., B189., B195., B197., B198., B204., B205., B206., B207., B208., B209., B210., B211.
OUT29: B103., B105., B106., B110., B164., B175., B178., B179., B181., B182., B183., B189., B195., B197., B198., B204., B205., B206., B207., B208., B209., B210., B211.
OUT30: B103., B105., B106., B110., B164., B175., B178., B179., B181., B182., B183., B189., B195., B197., B198., B204., B205., B206., B207., B208., B209., B210., B211.
OUT31: B103., B105., B106., B110., B164., B175., B178., B179., B181., B182., B183., B189., B195., B197., B198., B204., B205., B206., B207., B208., B209., B210., B211.
OUT32: B103., B105., B106., B110., B164., B175., B178., B179., B181., B182., B183., B189., B195., B197., B198., B204., B205., B206., B207., B208., B209., B210., B211.
VCC: B102., B103., B104., B105., B106., B107., B108., B109., B110., B162., B163., B164., B165., B166., B167., B168., B169., B170., B171., B172., B173., B174., B175., B176., B177., B178., B179., B180., B181., B182., B183., B184., B185., B186., B189., B190., B191., B192., B193., B194., B195., B196., B197., B198., B199., B200., B201., B202., B203., B204., B205., B206., B207., B208., B209., B210., B211.

Notes on the sheet:
Connected to PUSHIP 1&2 POS 4 bits 10 and 11.
Connected to Shift OP POS 1 bits 20 and 21.
Specifically represented here because it is connected this way on the physical boards.
Connected to 2OP_ALU POS 1 bits 14, 15 and 28.
Connected to 2OP_ALU POS 2 bits 22, 23 and 24.
