DragonMinded/minidragon/schematics/Layout/IP Register.kicad_sch

## KiCad design schematics/Layout/IP Register.kicad_sch (2026-07-15)

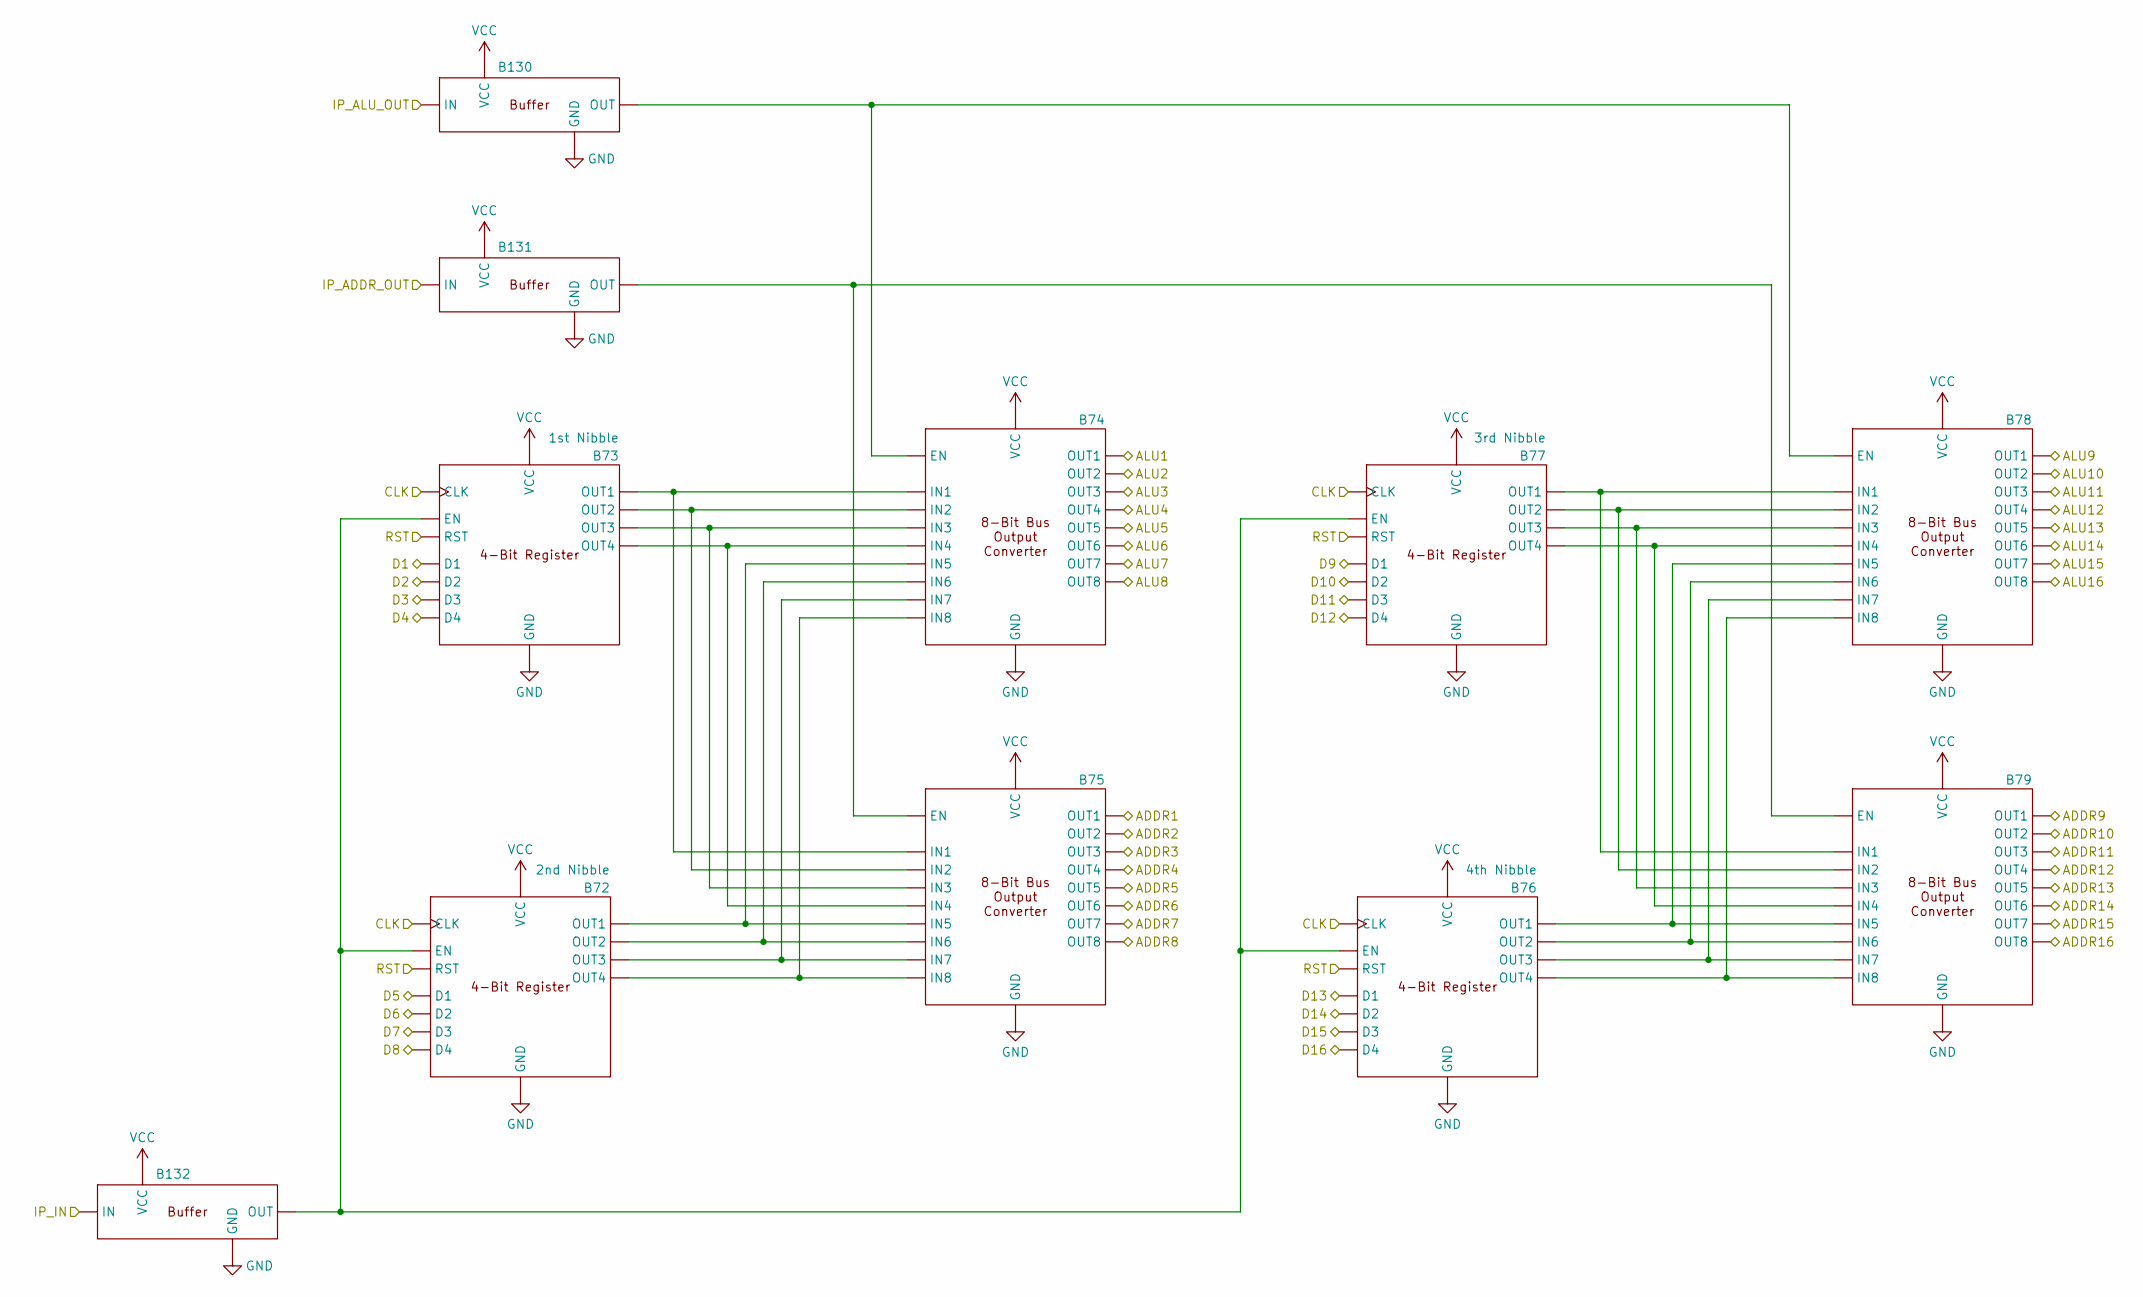
[picture p81: schematic IP Register.kicad_sch]

Parts:
B72: 2nd Nibble
B73: 1st Nibble
B74, B75, B78, B79, B130, B131, B132: (no value)
B76: 4th Nibble
B77: 3rd Nibble

Connections:
ADDR1: B75.
ADDR2: B75.
ADDR3: B75.
ADDR4: B75.
ADDR5: B75.
ADDR6: B75.
ADDR7: B75.
ADDR8: B75.
ADDR9: B79.
ADDR10: B79.
ADDR11: B79.
ADDR12: B79.
ADDR13: B79.
ADDR14: B79.
ADDR15: B79.
ADDR16: B79.
ALU1: B74.
ALU2: B74.
ALU3: B74.
ALU4: B74.
ALU5: B74.
ALU6: B74.
ALU7: B74.
ALU8: B74.
ALU9: B78.
ALU10: B78.
ALU11: B78.
ALU12: B78.
ALU13: B78.
ALU14: B78.
ALU15: B78.
ALU16: B78.
CLK: B72., B73., B76., B77.
D1: B73.
D2: B73.
D3: B73.
D4: B73.
D5: B72.
D6: B72.
D7: B72.
D8: B72.
D9: B77.
D10: B77.
D11: B77.
D12: B77.
D13: B76.
D14: B76.
D15: B76.
D16: B76.
GND: B72., B73., B74., B75., B76., B77., B78., B79., B130., B131., B132.
IP_ADDR_OUT: B131.
IP_ALU_OUT: B130.
IP_IN: B132.
unnamed: B72., B74., B75.
unnamed: B73., B74., B75.
unnamed: B76., B78., B79.
unnamed: B77., B78., B79.
unnamed: B74., B78., B130.
unnamed: B75., B79., B131.
unnamed: B72., B73., B76., B77., B132.
RST: B72., B73., B76., B77.
VCC: B72., B73., B74., B75., B76., B77., B78., B79., B130., B131., B132.
