DragonMinded/minidragon/schematics/Layout/Immediate Register.kicad_sch

## KiCad design schematics/Layout/Immediate Register.kicad_sch (2026-07-15)

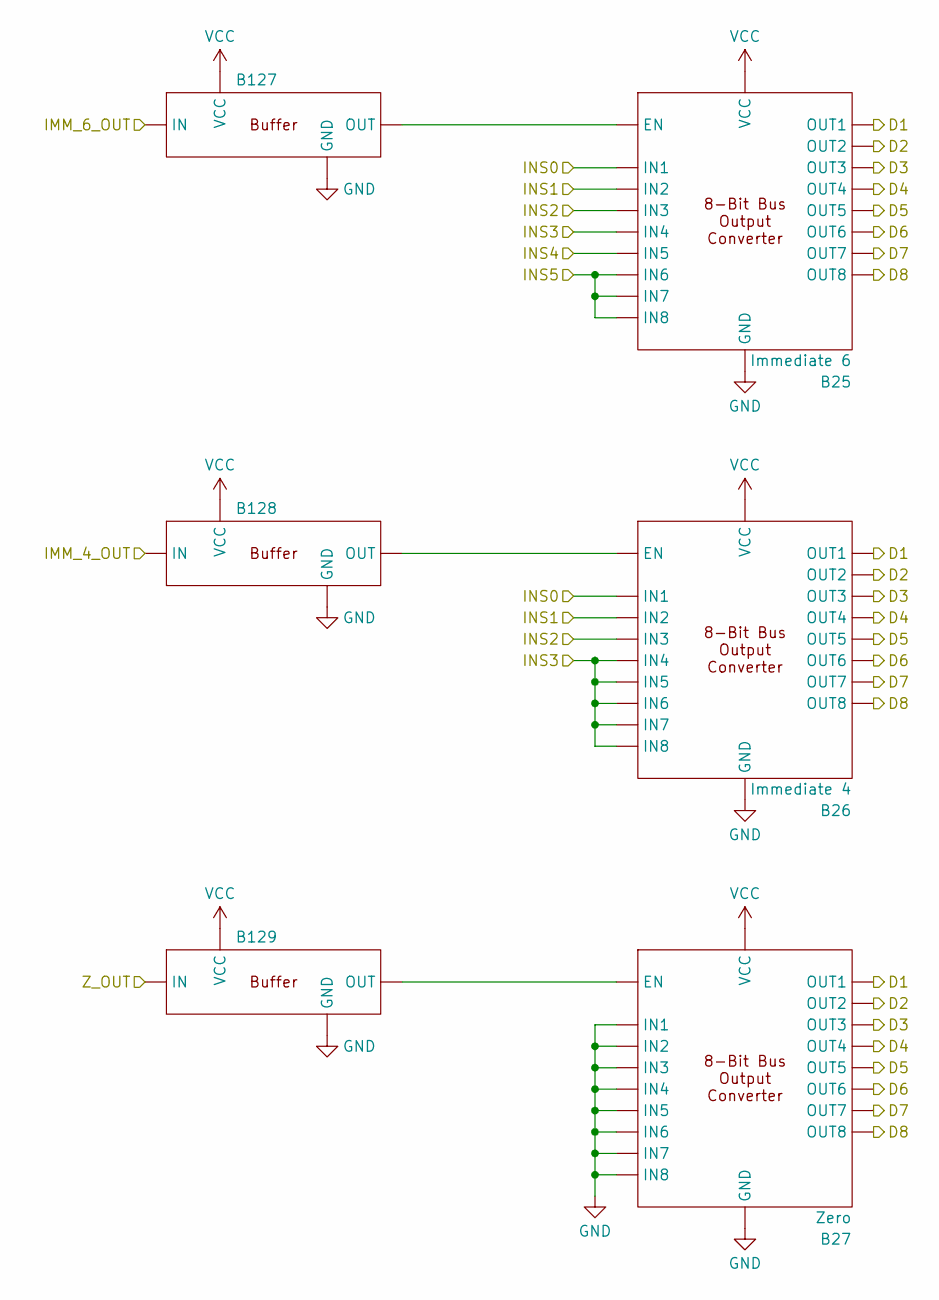
[picture p82: schematic Immediate Register.kicad_sch]

Parts:
B25: Immediate 6
B26: Immediate 4
B27: Zero
B127, B128, B129: (no value)

Connections:
D1: B25., B26., B27.
D2: B25., B26., B27.
D3: B25., B26., B27.
D4: B25., B26., B27.
D5: B25., B26., B27.
D6: B25., B26., B27.
D7: B25., B26., B27.
D8: B25., B26., B27.
GND: B25., B26., B27., B127., B128., B129.
IMM_4_OUT: B128.
IMM_6_OUT: B127.
INS0: B25., B26.
INS1: B25., B26.
INS2: B25., B26.
INS3: B25., B26.
INS4: B25.
INS5: B25.
unnamed: B25., B127.
unnamed: B26., B128.
unnamed: B27., B129.
VCC: B25., B26., B27., B127., B128., B129.
Z_OUT: B129.
