DragonMinded/minidragon/schematics/Layout/Instruction Decoder.kicad_sch

## KiCad design schematics/Layout/Instruction Decoder.kicad_sch (2026-07-29)

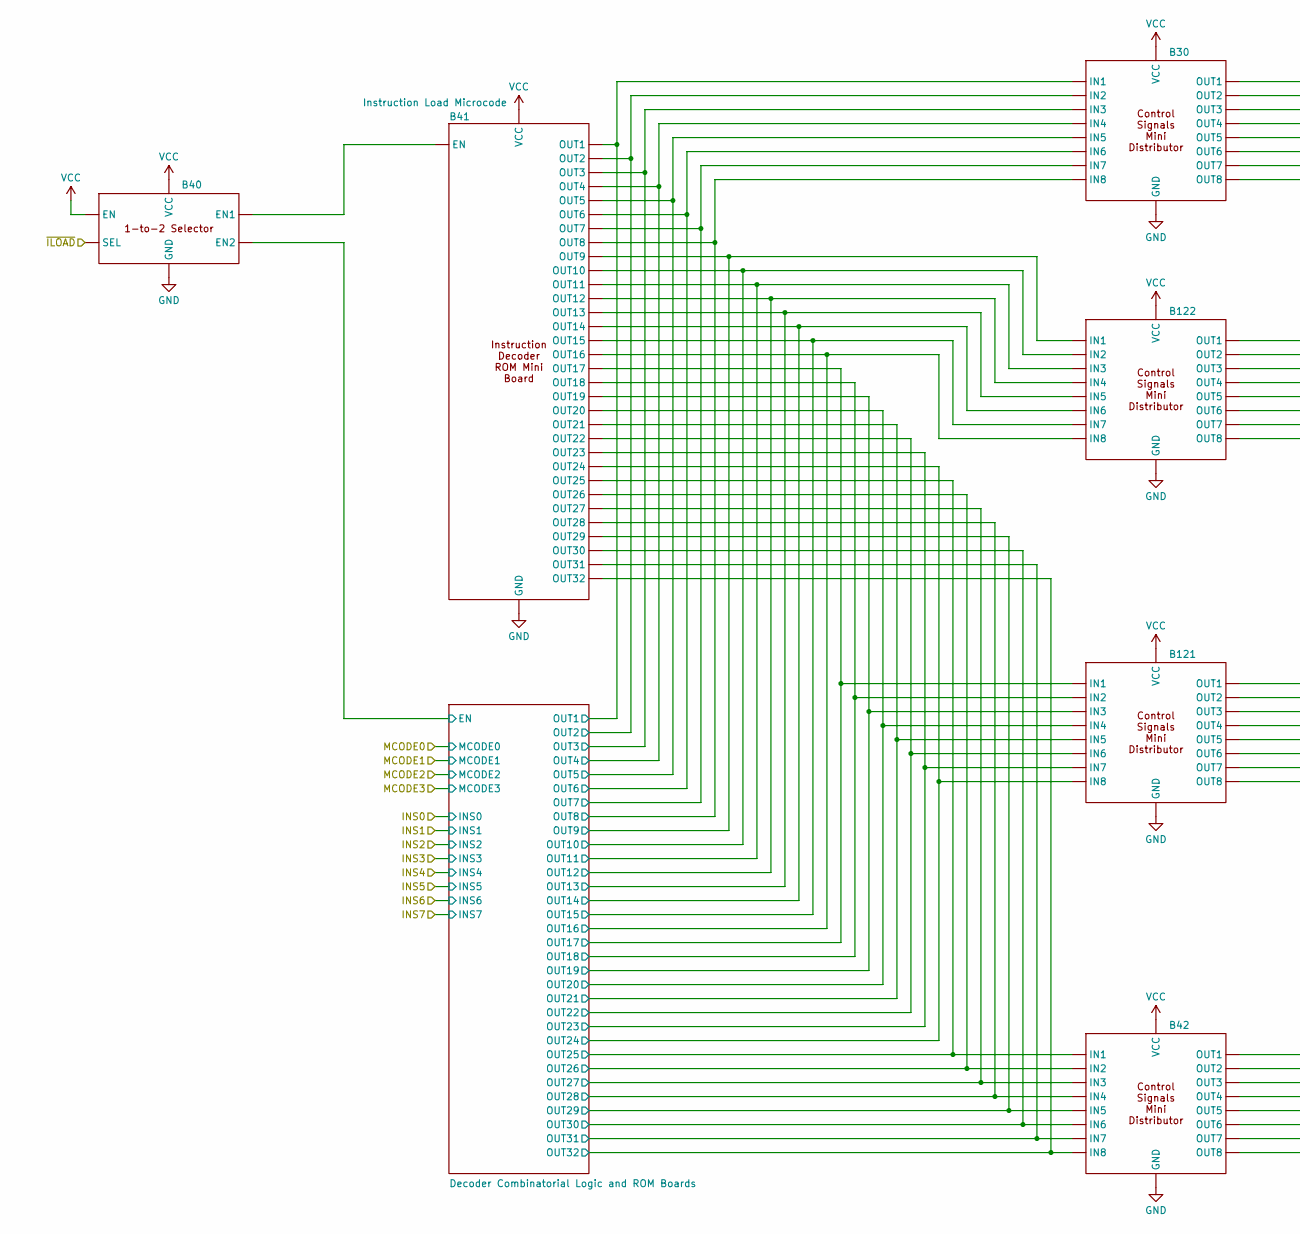
[picture p83: schematic Instruction Decoder.kicad_sch, part in row 1, column 1]

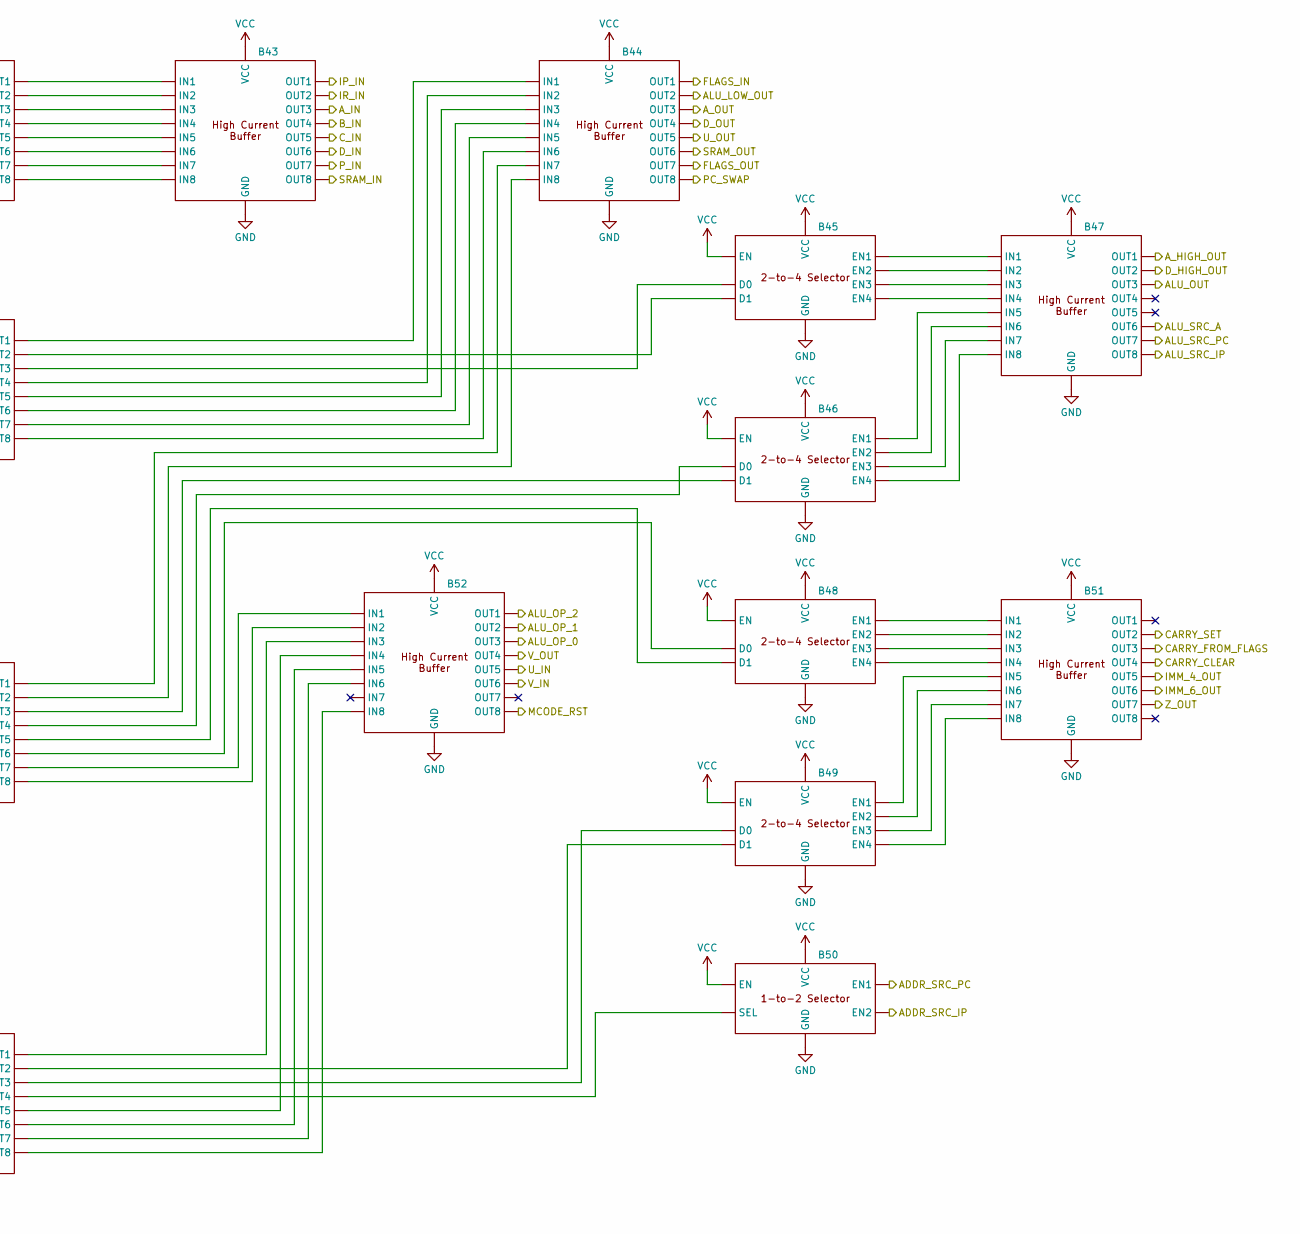
[picture p84: schematic Instruction Decoder.kicad_sch, part in row 1, column 2]

Parts:
B30, B40, B42, B43, B44, B45, B46, B47, B48, B49, B50, B51, B52, B121, B122: (no value)
B41: Instruction Load Microcode

Connections:
ADDR_SRC_IP: B50.
ADDR_SRC_PC: B50.
ALU_LOW_OUT: B44.
ALU_OP_0: B52.
ALU_OP_1: B52.
ALU_OP_2: B52.
ALU_OUT: B47.
ALU_SRC_A: B47.
ALU_SRC_IP: B47.
ALU_SRC_PC: B47.
A_HIGH_OUT: B47.
A_IN: B43.
A_OUT: B44.
B_IN: B43.
CARRY_CLEAR: B51.
CARRY_FROM_FLAGS: B51.
CARRY_SET: B51.
C_IN: B43.
D_HIGH_OUT: B47.
D_IN: B43.
D_OUT: B44.
EN: B40.
FLAGS_IN: B44.
FLAGS_OUT: B44.
GND: B30., B40., B41., B42., B43., B44., B45., B46., B47., B48., B49., B50., B51., B52., B121., B122.
IMM_4_OUT: B51.
IMM_6_OUT: B51.
IP_IN: B43.
IR_IN: B43.
MCODE_RST: B52.
unnamed: B30., B43.
unnamed: B40., B41.
unnamed: B42., B49., B50., B52.
unnamed: B45., B47.
unnamed: B46., B47.
unnamed: B48., B51.
unnamed: B49., B51.
unnamed: B44., B46., B48., B52., B121.
unnamed: B44., B45., B122.
OUT1: B30., B41.
OUT2: B30., B41.
OUT3: B30., B41.
OUT4: B30., B41.
OUT5: B30., B41.
OUT6: B30., B41.
OUT7: B30., B41.
OUT8: B30., B41.
OUT9: B41., B122.
OUT10: B41., B122.
OUT11: B41., B122.
OUT12: B41., B122.
OUT13: B41., B122.
OUT14: B41., B122.
OUT15: B41., B122.
OUT16: B41., B122.
OUT17: B41., B121.
OUT18: B41., B121.
OUT19: B41., B121.
OUT20: B41., B121.
OUT21: B41., B121.
OUT22: B41., B121.
OUT23: B41., B121.
OUT24: B41., B121.
OUT25: B41., B42.
OUT26: B41., B42.
OUT27: B41., B42.
OUT28: B41., B42.
OUT29: B41., B42.
OUT30: B41., B42.
OUT31: B41., B42.
OUT32: B41., B42.
PC_SWAP: B44.
P_IN: B43.
SRAM_IN: B43.
SRAM_OUT: B44.
U_IN: B52.
U_OUT: B44.
VCC: B30., B40., B41., B42., B43., B44., B45., B46., B47., B48., B49., B50., B51., B52., B121., B122.
V_IN: B52.
V_OUT: B52.
Z_OUT: B51.
~ILOAD: B40.
