DragonMinded/minidragon/schematics/Layout/PC Register.kicad_sch

## KiCad design schematics/Layout/PC Register.kicad_sch (2026-07-15)

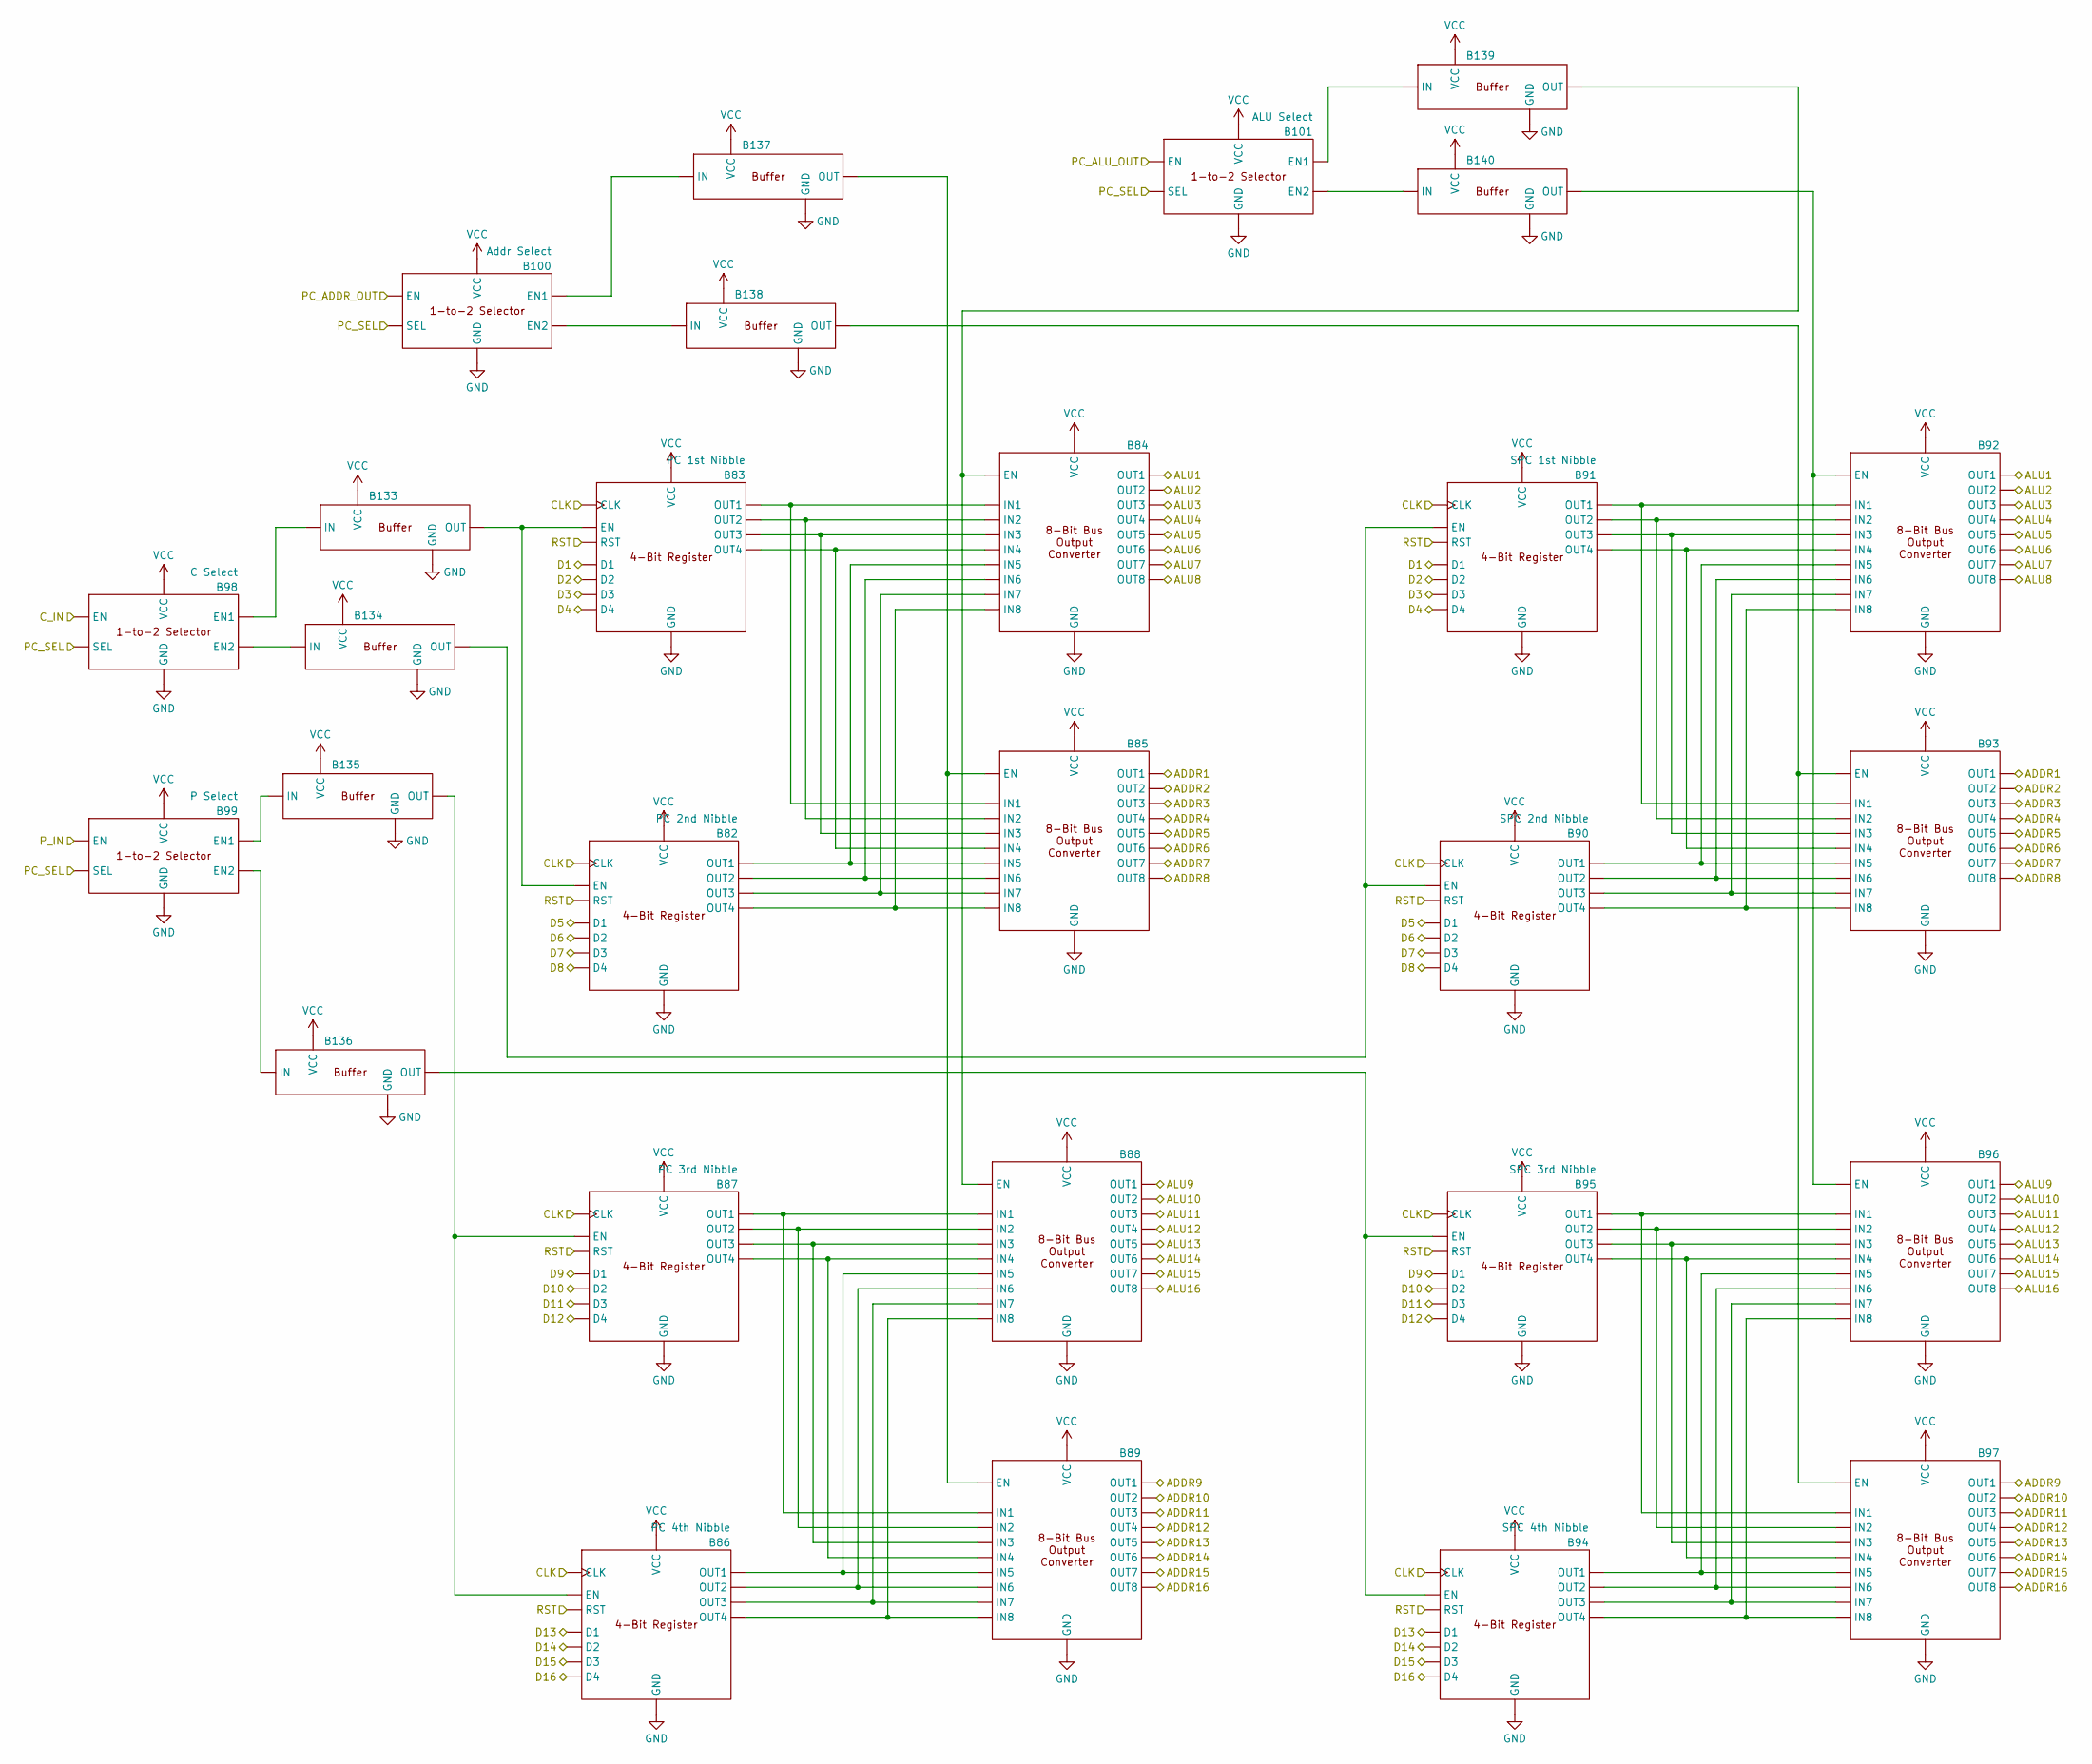
[picture p87: schematic PC Register.kicad_sch]

Parts:
B82: PC 2nd Nibble
B83: PC 1st Nibble
B84, B85, B88, B89, B92, B93, B96, B97, B133, B134, B135, B136, B137, B138, B139, B140: (no value)
B86: PC 4th Nibble
B87: PC 3rd Nibble
B90: SPC 2nd Nibble
B91: SPC 1st Nibble
B94: SPC 4th Nibble
B95: SPC 3rd Nibble
B98: C Select
B99: P Select
B100: Addr Select
B101: ALU Select

Connections:
ADDR1: B85., B93.
ADDR2: B85., B93.
ADDR3: B85., B93.
ADDR4: B85., B93.
ADDR5: B85., B93.
ADDR6: B85., B93.
ADDR7: B85., B93.
ADDR8: B85., B93.
ADDR9: B89., B97.
ADDR10: B89., B97.
ADDR11: B89., B97.
ADDR12: B89., B97.
ADDR13: B89., B97.
ADDR14: B89., B97.
ADDR15: B89., B97.
ADDR16: B89., B97.
ALU1: B84., B92.
ALU2: B84., B92.
ALU3: B84., B92.
ALU4: B84., B92.
ALU5: B84., B92.
ALU6: B84., B92.
ALU7: B84., B92.
ALU8: B84., B92.
ALU9: B88., B96.
ALU10: B88., B96.
ALU11: B88., B96.
ALU12: B88., B96.
ALU13: B88., B96.
ALU14: B88., B96.
ALU15: B88., B96.
ALU16: B88., B96.
CLK: B82., B83., B86., B87., B90., B91., B94., B95.
C_IN: B98.
D1: B83., B91.
D2: B83., B91.
D3: B83., B91.
D4: B83., B91.
D5: B82., B90.
D6: B82., B90.
D7: B82., B90.
D8: B82., B90.
D9: B87., B95.
D10: B87., B95.
D11: B87., B95.
D12: B87., B95.
D13: B86., B94.
D14: B86., B94.
D15: B86., B94.
D16: B86., B94.
GND: B82., B83., B84., B85., B86., B87., B88., B89., B90., B91., B92., B93., B94., B95., B96., B97., B98., B99., B100., B101., B133., B134., B135., B136., B137., B138., B139., B140.
unnamed: B82., B84., B85.
unnamed: B83., B84., B85.
unnamed: B86., B88., B89.
unnamed: B87., B88., B89.
unnamed: B90., B92., B93.
unnamed: B91., B92., B93.
unnamed: B94., B96., B97.
unnamed: B95., B96., B97.
unnamed: B100., B137., B138.
unnamed: B101., B139., B140.
unnamed: B82., B83., B98., B133.
unnamed: B90., B91., B98., B134.
unnamed: B86., B87., B99., B135.
unnamed: B94., B95., B99., B136.
unnamed: B85., B89., B137.
unnamed: B93., B97., B138.
unnamed: B84., B88., B139.
unnamed: B92., B96., B140.
PC_ADDR_OUT: B100.
PC_ALU_OUT: B101.
PC_SEL: B98., B99., B100., B101.
P_IN: B99.
RST: B82., B83., B86., B87., B90., B91., B94., B95.
VCC: B82., B83., B84., B85., B86., B87., B88., B89., B90., B91., B92., B93., B94., B95., B96., B97., B98., B99., B100., B101., B133., B134., B135., B136., B137., B138., B139., B140.
