DragonMinded/minidragon/schematics/Layout/V Register.kicad_sch

## KiCad design schematics/Layout/V Register.kicad_sch (2026-03-14)

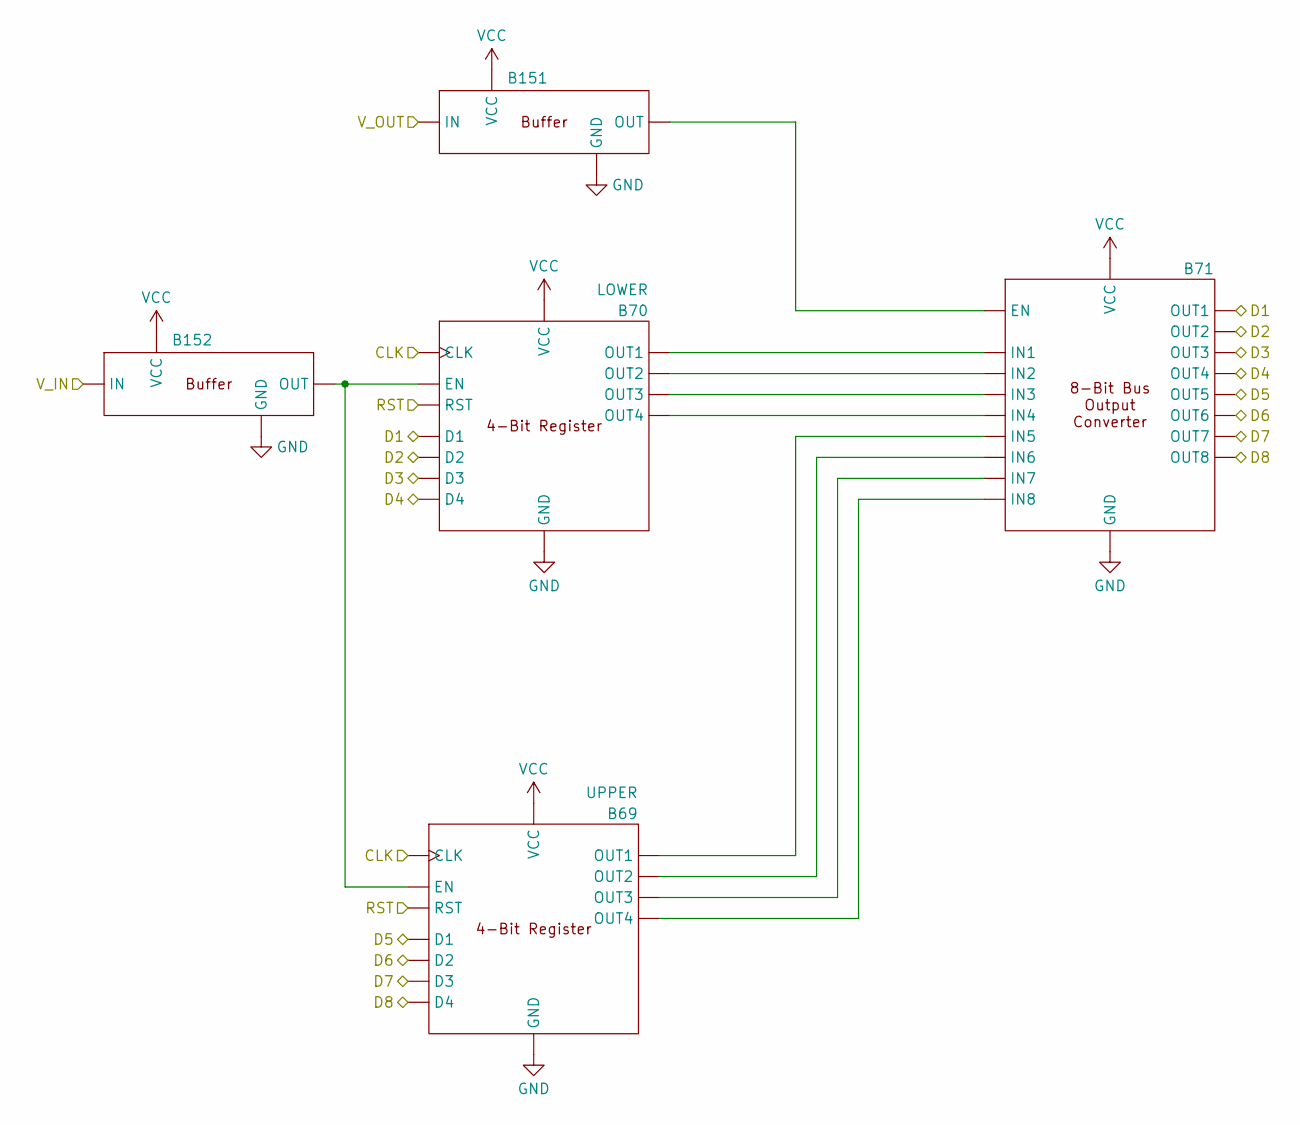
[picture p91: schematic V Register.kicad_sch]

Parts:
B69: UPPER
B70: LOWER
B71, B151, B152: (no value)

Connections:
CLK: B69., B70.
D1: B70., B71.
D2: B70., B71.
D3: B70., B71.
D4: B70., B71.
D5: B69., B71.
D6: B69., B71.
D7: B69., B71.
D8: B69., B71.
GND: B69., B70., B71., B151., B152.
unnamed: B69., B71.
unnamed: B70., B71.
unnamed: B71., B151.
unnamed: B69., B70., B152.
RST: B69., B70.
VCC: B69., B70., B71., B151., B152.
V_IN: B152.
V_OUT: B151.
