DragonMinded/minidragon/bootrom/fixedtest.py

from hardware.serial import (
    serial_init,
    serial_clear,
    serial_send,
    serial_input,
)
from conversion.fixed import strtofixed, fixedtostr


def main() -> void:
    # Initialize hardware.
    serial_init()
    serial_clear()

    # Grab a fixed point decimal number.
    number1: const[str[32]] = serial_input("Enter a number: ", max_length=31, allow_empty=False)
    fixed1: int32 = strtofixed(number1, fracbits=12)

    number2: const[str[32]] = serial_input("Enter another number: ", max_length=31, allow_empty=False)
    fixed2: int32 = strtofixed(number2, fracbits=12)

    approx: const[str] = fixedtostr(fixed1 + fixed2, precision=3, fracbits=12)
    serial_send(f"Approximate addition is: {approx}\n")

    approx2: const[str] = fixedtostr(fixed1 + fixed2, precision=0, fracbits=12)
    serial_send(f"Integer rounded version is: {approx2}\n")

    # Test intrinsics.
    serial_send(f"PI with 8 fraction bits is {fixedtostr(fixed(3.141592654, fracbits=8), precision=2, fracbits=8)}\n")
    serial_send(f"PI with 12 fraction bits is {fixedtostr(fixed(3.141592654, fracbits=12), precision=3, fracbits=12)}\n")
    serial_send(f"PI with 16 fraction bits is {fixedtostr(fixed(3.141592654, fracbits=16), precision=5, fracbits=16)}\n")
